Iowa-Sate-Senior-Design-Dec-2021-Team-7/BBGreenZigbeeCape/docs/concepts/ConceptualSketch.png

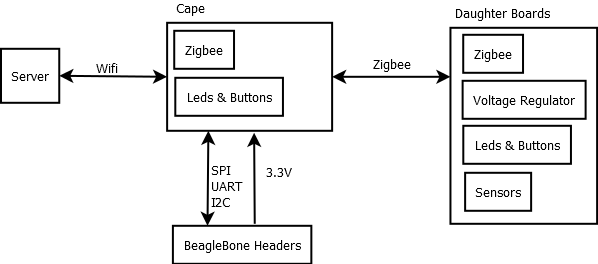
docs/concepts/ConceptualSketch.png
