Iowa-Sate-Senior-Design-Dec-2021-Team-7/BBGreenZigbeeCape/docs/concepts/DetailedHardware.png

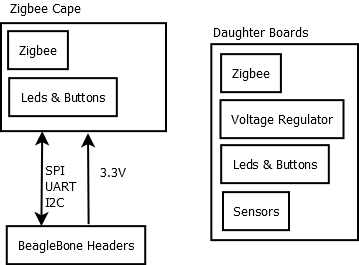
docs/concepts/DetailedHardware.png
