Iowa-Sate-Senior-Design-Dec-2021-Team-7/BBGreenZigbeeCape/hardware/datasheets/Impedance Calcuations/Calculator.PNG

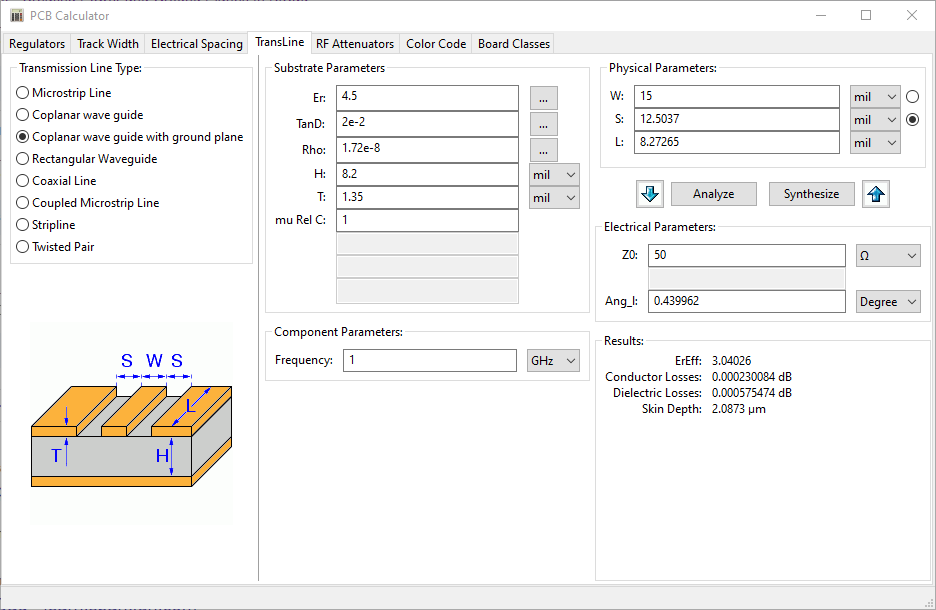
hardware/datasheets/Impedance Calcuations/Calculator.PNG
