Iowa-Sate-Senior-Design-Dec-2021-Team-7/BBGreenZigbeeCape/hardware/datasheets/Impedance Calcuations/StackupInfo.PNG

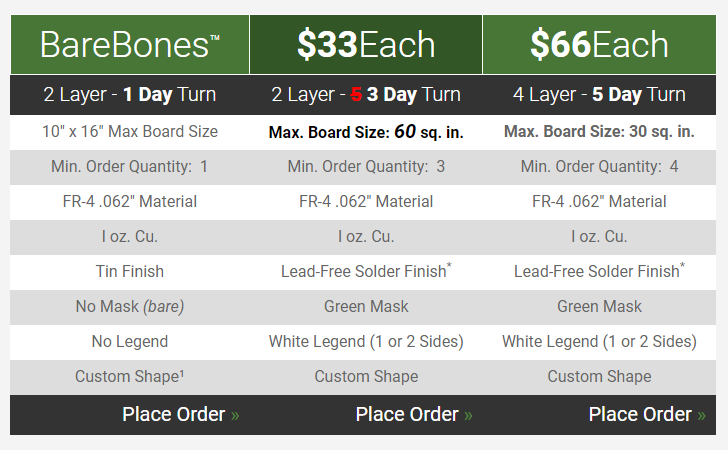
hardware/datasheets/Impedance Calcuations/StackupInfo.PNG
