Iowa-Sate-Senior-Design-Dec-2021-Team-7/BBGreenZigbeeCape/hardware/datasheets/Pictures/Layout.PNG

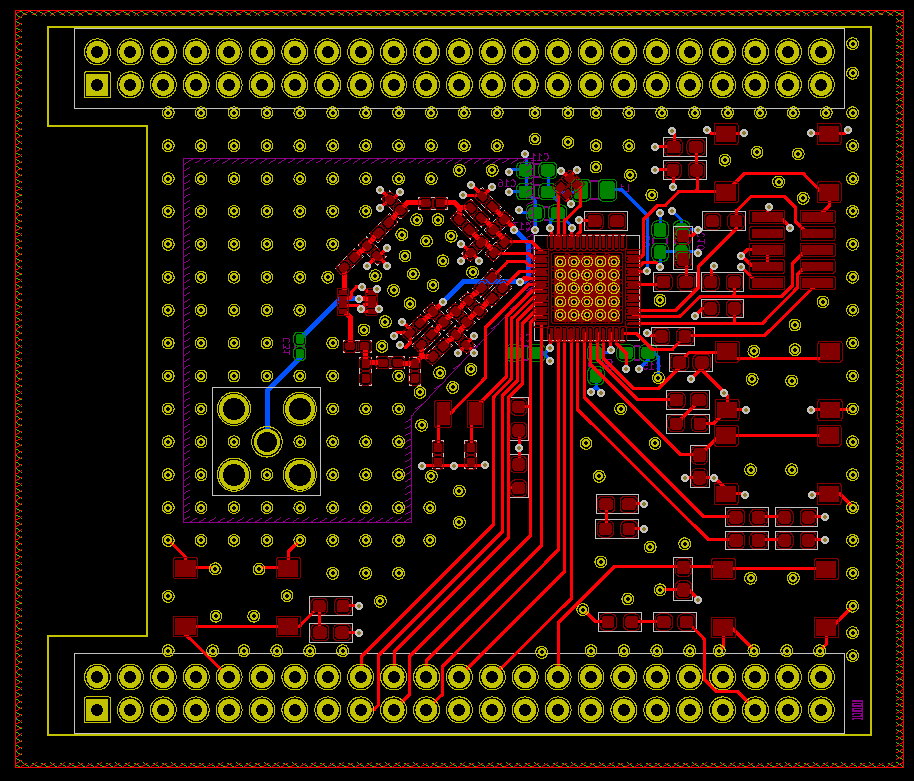
hardware/datasheets/Pictures/Layout.PNG
