Iowa-Sate-Senior-Design-Dec-2021-Team-7/BBGreenZigbeeCape/hardware/datasheets/Pictures/Schematic.PNG

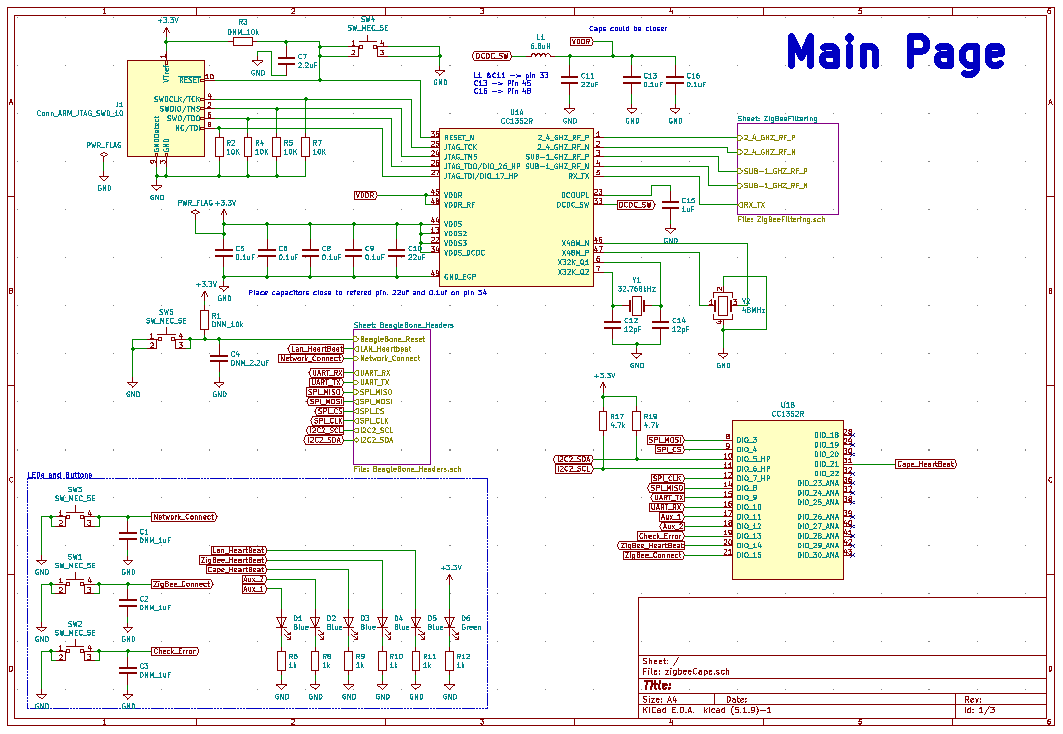
hardware/datasheets/Pictures/Schematic.PNG
