Iowa-Sate-Senior-Design-Dec-2021-Team-7/BBGreenZigbeeCape/hardware/datasheets/Pictures/Switchboard Schematic.PNG

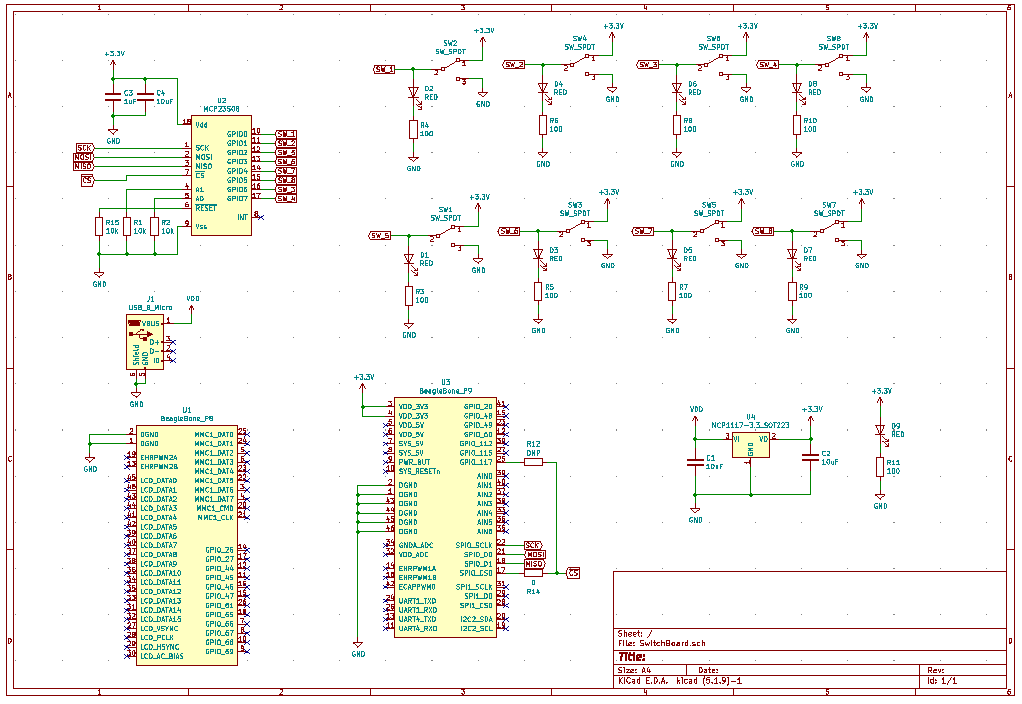
hardware/datasheets/Pictures/Switchboard Schematic.PNG
