Iowa-Sate-Senior-Design-Dec-2021-Team-7/BBGreenZigbeeCape/hardware/datasheets/Pictures/JLC Order.PNG

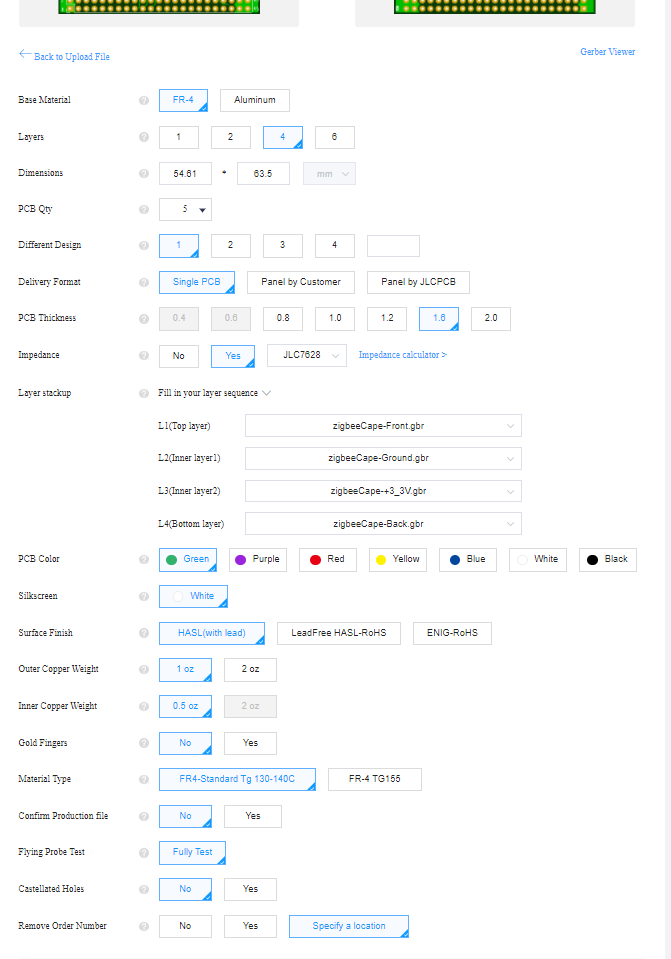
hardware/datasheets/Pictures/JLC Order.PNG
