Iowa-Sate-Senior-Design-Dec-2021-Team-7/BBGreenZigbeeCape/hardware/gerberfiles/ETG Ordering Files/ZigBeeCapeRev2OrderOptions.PNG

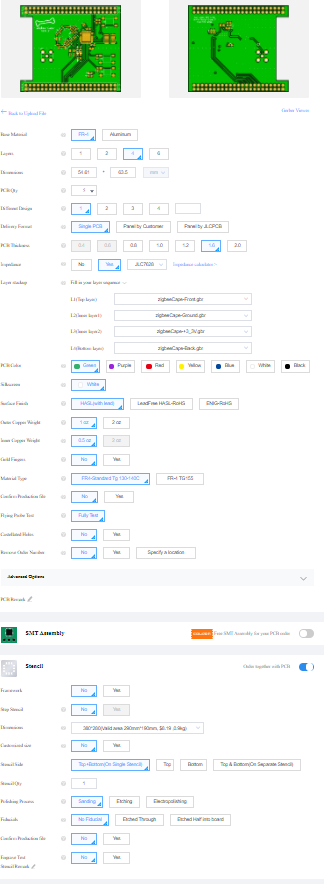
hardware/gerberfiles/ETG Ordering Files/ZigBeeCapeRev2OrderOptions.PNG
