Iowa-Sate-Senior-Design-Dec-2021-Team-7/BBGreenZigbeeCape/hardware/datasheets/Impedance Calcuations/TestBoardLayout.PNG

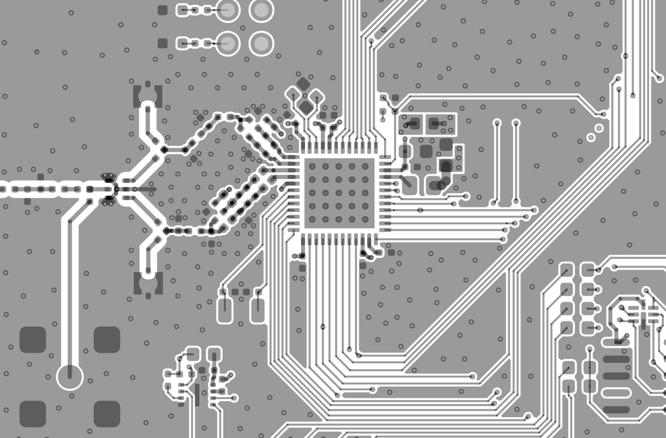
hardware/datasheets/Impedance Calcuations/TestBoardLayout.PNG
