Iowa-Sate-Senior-Design-Dec-2021-Team-7/BBGreenZigbeeCape/firmware/cape/CapeFirmware_P/Application/zcl_samplethermostat.c

/**************************************************************************************************
  Filename:       zcl_samplethermostat.c
  Revised:        $Date: 2014-10-24 16:04:46 -0700 (Fri, 24 Oct 2014) $
  Revision:       $Revision: 40796 $

  Description:    Zigbee Cluster Library - sample device application.

  Copyright 2013 - 2014 Texas Instruments Incorporated. All rights reserved.

  IMPORTANT: Your use of this Software is limited to those specific rights
  granted under the terms of a software license agreement between the user
  who downloaded the software, his/her employer (which must be your employer)
  and Texas Instruments Incorporated (the "License").  You may not use this
  Software unless you agree to abide by the terms of the License. The License
  limits your use, and you acknowledge, that the Software may not be modified,
  copied or distributed unless embedded on a Texas Instruments microcontroller
  or used solely and exclusively in conjunction with a Texas Instruments radio
  frequency transceiver, which is integrated into your product.  Other than for
  the foregoing purpose, you may not use, reproduce, copy, prepare derivative
  works of, modify, distribute, perform, display or sell this Software and/or
  its documentation for any purpose.

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
  Should you have any questions regarding your right to use this Software,
  contact Texas Instruments Incorporated at www.TI.com.
**************************************************************************************************/

/*********************************************************************
  This application implements a ZigBee Thermostat, based on Z-Stack 3.0.

  This application is based on the common sample-application user interface. Please see the main
  comment in zcl_sampleapp_ui.c. The rest of this comment describes only the content specific for
  this sample application.

  Application-specific UI peripherals being used:

  - LEDs:
    LED1:
      - Off: Indicates system is currently off.
      - On: Indicates system is heating.
      - Blinking: Indicates system is cooling.

  Application-specific menu system:
    <SET HEAT TEMP> Changes the heating point temperature
      Up/Down changes the temperature at which heating will activate

    <SET COOL TEMP> Changes the cooling point temperature
      Up/Down changes the temperature at which cooling will activate

    The APP Info line will display the following information:
      [Remote Temperature]
        XXC - current temperature of the remote temperature sensor
        Invalid - thermostat has not yet discovered a temperature sensor
      [System Mode]
        OFF - indicates the system is off
        HEAT - indicates the system is heating
        COOL - indicates the system is cooling
      [Cooling Set Temp]
        XXC - current cooling point temperature
      [Heating Set Temp]
        XXC - current heating point temperature

*********************************************************************/

/*********************************************************************
 * INCLUDES
 */
#include <stdio.h>
#include <stdint.h>
#include <stddef.h>
#include <string.h>

/* POSIX Header files */
#include <pthread.h>
#include <semaphore.h>

/* Driver Header files */
#include <ti/drivers/apps/Button.h>
#include <ti/drivers/apps/LED.h>

#include "rom_jt_154.h"
#include "zcomdef.h"
#include "zcl.h"
#include "zcl_general.h"
#include "zcl_ha.h"
#include "zcl_hvac.h"
#include "zcl_ms.h"
#include "zcl_samplethermostat.h"
#include "bdb_interface.h"

#include "ti_drivers_config.h"
#include "nvintf.h"
#include "zstackmsg.h"
#include "zcl_port.h"

#ifndef CUI_DISABLE
#include "zcl_sampleapps_ui.h"
#include "zcl_sample_app_def.h"
#endif

#include <ti/sysbios/BIOS.h>
#include <ti/sysbios/knl/Semaphore.h>
#include <ti/sysbios/knl/Task.h>
#include <ti/sysbios/knl/Clock.h>
#include "zstackapi.h"
#include "util_timer.h"
#include "mac_util.h"
#include "string.h"

#if !defined (DISABLE_GREENPOWER_BASIC_PROXY) && (ZG_BUILD_RTR_TYPE)
#include "gp_common.h"
#endif

#if defined (ENABLE_GREENPOWER_COMBO_BASIC)
#include "gp_sink.h"
#endif


/*********************************************************************
 * MACROS
 */

/*********************************************************************
 * CONSTANTS
 */
#define THREADSTACKSIZE    1024

/*********************************************************************
 * TYPEDEFS
 */

/*********************************************************************
 * GLOBAL VARIABLES
 */
LED_Handle gRedLedHandle;

/*********************************************************************
 * GLOBAL FUNCTIONS
 */
extern void bb_uartInit();
extern void *bb_uartRead_thread(void *arg0);
extern int_fast32_t bb_uartRead(void *buf, size_t maxCount);
extern int_fast32_t bb_uartWrite(void *buf, size_t count);

/*********************************************************************
 * LOCAL VARIABLES
 */
// Semaphore used to post events to the application thread
static Semaphore_Handle appSemHandle;
static Semaphore_Struct appSem;

/* App service ID used for messaging with stack service task */
static uint8_t  appServiceTaskId;
/* App service task events, set by the stack service task when sending a message */
static uint32_t appServiceTaskEvents;
static endPointDesc_t  zclSampleThermostatEpDesc = {0};

#if ZG_BUILD_ENDDEVICE_TYPE
static Clock_Handle EndDeviceRejoinClkHandle;
static Clock_Struct EndDeviceRejoinClkStruct;
#endif

// Passed in function pointers to the NV driver
static NVINTF_nvFuncts_t *pfnZdlNV = NULL;

#ifndef CUI_DISABLE
static uint16_t zclSampleThermostat_BdbCommissioningModes;
#endif

#ifdef BDB_REPORTING
#if BDBREPORTING_MAX_ANALOG_ATTR_SIZE == 8
  uint8_t reportableChange[] = {0x2C, 0x01, 0x00, 0x00, 0x00, 0x00, 0x00, 0x00}; // 0x2C01 is 300 in int16_t
#endif
#if BDBREPORTING_MAX_ANALOG_ATTR_SIZE == 4
  uint8_t reportableChange[] = {0x2C, 0x01, 0x00, 0x00}; // 0x2C01 is 300 in int16_t
#endif
#if BDBREPORTING_MAX_ANALOG_ATTR_SIZE == 2
  uint8_t reportableChange[] = {0x2C, 0x01}; // 0x2C01 is 300 in int16_t
#endif
#endif

#ifndef CUI_DISABLE
CONST char zclSampleThermostat_appStr[] = APP_TITLE_STR;
CUI_clientHandle_t gCuiHandle;
static uint32_t gSampleThermostatInfoLine1;
static uint32_t gSampleThermostatInfoLine2;
#endif
/*********************************************************************
 * LOCAL FUNCTIONS
 */

static void zclSampleThermostat_initialization(void);
static void zclSampleThermostat_process_loop(void);
static void zclSampleThermostat_initParameters(void);
static void zclSampleThermostat_processZStackMsgs(zstackmsg_genericReq_t *pMsg);
static void SetupZStackCallbacks(void);
static void zclSampleThermostat_processAfIncomingMsgInd(zstack_afIncomingMsgInd_t *pInMsg);
static void zclSampleThermostat_initializeClocks(void);
#if ZG_BUILD_ENDDEVICE_TYPE
static void zclSampleThermostat_processEndDeviceRejoinTimeoutCallback(UArg a0);
#endif

static void zclSampleThermostat_Init( void );
static void zclSampleThermostat_BasicResetCB( void );

#ifndef CUI_DISABLE
static void zclSampleThermostat_RemoveAppNvmData(void);
static void zclSampleThermostat_processKey(uint8_t key, Button_EventMask buttonEvents);
static void zclSampleThermostat_InitializeStatusLine(CUI_clientHandle_t gCuiHandle);
static void zclSampleThermostat_UpdateStatusLine(void);
#endif

static ZStatus_t zclSampleThermostat_SetpointRaiseLowerCB(zclCmdThermostatSetpointRaiseLowerPayload_t *pCmd);
#ifdef MT_APP_FUNC
static void zclSampleThermostat_ProcessAppMsg( uint8_t srcEP, uint8_t len, uint8_t *msg );
static void zclSampleThermostat_ProcessFoundationMsg( afAddrType_t *dstAddr, uint16_t clusterID,
                                                      zclFrameHdr_t *hdr, zclParseCmd_t *pParseCmd );
#endif

static void zclSampleThermostat_ProcessCommissioningStatus(bdbCommissioningModeMsg_t* bdbCommissioningModeMsg);


// app display functions
void zclSampleThermostat_UiDisplayRefresh(void);
void zclSampleThermostat_UiDisplayMainMode(void);
void zclSampleThermostat_UiDisplayHeatMode(void);
void zclSampleThermostat_UiDisplayCoolMode(void);
void zclSampleThermostat_UiDisplayHelpMode(void);



// Functions to process ZCL Foundation incoming Command/Response messages
static uint8_t zclSampleThermostat_ProcessIncomingMsg( zclIncoming_t *pInMsg);
#ifdef ZCL_READ
static uint8_t zclSampleThermostat_ProcessInReadRspCmd( zclIncoming_t *pInMsg );
#endif
#ifdef ZCL_WRITE
static uint8_t zclSampleThermostat_ProcessInWriteRspCmd( zclIncoming_t *pInMsg );
#endif
#ifdef ZCL_REPORT_DESTINATION_DEVICE
static void zclSampleThermostat_ProcessInReportCmd( zclIncoming_t *pInMsg );
#endif  // ZCL_REPORT_DESTINATION_DEVICE
static uint8_t zclSampleThermostat_ProcessInDefaultRspCmd( zclIncoming_t *pInMsg );

static void zclSampleThermostat_UpdateLedState(void);

#if defined (ENABLE_GREENPOWER_COMBO_BASIC)
static void zclSampleThermostat_GPSink_Identify(zclGpNotification_t *zclGpNotification);
static void zclSampleThermostat_GPSink_ProcessReport(zclGpNotification_t *zclGpNotification);
#endif

/*********************************************************************
 * CONSTANTS
 */

/*********************************************************************
 * ZCL General Profile Callback table
 */
static zclGeneral_AppCallbacks_t zclSampleThermostat_CmdCallbacks =
{
  zclSampleThermostat_BasicResetCB,            // Basic Cluster Reset command
  NULL,                                        // Identfiy cmd
  NULL,                                        // Identify Query command
  NULL,                                        // Identify Query Response command
  NULL,                                        // Identify Trigger Effect command
#ifdef ZCL_ON_OFF
  NULL,                                        // On/Off cluster command
  NULL,                                        // On/Off cluster enhanced command Off with Effect
  NULL,                                        // On/Off cluster enhanced command On with Recall Global Scene
  NULL,                                        // On/Off cluster enhanced command On with Timed Off
#endif
#ifdef ZCL_LEVEL_CTRL
  NULL,                                        // Level Control Move to Level command
  NULL,                                        // Level Control Move command
  NULL,                                        // Level Control Step command
  NULL,                                        // Level Control Stop command
  NULL,                                        // Level Control Move to Closest Frequency Command
#endif
#ifdef ZCL_GROUPS
  NULL,                                        // Group Response commands
#endif
#ifdef ZCL_SCENES
  NULL,                                        // Scene Store Request command
  NULL,                                        // Scene Recall Request command
  NULL,                                        // Scene Response command
#endif
#ifdef ZCL_ALARMS
  NULL,                                        // Alarm (Response) commands
#endif
#ifdef SE_UK_EXT
  NULL,                                        // Get Event Log command
  NULL,                                        // Publish Event Log command
#endif
  NULL,                                        // RSSI Location command
  NULL                                         // RSSI Location Response command
};


static zclHVAC_AppCallbacks_t zclSampleThermostat_HVAC_CmdCallbacks =
{
  zclSampleThermostat_SetpointRaiseLowerCB,    //SetpointRaiseLower
  NULL,    //SetWeeklySchedule
  NULL,    //GetWeeklySchedule
  NULL,    //ClearWeeklySchedule
  NULL,    //GetRelayStatusLog
  NULL,    //GetWeeklyScheduleRsp
  NULL,    //GetRelayStatusLogRsp
};

#if defined (ENABLE_GREENPOWER_COMBO_BASIC)

GpSink_AppCallbacks_t zclSampleThermostat_GpSink_AppCallbacks =
{
#ifdef ZCL_IDENTIFY
    zclSampleThermostat_GPSink_Identify,     //IdentifyCmd;
#endif
#ifdef ZCL_SCENES
    NULL,                               //RecallSceneCmd;
    NULL,                               //StoreSceneCmd;
#endif
#ifdef ZCL_ON_OFF
    NULL,          //OffCmd;
    NULL,           //OnCmd;
    NULL,       //ToggleCmd;
#endif
#ifdef ZCL_LEVEL_CTRL
    NULL,                               //LevelControlStopCmd;
    NULL,                               //MoveUpCmd;
    NULL,                               //MoveDownCmd;
    NULL,                               //StepUpCmd;
    NULL,                               //StepDownCmd;
    NULL,                               //MoveUpWithOnOffCmd;
    NULL,                               //MoveDownWithOnOffCmd;
    NULL,                               //StepUpWithOnOffCmd;
    NULL,                               //StepDownWithOnOffCmd;
#endif
    NULL,                               //MoveHueStopCmd;
    NULL,                               //MoveHueUpCmd;
    NULL,                               //MoveHueDownCmd;
    NULL,                               //StepHueUpCmd;
    NULL,                               //StepHueDownCmd;
    NULL,                               //MoveSaturationStopCmd;
    NULL,                               //MoveSaturationUpCmd;
    NULL,                               //MoveSaturationDownCmd;
    NULL,                               //StepSaturationUpCmd;
    NULL,                               //StepSaturationDownCmd;
    NULL,                               //MoveColorCmd;
    NULL,                               //StepColorCmd;
#ifdef ZCL_DOORLOCK
    NULL,                               //LockDoorCmd;
    NULL,                               //UnlockDoorCmd;
#endif
    zclSampleThermostat_GPSink_ProcessReport,                               //AttributeReportingCmd;
    NULL,                               //MfrSpecificReportingCmd;
    NULL,                               //MultiClusterReportingCmd;
    NULL,                               //MfrSpecificMultiReportingCmd;
    NULL,                               //RequestAttributesCmd;
    NULL,                               //ReadAttributeRspCmd;
    NULL,                               //zclTunnelingCmd;
};
#endif

uint16_t data_light_disp0 = 0;
uint16_t data_light_disp1 = 0;
uint16_t id_light_disp0 = 0;
uint16_t id_light_disp1 = 0;

/*******************************************************************************
 * @fn          sampleApp_task
 *
 * @brief       Application task entry point for the Z-Stack
 *              Sample Application
 *
 * @param       pfnNV - pointer to the NV functions
 *
 * @return      none
 */
void sampleApp_task(NVINTF_nvFuncts_t *pfnNV)
{
  // Save and register the function pointers to the NV drivers
  pfnZdlNV = pfnNV;
  zclport_registerNV(pfnZdlNV, ZCL_PORT_SCENE_TABLE_NV_ID);

  // Initialize application
  zclSampleThermostat_initialization();

  // No return from task process
  zclSampleThermostat_process_loop();
}



/*******************************************************************************
 * @fn          zclSampleThermostat_initialization
 *
 * @brief       Initialize the application
 *
 * @param       none
 *
 * @return      none
 */
static void zclSampleThermostat_initialization(void)
{
    /* Initialize user clocks */
    zclSampleThermostat_initializeClocks();

    /* create semaphores for messages / events
     */
    Semaphore_Params semParam;
    Semaphore_Params_init(&semParam);
    semParam.mode = ti_sysbios_knl_Semaphore_Mode_COUNTING;
    Semaphore_construct(&appSem, 0, &semParam);
    appSemHandle = Semaphore_handle(&appSem);

    appServiceTaskId = OsalPort_registerTask(Task_self(), appSemHandle, &appServiceTaskEvents);

    //Initialize stack
    zclSampleThermostat_Init();
}



/*******************************************************************************
 * @fn      SetupZStackCallbacks
 *
 * @brief   Setup the Zstack Callbacks wanted
 *
 * @param   none
 *
 * @return  none
 */
static void SetupZStackCallbacks(void)
{
    zstack_devZDOCBReq_t zdoCBReq = {0};

    // Register for Callbacks, turn on:
    //  Device State Change,
    //  ZDO Match Descriptor Response,
    zdoCBReq.has_devStateChange = true;
    zdoCBReq.devStateChange = true;

    (void)Zstackapi_DevZDOCBReq(appServiceTaskId, &zdoCBReq);
}



/*********************************************************************
 * @fn          zclSampleThermostat_Init
 *
 * @brief       Initialization function for the zclGeneral layer.
 *
 * @param       none
 *
 * @return      none
 */
static void zclSampleThermostat_Init( void )
{

#ifdef BDB_REPORTING
  zstack_bdbRepAddAttrCfgRecordDefaultToListReq_t  Req = {0};
#endif

  //Register Endpoint
  zclSampleThermostatEpDesc.endPoint = SAMPLETHERMOSTAT_ENDPOINT;
  zclSampleThermostatEpDesc.simpleDesc = &zclSampleThermostat_SimpleDesc;
  zclport_registerEndpoint(appServiceTaskId, &zclSampleThermostatEpDesc);

#if defined (ENABLE_GREENPOWER_COMBO_BASIC)
    zclGp_RegisterCBForGPDCommand(&zclSampleThermostat_GpSink_AppCallbacks);
#endif


  // Register the ZCL General Cluster Library callback functions
  zclGeneral_RegisterCmdCallbacks( SAMPLETHERMOSTAT_ENDPOINT, &zclSampleThermostat_CmdCallbacks );

  // Register the ZCL HVAC Cluster Library callback functions
  zclHVAC_RegisterCmdCallbacks(SAMPLETHERMOSTAT_ENDPOINT,  &zclSampleThermostat_HVAC_CmdCallbacks );

  // Register the Application to receive the unprocessed Foundation command/response messages
  zclport_registerZclHandleExternal(SAMPLETHERMOSTAT_ENDPOINT, zclSampleThermostat_ProcessIncomingMsg);

  // Register the application's attribute list and reset to default values
  zclSampleThermostat_ResetAttributesToDefaultValues();
  zcl_registerAttrList( SAMPLETHERMOSTAT_ENDPOINT, zclSampleThermostat_NumAttributes, zclSampleThermostat_Attrs );

  //Write the bdb initialization parameters
  zclSampleThermostat_initParameters();

  //Setup ZDO callbacks
  SetupZStackCallbacks();

#if defined ( BDB_TL_INITIATOR )
  zclSampleThermostat_BdbCommissioningModes |= BDB_COMMISSIONING_MODE_INITIATOR_TL;
#endif

#if !defined (DISABLE_GREENPOWER_BASIC_PROXY) && (ZG_BUILD_RTR_TYPE)
  gp_endpointInit(appServiceTaskId);
#endif

#ifdef BDB_REPORTING
    //Adds the default configuration values for the reportable attributes of the ZCL_CLUSTER_ID_HVAC_THERMOSTAT cluster, for endpoint SAMPLETHERMOSTAT_ENDPOINT
    //Default maxReportingInterval value is 10 seconds
    //Default minReportingInterval value is 3 seconds
    //Default reportChange value is 300 (3 degrees)

    Req.attrID = ATTRID_THERMOSTAT_LOCAL_TEMPERATURE;
    Req.cluster = ZCL_CLUSTER_ID_HVAC_THERMOSTAT;
    Req.endpoint = SAMPLETHERMOSTAT_ENDPOINT;
    Req.maxReportInt = 10;
    Req.minReportInt =  3;
    OsalPort_memcpy(&Req.reportableChange,reportableChange,BDBREPORTING_MAX_ANALOG_ATTR_SIZE);
    Zstackapi_bdbRepAddAttrCfgRecordDefaultToListReq(appServiceTaskId, &Req);
#endif


#ifndef CUI_DISABLE
  // set up default application BDB commissioning modes based on build type
  if(ZG_BUILD_COORDINATOR_TYPE && ZG_DEVICE_COORDINATOR_TYPE)
  {
    zclSampleThermostat_BdbCommissioningModes = BDB_COMMISSIONING_MODE_NWK_FORMATION | BDB_COMMISSIONING_MODE_NWK_STEERING | BDB_COMMISSIONING_MODE_FINDING_BINDING;
  }
  else if (ZG_BUILD_JOINING_TYPE && ZG_DEVICE_JOINING_TYPE)
  {
    zclSampleThermostat_BdbCommissioningModes = BDB_COMMISSIONING_MODE_NWK_STEERING | BDB_COMMISSIONING_MODE_FINDING_BINDING;
  }


  gCuiHandle = UI_Init( appServiceTaskId,                     // Application Task ID
            &appServiceTaskEvents,                // The events processed by the sample application
            appSemHandle,                         // Semaphore to post the events in the application thread
            &zclSampleThermostat_IdentifyTime,
            &zclSampleThermostat_BdbCommissioningModes,   // A pointer to the application's bdbCommissioningModes
            zclSampleThermostat_appStr,                   // A pointer to the app-specific name string
            zclSampleThermostat_processKey,               // A pointer to the app-specific key process function
            zclSampleThermostat_RemoveAppNvmData          // A pointer to the app-specific NV Item reset function
            );

  //Request the Red LED for App
    LED_Params ledParams;
    LED_Params_init(&ledParams);
    gRedLedHandle = LED_open(CONFIG_LED_RED, &ledParams);

   // initialize bb uart handle and connection
   bb_uartInit();

   /*
    * BB uart pthread creation
    */
   pthread_t           thread_bb_uartRead;
   pthread_attr_t      thread_bb_uartRead_attrs;
   struct sched_param  priParam;
   int                 retc;

   /* Initialize the attributes structure with default values */
   pthread_attr_init(&thread_bb_uartRead_attrs);
   /* Set priority, detach state, and stack size attributes */
   priParam.sched_priority = 1;
   retc = pthread_attr_setschedparam(&thread_bb_uartRead_attrs, &priParam);
   retc |= pthread_attr_setdetachstate(&thread_bb_uartRead_attrs, PTHREAD_CREATE_DETACHED);
   retc |= pthread_attr_setstacksize(&thread_bb_uartRead_attrs, THREADSTACKSIZE);
   if (retc != 0) {
       /* failed to set attributes */
       LED_startBlinking(gRedLedHandle, 3000, LED_BLINK_FOREVER);
   }

   // create read thread
   retc = pthread_create(&thread_bb_uartRead, &thread_bb_uartRead_attrs, bb_uartRead_thread, NULL);
   if (retc != 0) {
       /* pthread_create() failed */
       LED_startBlinking(gRedLedHandle, 1000, LED_BLINK_FOREVER);
   }

  //Initialize the SampleDoorLock UI status line
  zclSampleThermostat_InitializeStatusLine(gCuiHandle);
#endif
#if !defined (DISABLE_GREENPOWER_BASIC_PROXY) && (ZG_BUILD_RTR_TYPE)
  app_Green_Power_Init(appServiceTaskId, &appServiceTaskEvents, appSemHandle, SAMPLEAPP_PROCESS_GP_DATA_SEND_EVT,
                       SAMPLEAPP_PROCESS_GP_EXPIRE_DUPLICATE_EVT, SAMPLEAPP_PROCESS_GP_TEMP_MASTER_EVT);
#endif

#ifndef CUI_DISABLE
  UI_UpdateBdbStatusLine(NULL);
#endif

  // Call BDB initialization. Should be called once from application at startup to restore
  // previous network configuration, if applicable.
  zstack_bdbStartCommissioningReq_t zstack_bdbStartCommissioningReq;
  zstack_bdbStartCommissioningReq.commissioning_mode = 0;
  Zstackapi_bdbStartCommissioningReq(appServiceTaskId,&zstack_bdbStartCommissioningReq);
}

#ifndef CUI_DISABLE
/*********************************************************************
 * @fn          zclSampleThermostat_RemoveAppNvmData
 *
 * @brief       Callback when Application performs reset to Factory New Reset.
 *              Application must restore the application to default values
 *
 * @param       none
 *
 * @return      none
 */
static void zclSampleThermostat_RemoveAppNvmData(void)
{

}
#endif

static void zclSampleThermostat_initParameters(void)
{
    zstack_bdbSetAttributesReq_t zstack_bdbSetAttrReq;

    zstack_bdbSetAttrReq.bdbCommissioningGroupID              = BDB_DEFAULT_COMMISSIONING_GROUP_ID;
    zstack_bdbSetAttrReq.bdbPrimaryChannelSet                 = BDB_DEFAULT_PRIMARY_CHANNEL_SET;
    zstack_bdbSetAttrReq.bdbScanDuration                      = BDB_DEFAULT_SCAN_DURATION;
    zstack_bdbSetAttrReq.bdbSecondaryChannelSet               = BDB_DEFAULT_SECONDARY_CHANNEL_SET;
    zstack_bdbSetAttrReq.has_bdbCommissioningGroupID          = TRUE;
    zstack_bdbSetAttrReq.has_bdbPrimaryChannelSet             = TRUE;
    zstack_bdbSetAttrReq.has_bdbScanDuration                  = TRUE;
    zstack_bdbSetAttrReq.has_bdbSecondaryChannelSet           = TRUE;
#if (ZG_BUILD_COORDINATOR_TYPE)
    zstack_bdbSetAttrReq.has_bdbJoinUsesInstallCodeKey        = TRUE;
    zstack_bdbSetAttrReq.has_bdbTrustCenterNodeJoinTimeout    = TRUE;
    zstack_bdbSetAttrReq.has_bdbTrustCenterRequireKeyExchange = TRUE;
    zstack_bdbSetAttrReq.bdbJoinUsesInstallCodeKey            = BDB_DEFAULT_JOIN_USES_INSTALL_CODE_KEY;
    zstack_bdbSetAttrReq.bdbTrustCenterNodeJoinTimeout        = BDB_DEFAULT_TC_NODE_JOIN_TIMEOUT;
    zstack_bdbSetAttrReq.bdbTrustCenterRequireKeyExchange     = BDB_DEFAULT_TC_REQUIRE_KEY_EXCHANGE;
#endif
#if (ZG_BUILD_JOINING_TYPE)
    zstack_bdbSetAttrReq.has_bdbTCLinkKeyExchangeAttemptsMax  = TRUE;
    zstack_bdbSetAttrReq.has_bdbTCLinkKeyExchangeMethod       = TRUE;
    zstack_bdbSetAttrReq.bdbTCLinkKeyExchangeAttemptsMax      = BDB_DEFAULT_TC_LINK_KEY_EXCHANGE_ATTEMPS_MAX;
    zstack_bdbSetAttrReq.bdbTCLinkKeyExchangeMethod           = BDB_DEFAULT_TC_LINK_KEY_EXCHANGE_METHOD;
#endif

    Zstackapi_bdbSetAttributesReq(appServiceTaskId, &zstack_bdbSetAttrReq);
}

/*******************************************************************************
 * @fn      zclSampleThermostat_initializeClocks
 *
 * @brief   Initialize Clocks
 *
 * @param   none
 *
 * @return  none
 */
static void zclSampleThermostat_initializeClocks(void)
{
#if ZG_BUILD_ENDDEVICE_TYPE
    // Initialize the timers needed for this application
    EndDeviceRejoinClkHandle = UtilTimer_construct(
    &EndDeviceRejoinClkStruct,
    zclSampleThermostat_processEndDeviceRejoinTimeoutCallback,
    SAMPLEAPP_END_DEVICE_REJOIN_DELAY,
    0, false, 0);
#endif

}

#if ZG_BUILD_ENDDEVICE_TYPE
/*******************************************************************************
 * @fn      zclSampleThermostat_processEndDeviceRejoinTimeoutCallback
 *
 * @brief   Timeout handler function
 *
 * @param   a0 - ignored
 *
 * @return  none
 */
static void zclSampleThermostat_processEndDeviceRejoinTimeoutCallback(UArg a0)
{
    (void)a0; // Parameter is not used

    appServiceTaskEvents |= SAMPLEAPP_END_DEVICE_REJOIN_EVT;

    // Wake up the application thread when it waits for clock event
    Semaphore_post(appSemHandle);
}
#endif


/*******************************************************************************
 * @fn      zclSampleThermostat_process_loop
 *
 * @brief   Application task processing start.
 *
 * @param   none
 *
 * @return  void
 */
static void zclSampleThermostat_process_loop(void)
{
    /* Forever loop */
    for(;;)
    {
        zstackmsg_genericReq_t *pMsg = NULL;
        bool msgProcessed = FALSE;

        /* Wait for response message */
        if(Semaphore_pend(appSemHandle, BIOS_WAIT_FOREVER ))
        {
            /* Retrieve the response message */
            if( (pMsg = (zstackmsg_genericReq_t*) OsalPort_msgReceive( appServiceTaskId )) != NULL)
            {
                /* Process the message from the stack */
                zclSampleThermostat_processZStackMsgs(pMsg);
                // Free any separately allocated memory
                msgProcessed = Zstackapi_freeIndMsg(pMsg);
            }

            if((msgProcessed == FALSE) && (pMsg != NULL))
            {
                OsalPort_msgDeallocate((uint8_t*)pMsg);
            }

#ifndef CUI_DISABLE
            //Process the events that the UI may have
            zclsampleApp_ui_event_loop();
#endif

#if !defined (DISABLE_GREENPOWER_BASIC_PROXY) && (ZG_BUILD_RTR_TYPE)
            if(appServiceTaskEvents & SAMPLEAPP_PROCESS_GP_DATA_SEND_EVT)
            {
                if(zgGP_ProxyCommissioningMode == TRUE)
                {
                  zcl_gpSendCommissioningNotification();
                }
                else
                {
                  zcl_gpSendNotification();
                }
                appServiceTaskEvents &= ~SAMPLEAPP_PROCESS_GP_DATA_SEND_EVT;
            }

            if(appServiceTaskEvents & SAMPLEAPP_PROCESS_GP_EXPIRE_DUPLICATE_EVT)
            {
                gp_expireDuplicateFiltering();
                appServiceTaskEvents &= ~SAMPLEAPP_PROCESS_GP_EXPIRE_DUPLICATE_EVT;
            }

            if(appServiceTaskEvents & SAMPLEAPP_PROCESS_GP_TEMP_MASTER_EVT)
            {
                gp_returnOperationalChannel();
                appServiceTaskEvents &= ~SAMPLEAPP_PROCESS_GP_TEMP_MASTER_EVT;
            }
#endif

#if ZG_BUILD_ENDDEVICE_TYPE
            if ( appServiceTaskEvents & SAMPLEAPP_END_DEVICE_REJOIN_EVT )
            {
              zstack_bdbRecoverNwkRsp_t zstack_bdbRecoverNwkRsp;

              Zstackapi_bdbRecoverNwkReq(appServiceTaskId,&zstack_bdbRecoverNwkRsp);

              appServiceTaskEvents &= ~SAMPLEAPP_END_DEVICE_REJOIN_EVT;
            }
#endif

#ifndef CUI_DISABLE
            //Update status line
            zclSampleThermostat_UpdateStatusLine();
#endif
            zclSampleThermostat_UpdateLedState();
        }
    }

}




/*******************************************************************************
 * @fn      zclSampleThermostat_processZStackMsgs
 *
 * @brief   Process event from Stack
 *
 * @param   pMsg - pointer to incoming ZStack message to process
 *
 * @return  void
 */
static void zclSampleThermostat_processZStackMsgs(zstackmsg_genericReq_t *pMsg)
{
    switch(pMsg->hdr.event)
    {
        case zstackmsg_CmdIDs_BDB_NOTIFICATION:
            {
                zstackmsg_bdbNotificationInd_t *pInd;
                pInd = (zstackmsg_bdbNotificationInd_t*)pMsg;
                zclSampleThermostat_ProcessCommissioningStatus(&(pInd->Req));
            }
            break;

        case zstackmsg_CmdIDs_BDB_IDENTIFY_TIME_CB:
            {
#ifndef CUI_DISABLE
                zstackmsg_bdbIdentifyTimeoutInd_t *pInd;
                pInd = (zstackmsg_bdbIdentifyTimeoutInd_t*) pMsg;
                uiProcessIdentifyTimeChange(&(pInd->EndPoint));
#endif
            }
            break;

        case zstackmsg_CmdIDs_BDB_BIND_NOTIFICATION_CB:
            {
#ifndef CUI_DISABLE
                zstackmsg_bdbBindNotificationInd_t *pInd;
                pInd = (zstackmsg_bdbBindNotificationInd_t*) pMsg;
                uiProcessBindNotification(&(pInd->Req));
#endif
            }
            break;

        case zstackmsg_CmdIDs_AF_INCOMING_MSG_IND:
            {
                // Process incoming data messages
                zstackmsg_afIncomingMsgInd_t *pInd;
                pInd = (zstackmsg_afIncomingMsgInd_t *)pMsg;
                zclSampleThermostat_processAfIncomingMsgInd( &(pInd->req) );
            }
            break;

#if (ZG_BUILD_JOINING_TYPE)
        case zstackmsg_CmdIDs_BDB_CBKE_TC_LINK_KEY_EXCHANGE_IND:
        {
          zstack_bdbCBKETCLinkKeyExchangeAttemptReq_t zstack_bdbCBKETCLinkKeyExchangeAttemptReq;
          /* Z3.0 has not defined CBKE yet, so lets attempt default TC Link Key exchange procedure
           * by reporting CBKE failure.
           */

          zstack_bdbCBKETCLinkKeyExchangeAttemptReq.didSuccess = FALSE;

          Zstackapi_bdbCBKETCLinkKeyExchangeAttemptReq(appServiceTaskId,
                                                       &zstack_bdbCBKETCLinkKeyExchangeAttemptReq);
        }
        break;

        case zstackmsg_CmdIDs_BDB_FILTER_NWK_DESCRIPTOR_IND:

         /*   User logic to remove networks that do not want to join
          *   Networks to be removed can be released with Zstackapi_bdbNwkDescFreeReq
          */

          Zstackapi_bdbFilterNwkDescComplete(appServiceTaskId);
        break;

#endif
        case zstackmsg_CmdIDs_DEV_STATE_CHANGE_IND:
#ifndef CUI_DISABLE
          {
            // The ZStack Thread is indicating a State change
            zstackmsg_devStateChangeInd_t *pInd =
                (zstackmsg_devStateChangeInd_t *)pMsg;
                  UI_DeviceStateUpdated(&(pInd->req));
          }
#endif
        break;



        /*
         * These are messages/indications from ZStack that this
         * application doesn't process.  These message can be
         * processed by your application, remove from this list and
         * process them here in this switch statement.
         */

#if !defined (DISABLE_GREENPOWER_BASIC_PROXY) && (ZG_BUILD_RTR_TYPE)
          case zstackmsg_CmdIDs_GP_DATA_IND:
          {
              zstackmsg_gpDataInd_t *pInd;
              pInd = (zstackmsg_gpDataInd_t*)pMsg;
              gp_processDataIndMsg( &(pInd->Req) );
          }
          break;

          case zstackmsg_CmdIDs_GP_SECURITY_REQ:
          {
              zstackmsg_gpSecReq_t *pInd;
              pInd = (zstackmsg_gpSecReq_t*)pMsg;
              gp_processSecRecMsg( &(pInd->Req) );
          }
          break;

          case zstackmsg_CmdIDs_GP_CHECK_ANNCE:
          {
              zstackmsg_gpCheckAnnounce_t *pInd;
              pInd = (zstackmsg_gpCheckAnnounce_t*)pMsg;
              gp_processCheckAnnceMsg( &(pInd->Req) );
          }
          break;

          case zstackmsg_CmdIDs_GP_COMMISSIONING_MODE_IND:
#ifndef CUI_DISABLE
          {
            zstackmsg_gpCommissioningModeInd_t *pInd;
            pInd = (zstackmsg_gpCommissioningModeInd_t*)pMsg;
            UI_SetGPPCommissioningMode( &(pInd->Req) );
          }
#endif
          break;
#endif

#ifdef BDB_TL_TARGET
        case zstackmsg_CmdIDs_BDB_TOUCHLINK_TARGET_ENABLE_IND:
        {
          zstackmsg_bdbTouchLinkTargetEnableInd_t *pInd =
            (zstackmsg_bdbTouchLinkTargetEnableInd_t*)pMsg;

          uiProcessTouchlinkTargetEnable(pInd->Enable);
        }
        break;
#endif
        case zstackmsg_CmdIDs_BDB_TC_LINK_KEY_EXCHANGE_NOTIFICATION_IND:
        case zstackmsg_CmdIDs_AF_DATA_CONFIRM_IND:
        case zstackmsg_CmdIDs_ZDO_DEVICE_ANNOUNCE:
        case zstackmsg_CmdIDs_ZDO_NWK_ADDR_RSP:
        case zstackmsg_CmdIDs_DEV_PERMIT_JOIN_IND:
        case zstackmsg_CmdIDs_ZDO_IEEE_ADDR_RSP:
        case zstackmsg_CmdIDs_ZDO_NODE_DESC_RSP:
        case zstackmsg_CmdIDs_ZDO_POWER_DESC_RSP:
        case zstackmsg_CmdIDs_ZDO_SIMPLE_DESC_RSP:
        case zstackmsg_CmdIDs_ZDO_ACTIVE_EP_RSP:
        case zstackmsg_CmdIDs_ZDO_COMPLEX_DESC_RSP:
        case zstackmsg_CmdIDs_ZDO_USER_DESC_RSP:
        case zstackmsg_CmdIDs_ZDO_USER_DESC_SET_RSP:
        case zstackmsg_CmdIDs_ZDO_SERVER_DISC_RSP:
        case zstackmsg_CmdIDs_ZDO_END_DEVICE_BIND_RSP:
        case zstackmsg_CmdIDs_ZDO_BIND_RSP:
        case zstackmsg_CmdIDs_ZDO_UNBIND_RSP:
        case zstackmsg_CmdIDs_ZDO_MGMT_NWK_DISC_RSP:
        case zstackmsg_CmdIDs_ZDO_MGMT_LQI_RSP:
        case zstackmsg_CmdIDs_ZDO_MGMT_RTG_RSP:
        case zstackmsg_CmdIDs_ZDO_MGMT_BIND_RSP:
        case zstackmsg_CmdIDs_ZDO_MGMT_LEAVE_RSP:
        case zstackmsg_CmdIDs_ZDO_MGMT_DIRECT_JOIN_RSP:
        case zstackmsg_CmdIDs_ZDO_MGMT_PERMIT_JOIN_RSP:
        case zstackmsg_CmdIDs_ZDO_MGMT_NWK_UPDATE_NOTIFY:
        case zstackmsg_CmdIDs_ZDO_SRC_RTG_IND:
        case zstackmsg_CmdIDs_ZDO_CONCENTRATOR_IND:
        case zstackmsg_CmdIDs_ZDO_LEAVE_CNF:
        case zstackmsg_CmdIDs_ZDO_LEAVE_IND:
        case zstackmsg_CmdIDs_SYS_RESET_IND:
        case zstackmsg_CmdIDs_AF_REFLECT_ERROR_IND:
        case zstackmsg_CmdIDs_ZDO_TC_DEVICE_IND:
            break;

        default:
            break;
    }
}



/*******************************************************************************
 *
 * @fn          zclSampleThermostat_processAfIncomingMsgInd
 *
 * @brief       Process AF Incoming Message Indication message
 *
 * @param       pInMsg - pointer to incoming message
 *
 * @return      none
 *
 */
static void zclSampleThermostat_processAfIncomingMsgInd(zstack_afIncomingMsgInd_t *pInMsg)
{
    afIncomingMSGPacket_t afMsg;

    /*
     * All incoming messages are passed to the ZCL message processor,
     * first convert to a structure that ZCL can process.
     */
    afMsg.groupId = pInMsg->groupID;
    afMsg.clusterId = pInMsg->clusterId;
    afMsg.srcAddr.endPoint = pInMsg->srcAddr.endpoint;
    afMsg.srcAddr.panId = pInMsg->srcAddr.panID;
    afMsg.srcAddr.addrMode = (afAddrMode_t)pInMsg->srcAddr.addrMode;
    if( (afMsg.srcAddr.addrMode == afAddr16Bit)
        || (afMsg.srcAddr.addrMode == afAddrGroup)
        || (afMsg.srcAddr.addrMode == afAddrBroadcast) )
    {
        afMsg.srcAddr.addr.shortAddr = pInMsg->srcAddr.addr.shortAddr;
    }
    else if(afMsg.srcAddr.addrMode == afAddr64Bit)
    {
        OsalPort_memcpy(afMsg.srcAddr.addr.extAddr, &(pInMsg->srcAddr.addr.extAddr), 8);
    }
    afMsg.macDestAddr = pInMsg->macDestAddr;
    afMsg.endPoint = pInMsg->endpoint;
    afMsg.wasBroadcast = pInMsg->wasBroadcast;
    afMsg.LinkQuality = pInMsg->linkQuality;
    afMsg.correlation = pInMsg->correlation;
    afMsg.rssi = pInMsg->rssi;
    afMsg.SecurityUse = pInMsg->securityUse;
    afMsg.timestamp = pInMsg->timestamp;
    afMsg.nwkSeqNum = pInMsg->nwkSeqNum;
    afMsg.macSrcAddr = pInMsg->macSrcAddr;
    afMsg.radius = pInMsg->radius;
    afMsg.cmd.DataLength = pInMsg->n_payload;
    afMsg.cmd.Data = pInMsg->pPayload;

    zcl_ProcessMessageMSG(&afMsg);
}




/*********************************************************************
 * @fn      zclSampleThermostat_BasicResetCB
 *
 * @brief   Callback from the ZCL General Cluster Library
 *          to set all the Basic Cluster attributes to default values.
 *
 * @param   none
 *
 * @return  none
 */
static void zclSampleThermostat_BasicResetCB( void )
{
  zclSampleThermostat_ResetAttributesToDefaultValues();

#ifndef CUI_DISABLE
  UI_UpdateBdbStatusLine(NULL);
#endif
  zclSampleThermostat_UpdateLedState();
}




/*********************************************************************
 * @fn      zclSampleThermostat_SetpointRaiseLowerCB
 *
 * @brief   Callback from the ZCL HVAC Cluster Library
 *          to increase/decrease the Cooling/heating setpoint.
 *
 * @param   none
 *
 * @return  none
 */
static ZStatus_t zclSampleThermostat_SetpointRaiseLowerCB(zclCmdThermostatSetpointRaiseLowerPayload_t *pCmd)
{
  int16_t temp = pCmd->amount * 10;

  if((pCmd->mode == HVAC_THERMOSTAT_MODE_HEAT) || (pCmd->mode == HVAC_THERMOSTAT_MODE_BOTH))
  {
    if(zclSampleThermostat_OccupiedHeatingSetpoint + temp < zclSampleThermostat_AbsMinHeatSetpointLimit)
    {
      zclSampleThermostat_OccupiedHeatingSetpoint = zclSampleThermostat_AbsMinHeatSetpointLimit;
    }
    else if (zclSampleThermostat_OccupiedHeatingSetpoint + temp > zclSampleThermostat_AbsMaxHeatSetpointLimit)
    {
      zclSampleThermostat_OccupiedHeatingSetpoint = zclSampleThermostat_AbsMaxHeatSetpointLimit;
    }
    else
    {
      zclSampleThermostat_OccupiedHeatingSetpoint += temp;
    }
  }
  if((pCmd->mode == HVAC_THERMOSTAT_MODE_COOL) || (pCmd->mode == HVAC_THERMOSTAT_MODE_BOTH))
  {
    if(zclSampleThermostat_OccupiedCoolingSetpoint + temp < zclSampleThermostat_AbsMinCoolSetpointLimit)
    {
      zclSampleThermostat_OccupiedCoolingSetpoint = zclSampleThermostat_AbsMinCoolSetpointLimit;
    }
    else if (zclSampleThermostat_OccupiedCoolingSetpoint + temp > zclSampleThermostat_AbsMaxCoolSetpointLimit)
    {
      zclSampleThermostat_OccupiedCoolingSetpoint = zclSampleThermostat_AbsMaxCoolSetpointLimit;
    }
    else
    {
      zclSampleThermostat_OccupiedCoolingSetpoint += temp;
    }
  }

  return ZSuccess;
}

/******************************************************************************
 *
 *  Functions for processing ZCL Foundation incoming Command/Response messages
 *
 *****************************************************************************/

/*********************************************************************
 * @fn      zclSampleThermostat_ProcessIncomingMsg
 *
 * @brief   Process ZCL Foundation incoming message
 *
 * @param   pInMsg - pointer to the received message
 *
 * @return  uint8_t - TRUE if got handled
 */
static uint8_t zclSampleThermostat_ProcessIncomingMsg( zclIncoming_t *pInMsg)
{
  uint8_t handled = FALSE;
  switch ( pInMsg->hdr.commandID )
  {
#ifdef ZCL_READ
    case ZCL_CMD_READ_RSP:
      zclSampleThermostat_ProcessInReadRspCmd( pInMsg );
      handled = TRUE;
      break;
#endif
#ifdef ZCL_WRITE
    case ZCL_CMD_WRITE_RSP:
      zclSampleThermostat_ProcessInWriteRspCmd( pInMsg );
      handled = TRUE;
      break;
#endif
#ifdef ZCL_REPORT
    case ZCL_CMD_CONFIG_REPORT:
      //zclSampleThermostat_ProcessInConfigReportCmd( pInMsg );
      break;

    case ZCL_CMD_CONFIG_REPORT_RSP:
      //zclSampleThermostat_ProcessInConfigReportRspCmd( pInMsg );
      break;

    case ZCL_CMD_READ_REPORT_CFG:
      //zclSampleThermostat_ProcessInReadReportCfgCmd( pInMsg );
      break;

    case ZCL_CMD_READ_REPORT_CFG_RSP:
      //zclSampleThermostat_ProcessInReadReportCfgRspCmd( pInMsg );
      break;
#endif
#ifdef ZCL_REPORT_DESTINATION_DEVICE
    case ZCL_CMD_REPORT:
      zclSampleThermostat_ProcessInReportCmd( pInMsg );
      handled = TRUE;
      break;
#endif
    case ZCL_CMD_DEFAULT_RSP:
      zclSampleThermostat_ProcessInDefaultRspCmd( pInMsg );
      handled = TRUE;
      break;

    default:
      break;
  }

  return handled;
}


#ifdef ZCL_READ
/*********************************************************************
 * @fn      zclSampleThermostat_ProcessInReadRspCmd
 *
 * @brief   Process the "Profile" Read Response Command
 *
 * @param   pInMsg - incoming message to process
 *
 * @return  none
 */
static uint8_t zclSampleThermostat_ProcessInReadRspCmd( zclIncoming_t *pInMsg )
{
  zclReadRspCmd_t *readRspCmd;
  uint8_t i;

  readRspCmd = (zclReadRspCmd_t *)pInMsg->attrCmd;
  for (i = 0; i < readRspCmd->numAttr; i++)
  {
    // Notify the originator of the results of the original read attributes
    // attempt and, for each successfull request, the value of the requested
    // attribute
  }

  return ( TRUE );
}
#endif // ZCL_READ

#ifdef ZCL_WRITE
/*********************************************************************
 * @fn      zclSampleThermostat_ProcessInWriteRspCmd
 *
 * @brief   Process the "Profile" Write Response Command
 *
 * @param   pInMsg - incoming message to process
 *
 * @return  none
 */
static uint8_t zclSampleThermostat_ProcessInWriteRspCmd( zclIncoming_t *pInMsg )
{
  zclWriteRspCmd_t *writeRspCmd;
  uint8_t i;

  writeRspCmd = (zclWriteRspCmd_t *)pInMsg->attrCmd;
  for (i = 0; i < writeRspCmd->numAttr; i++)
  {
    // Notify the device of the results of the its original write attributes
    // command.
  }

  return ( TRUE );
}
#endif // ZCL_WRITE

#ifdef ZCL_REPORT_DESTINATION_DEVICE
/*********************************************************************
 * @fn      zclSampleThermostat_ProcessInReportCmd
 *
 * @brief   Process the "Profile" Report Command
 *
 * @param   pInMsg - incoming message to process
 *
 * @return  none
 */
static void zclSampleThermostat_ProcessInReportCmd( zclIncoming_t *pInMsg )
{
  zclReportCmd_t *pInTempSensorReport;

  pInTempSensorReport = (zclReportCmd_t *)pInMsg->attrCmd;
  char uartOut[128];
  int uartWrite = 0;

  char *json_deviceId = "\"device_id\"";
  char *json_deviceType = "\"device_type\"";
  char *json_datatype = "\"type\"";
  char *json_value = "\"value\"";

  switch (pInTempSensorReport->attrList[0].attrID) {
  case ATTRID_TEMPERATURE_MEASUREMENT_MEASURED_VALUE:
      // store the current temperature value sent over the air from temperature sensor
      zclSampleThermostat_LocalTemperature = BUILD_UINT16(pInTempSensorReport->attrList[0].attrData[0], pInTempSensorReport->attrList[0].attrData[1]);
      break;
  case CUSTOM_LIGHT:
      data_light = BUILD_UINT16(pInTempSensorReport->attrList[0].attrData[0], pInTempSensorReport->attrList[0].attrData[1]);
      sprintf(uartOut, "{%s:\"%X\", %s:\"%s\", %s:\"%s\", %s:%d}", json_deviceId, pInMsg->msg->srcAddr.addr.shortAddr, json_deviceType, "SENSOR", json_datatype, "LIGHT", json_value, data_light);
      uartWrite = 1;
      if (pInMsg->msg->srcAddr.addr.shortAddr != 0x4256) {
          id_light_disp0 = pInMsg->msg->srcAddr.addr.shortAddr;
          data_light_disp0 = data_light;
      } else {
          id_light_disp1 = 0x4256;
          data_light_disp1 = data_light;
      }
      break;
  case CUSTOM_TEMP_C:
      data_temp_c = BUILD_UINT16(pInTempSensorReport->attrList[0].attrData[0], pInTempSensorReport->attrList[0].attrData[1]);
      sprintf(uartOut, "{%s:\"%X\", %s:\"%s\", %s:\"%s\", %s:%f}", json_deviceId, pInMsg->msg->srcAddr.addr.shortAddr, json_deviceType, "SENSOR", json_datatype, "TEMP_C", json_value, data_temp_c / 100.0);
      uartWrite = 1;
      break;
  case CUSTOM_HUMID:
      data_humid = BUILD_UINT16(pInTempSensorReport->attrList[0].attrData[0], pInTempSensorReport->attrList[0].attrData[1]);
      sprintf(uartOut, "{%s:\"%X\", %s:\"%s\", %s:\"%s\", %s:%f}", json_deviceId, pInMsg->msg->srcAddr.addr.shortAddr, json_deviceType, "SENSOR", json_datatype, "HUMID", json_value, data_humid / 100.0);
      uartWrite = 1;
      break;
  }
  strcat(uartOut, "\r\n");
  if (uartWrite) { bb_uartWrite(uartOut, strlen(uartOut)); }

#ifndef CUI_DISABLE
  zclSampleThermostat_UpdateStatusLine();
#endif
  zclSampleThermostat_UpdateLedState();
}
#endif  // ZCL_REPORT_DESTINATION_DEVICE

/*********************************************************************
 * @fn      zclSampleThermostat_ProcessInDefaultRspCmd
 *
 * @brief   Process the "Profile" Default Response Command
 *
 * @param   pInMsg - incoming message to process
 *
 * @return  none
 */
static uint8_t zclSampleThermostat_ProcessInDefaultRspCmd( zclIncoming_t *pInMsg )
{
  // zclDefaultRspCmd_t *defaultRspCmd = (zclDefaultRspCmd_t *)pInMsg->attrCmd;

  // Device is notified of the Default Response command.
  (void)pInMsg;

  return ( TRUE );
}




/*********************************************************************
 * @fn      zclSampleThermostat_ProcessCommissioningStatus
 *
 * @brief   Callback in which the status of the commissioning process are reported
 *
 * @param   bdbCommissioningModeMsg - Context message of the status of a commissioning process
 *
 * @return  none
 */
static void zclSampleThermostat_ProcessCommissioningStatus(bdbCommissioningModeMsg_t *bdbCommissioningModeMsg)
{
  switch(bdbCommissioningModeMsg->bdbCommissioningMode)
  {
    case BDB_COMMISSIONING_FORMATION:
      if(bdbCommissioningModeMsg->bdbCommissioningStatus == BDB_COMMISSIONING_SUCCESS)
      {
        //YOUR JOB:
      }
      else
      {
        //Want to try other channels?
        //try with bdb_setChannelAttribute
      }
    break;
    case BDB_COMMISSIONING_NWK_STEERING:
      if(bdbCommissioningModeMsg->bdbCommissioningStatus == BDB_COMMISSIONING_SUCCESS)
      {
        //YOUR JOB:
        //We are on the nwk, what now?
      }
      else
      {
        //See the possible errors for nwk steering procedure
        //No suitable networks found
        //Want to try other channels?
        //try with bdb_setChannelAttribute
      }
    break;
    case BDB_COMMISSIONING_FINDING_BINDING:
      if(bdbCommissioningModeMsg->bdbCommissioningStatus == BDB_COMMISSIONING_SUCCESS)
      {
        //YOUR JOB:
      }
      else
      {
        //YOUR JOB:
        //retry?, wait for user interaction?
      }
    break;
    case BDB_COMMISSIONING_INITIALIZATION:
      //Initialization notification can only be successful. Failure on initialization
      //only happens for ZED and is notified as BDB_COMMISSIONING_PARENT_LOST notification

      //YOUR JOB:
      //We are on a network, what now?

    break;
#if ZG_BUILD_ENDDEVICE_TYPE
    case BDB_COMMISSIONING_PARENT_LOST:
      if(bdbCommissioningModeMsg->bdbCommissioningStatus == BDB_COMMISSIONING_NETWORK_RESTORED)
      {
        //We did recover from losing parent
      }
      else
      {
        //Parent not found, attempt to rejoin again after a fixed delay
        UtilTimer_setTimeout( EndDeviceRejoinClkHandle, SAMPLEAPP_END_DEVICE_REJOIN_DELAY );
        UtilTimer_start(&EndDeviceRejoinClkStruct);
      }
    break;
#endif
  }

#ifndef CUI_DISABLE
  UI_UpdateBdbStatusLine(bdbCommissioningModeMsg);
#endif
}

void zclSampleThermostat_UpdateLedState(void)
{
  // use LEDs to show heating or cooling cycles based off local temperature
  if ( zclSampleThermostat_LocalTemperature != ATTR_INVALID_MEASUREMENT_HVAC_THERMOSTAT_LOCAL_TEMPERATURE )
  {
    if ( zclSampleThermostat_LocalTemperature <= zclSampleThermostat_OccupiedHeatingSetpoint )
    {
      // turn on heating
      zclSampleThermostat_SystemMode = HVAC_THERMOSTAT_SYSTEM_MODE_HEAT;
      //LED_stopBlinking(gRedLedHandle);
      //LED_setOn(gRedLedHandle, LED_BRIGHTNESS_MAX);
    }
    else if ( zclSampleThermostat_LocalTemperature >= zclSampleThermostat_OccupiedCoolingSetpoint )
    {
      // turn on cooling
      zclSampleThermostat_SystemMode = HVAC_THERMOSTAT_SYSTEM_MODE_COOL;
      //LED_startBlinking(gRedLedHandle, 500, LED_BLINK_FOREVER);
    }
    else
    {
      // turn off heating/cooling
      zclSampleThermostat_SystemMode = HVAC_THERMOSTAT_SYSTEM_MODE_OFF;
      //LED_stopBlinking(gRedLedHandle);
      //LED_setOff(gRedLedHandle);
    }
  }
}

#ifndef CUI_DISABLE
void zclSampleThermostat_UiActionSetHeatPoint(const char _input, char* _lines[3], CUI_cursorInfo_t * _curInfos)
{
    if(_input == CUI_INPUT_UP)
    {
        // increase heating setpoint, considering whole numbers where necessary
        if ( zclSampleThermostat_OccupiedHeatingSetpoint < zclSampleThermostat_AbsMaxHeatSetpointLimit )
        {
          zclSampleThermostat_OccupiedHeatingSetpoint = zclSampleThermostat_OccupiedHeatingSetpoint + 100;
        }
        else if ( zclSampleThermostat_OccupiedHeatingSetpoint >= zclSampleThermostat_AbsMaxHeatSetpointLimit )
        {
          zclSampleThermostat_OccupiedHeatingSetpoint = zclSampleThermostat_AbsMaxHeatSetpointLimit;
        }
    }
    else if (_input == CUI_INPUT_DOWN)
    {
        // decrease heating setpoint, considering whole numbers where necessary
        if ( zclSampleThermostat_OccupiedHeatingSetpoint > zclSampleThermostat_AbsMinHeatSetpointLimit )
        {
          zclSampleThermostat_OccupiedHeatingSetpoint = zclSampleThermostat_OccupiedHeatingSetpoint - 100;
        }
        else if ( zclSampleThermostat_OccupiedHeatingSetpoint <= zclSampleThermostat_AbsMinHeatSetpointLimit )
        {
          zclSampleThermostat_OccupiedHeatingSetpoint = zclSampleThermostat_AbsMinHeatSetpointLimit;
        }
    }

    Util_ltoa( ( zclSampleThermostat_OccupiedHeatingSetpoint / 100 ),(uint8_t*) _lines[1], 10 ); // only use whole number
    strcat(_lines[1], " C");
    strcpy(_lines[2], " SET HEAT TEMP ");
}

void zclSampleThermostat_UiActionSetCoolPoint(const char _input, char* _lines[3], CUI_cursorInfo_t * _curInfo)
{
    if(_input == CUI_INPUT_UP)
    {
        // increase cooling setpoint, considering whole numbers where necessary
        if ( zclSampleThermostat_OccupiedCoolingSetpoint < zclSampleThermostat_AbsMaxCoolSetpointLimit )
        {
            zclSampleThermostat_OccupiedCoolingSetpoint = zclSampleThermostat_OccupiedCoolingSetpoint + 100;
        }
        else if ( zclSampleThermostat_OccupiedCoolingSetpoint >= zclSampleThermostat_AbsMaxCoolSetpointLimit )
        {
            zclSampleThermostat_OccupiedCoolingSetpoint = zclSampleThermostat_AbsMaxCoolSetpointLimit;
        }
    }
    else if (_input == CUI_INPUT_DOWN)
    {
        // decrease cooling setpoint, considering whole numbers where necessary
        if ( zclSampleThermostat_OccupiedCoolingSetpoint > zclSampleThermostat_AbsMinCoolSetpointLimit )
        {
            zclSampleThermostat_OccupiedCoolingSetpoint = zclSampleThermostat_OccupiedCoolingSetpoint - 100;
        }
        else if ( zclSampleThermostat_OccupiedCoolingSetpoint <= zclSampleThermostat_AbsMinCoolSetpointLimit )
        {
            zclSampleThermostat_OccupiedCoolingSetpoint = zclSampleThermostat_AbsMinCoolSetpointLimit;
        }
    }

    Util_ltoa( ( zclSampleThermostat_OccupiedCoolingSetpoint / 100 ),(uint8_t*) _lines[1], 10 ); // only use whole number
    strcat(_lines[1], " C");
    strcpy(_lines[2], " SET COOL TEMP ");
}

/*********************************************************************
 * @fn      zclSampleThermostat_processKey
 *
 * @brief   Key event handler function
 *
 * @param   key - key to handle action for
 *          buttonEvents - event to handle action for
 *
 * @return  none
 */
static void zclSampleThermostat_processKey(uint8_t key, Button_EventMask buttonEvents)
{
    if (buttonEvents & Button_EV_CLICKED)
    {
        if(key == CONFIG_BTN_LEFT)
        {
//            zstack_bdbStartCommissioningReq_t zstack_bdbStartCommissioningReq;

//            zstack_bdbStartCommissioningReq.commissioning_mode = zclSampleThermostat_BdbCommissioningModes;
//            Zstackapi_bdbStartCommissioningReq(appServiceTaskId,&zstack_bdbStartCommissioningReq);
        }
    }
}

static void zclSampleThermostat_InitializeStatusLine(CUI_clientHandle_t gCuiHandle)
{
    /* Request Async Line for Light application Info */
    CUI_statusLineResourceRequest(gCuiHandle, "   APP Info"CUI_DEBUG_MSG_START"1"CUI_DEBUG_MSG_END, false, &gSampleThermostatInfoLine1);
    CUI_statusLineResourceRequest(gCuiHandle, "   APP Info"CUI_DEBUG_MSG_START"2"CUI_DEBUG_MSG_END, false, &gSampleThermostatInfoLine2);

    zclSampleThermostat_UpdateStatusLine();
}

static void zclSampleThermostat_UpdateStatusLine(void)
{
    char lineFormat1[MAX_STATUS_LINE_VALUE_LEN] = {'\0'};
    char lineFormat2[MAX_STATUS_LINE_VALUE_LEN] = {'\0'};

    strcat(lineFormat1, "["CUI_COLOR_CYAN"Light Value Device 0x%04x"CUI_COLOR_RESET"] %d lm");
    strcat(lineFormat2, "["CUI_COLOR_CYAN"Light Value Device 0x%04x"CUI_COLOR_RESET"] %d lm");

    if (id_light_disp0) { CUI_statusLinePrintf(gCuiHandle, gSampleThermostatInfoLine1, lineFormat1, id_light_disp0, data_light_disp0); }
    if (id_light_disp1) { CUI_statusLinePrintf(gCuiHandle, gSampleThermostatInfoLine2, lineFormat2, id_light_disp1, data_light_disp1); }
}

#endif

#if defined (ENABLE_GREENPOWER_COMBO_BASIC)
#ifndef CUI_DISABLE
void zclSampleThermostat_setGPSinkCommissioningMode(const int32_t _itemEntry)
{
  bool zclSampleThermostat_SetSinkCommissioningMode = 0;

  //Toggle current commissioning flag value and set that value again
  zclSampleThermostat_SetSinkCommissioningMode = !gp_GetSinkCommissioningMode();
  gp_SetSinkCommissioningMode(zclSampleThermostat_SetSinkCommissioningMode);

  UI_UpdateGpStatusLine();

}
#endif
/*********************************************************************
 * @fn      zclSampleThermostat_GPSink_Identify
 *
 * @brief   Callback to process Identify command from a GPD
 *
 * @param   zclGpNotification
 *
 * @return  none
 */
static void zclSampleThermostat_GPSink_Identify(zclGpNotification_t *zclGpNotification)
{
  afAddrType_t  dstAddr;

  dstAddr.endPoint = SAMPLETHERMOSTAT_ENDPOINT;
  dstAddr.panId = 0;
  dstAddr.addrMode = afAddr16Bit;
  dstAddr.addr.shortAddr = _NIB.nwkDevAddress;

  //Identify is a payloadless command which triggers a 60 seconds identify in the device (doc 14-0563-16 GP spec Table 49)
  zclGeneral_SendIdentify(SAMPLETHERMOSTAT_ENDPOINT,&dstAddr,60,TRUE, 1);
}


/*********************************************************************
 * @fn      zclSampleThermostat_GPSink_ProcessReport
 *
 * @brief   Callback to process Report Attributes command from a GPD
 *
 * @param   zclGpNotification
 *
 * @return  none
 */
static void zclSampleThermostat_GPSink_ProcessReport(zclGpNotification_t *zclGpNotification)
{
  uint16_t        clusterId;
  uint16_t        attrId;
  uint8_t         *pData;

  pData = zclGpNotification->pData;
  //Get the cluster ID
  clusterId = BUILD_UINT16(pData[0], pData[1]);
  pData += sizeof(uint16_t);

  //Point to the attribute report list
  attrId = BUILD_UINT16(pData[0], pData[1]);
  pData += 3;  // attrId + dataType


  if ( (attrId != ATTRID_TEMPERATURE_MEASUREMENT_MEASURED_VALUE) && (clusterId == ZCL_CLUSTER_ID_MS_TEMPERATURE_MEASUREMENT) )
  {
    return;
  }

  // store the current temperature value sent over the air from GPD temperature sensor
  zclSampleThermostat_LocalTemperature = BUILD_UINT16(pData[0], pData[1]);
  zclSampleThermostat_LocalTemperature *= 100;  // to format the temperature correctly

#ifndef CUI_DISABLE
  zclSampleThermostat_UpdateStatusLine();
#endif
  zclSampleThermostat_UpdateLedState();

}


#endif
