Iowa-Sate-Senior-Design-Dec-2021-Team-7/BBGreenZigbeeCape/firmware/daughterboard/tests/zed_temperaturesensor_CC1352R1_LAUNCHXL_tirtos_ccs/default/configPkg/package/cfg/app_pem4f.c

/*
 *  Do not modify this file; it is automatically 
 *  generated and any modifications will be overwritten.
 *
 * @(#) xdc-K04
 */

#define __nested__
#define __config__

#include <xdc/std.h>

/*
 * ======== GENERATED SECTIONS ========
 *
 *     MODULE INCLUDES
 *
 *     <module-name> INTERNALS
 *     <module-name> INHERITS
 *     <module-name> VTABLE
 *     <module-name> PATCH TABLE
 *     <module-name> DECLARATIONS
 *     <module-name> OBJECT OFFSETS
 *     <module-name> TEMPLATES
 *     <module-name> INITIALIZERS
 *     <module-name> FUNCTION STUBS
 *     <module-name> PROXY BODY
 *     <module-name> OBJECT DESCRIPTOR
 *     <module-name> VIRTUAL FUNCTIONS
 *     <module-name> SYSTEM FUNCTIONS
 *     <module-name> PRAGMAS
 *
 *     INITIALIZATION ENTRY POINT
 *     PROGRAM GLOBALS
 *     CLINK DIRECTIVES
 */


/*
 * ======== MODULE INCLUDES ========
 */

#include <ti/sysbios/BIOS.h>
#include <ti/sysbios/family/arm/cc26xx/Boot.h>
#include <ti/sysbios/family/arm/cc26xx/Timer.h>
#include <ti/sysbios/family/arm/cc26xx/TimestampProvider.h>
#include <ti/sysbios/family/arm/m3/Hwi.h>
#include <ti/sysbios/family/arm/m3/IntrinsicsSupport.h>
#include <ti/sysbios/family/arm/m3/TaskSupport.h>
#include <ti/sysbios/gates/GateHwi.h>
#include <ti/sysbios/gates/GateMutex.h>
#include <ti/sysbios/gates/GateMutexPri.h>
#include <ti/sysbios/hal/Hwi.h>
#include <ti/sysbios/heaps/HeapCallback.h>
#include <ti/sysbios/heaps/HeapMem.h>
#include <ti/sysbios/heaps/HeapTrack.h>
#include <ti/sysbios/knl/Clock.h>
#include <ti/sysbios/knl/Event.h>
#include <ti/sysbios/knl/Idle.h>
#include <ti/sysbios/knl/Intrinsics.h>
#include <ti/sysbios/knl/Mailbox.h>
#include <ti/sysbios/knl/Queue.h>
#include <ti/sysbios/knl/Semaphore.h>
#include <ti/sysbios/knl/Swi.h>
#include <ti/sysbios/knl/Task.h>
#include <ti/sysbios/rom/cortexm/cc26xx/cc26x2v2/CC26xx.h>
#include <xdc/runtime/Assert.h>
#include <xdc/runtime/Core.h>
#include <xdc/runtime/Defaults.h>
#include <xdc/runtime/Diags.h>
#include <xdc/runtime/Error.h>
#include <xdc/runtime/Gate.h>
#include <xdc/runtime/Log.h>
#include <xdc/runtime/Main.h>
#include <xdc/runtime/Memory.h>
#include <xdc/runtime/Registry.h>
#include <xdc/runtime/Startup.h>
#include <xdc/runtime/SysCallback.h>
#include <xdc/runtime/System.h>
#include <xdc/runtime/Text.h>
#include <xdc/runtime/Timestamp.h>
#include <xdc/runtime/Types.h>

/* suppress 'type qualifier is meaningless on cast type' warning */
#if defined(__ti__) && !defined(__clang__)
#pragma diag_suppress 193
#endif
#ifdef __IAR_SYSTEMS_ICC__
#pragma diag_suppress=Pe191
#endif

#if !(defined(__GNUC__))
#if !(defined(__TI_GNU_ATTRIBUTE_SUPPORT__) || defined(__IAR_SYSTEMS_ICC__)) || defined(__ARP32__)
#define __attribute__(x)
#endif
#endif

/*
 * ======== ti.sysbios.BIOS INTERNALS ========
 */


/*
 * ======== ti.sysbios.BIOS_RtsGateProxy INTERNALS ========
 */

/* Module__ */
typedef struct ti_sysbios_BIOS_RtsGateProxy_Module__ {
    xdc_runtime_Types_Link link;
} ti_sysbios_BIOS_RtsGateProxy_Module__;

/* Module__root__V */
extern ti_sysbios_BIOS_RtsGateProxy_Module__ ti_sysbios_BIOS_RtsGateProxy_Module__root__V;

/* @@@ ti_sysbios_knl_Queue_Object__ */
typedef struct ti_sysbios_knl_Queue_Object__ {
    ti_sysbios_knl_Queue_Elem elem;
} ti_sysbios_knl_Queue_Object__;

/* @@@ ti_sysbios_knl_Queue_Object2__ */
typedef struct {
    xdc_runtime_Types_InstHdr hdr;
    ti_sysbios_knl_Queue_Object__ obj;
} ti_sysbios_knl_Queue_Object2__;

/* @@@ ti_sysbios_knl_Semaphore_Object__ */
typedef struct ti_sysbios_knl_Semaphore_Object__ {
    ti_sysbios_knl_Event_Handle event;
    xdc_UInt eventId;
    ti_sysbios_knl_Semaphore_Mode mode;
    volatile xdc_UInt16 count;
    ti_sysbios_knl_Queue_Object__ Object_field_pendQ;
} ti_sysbios_knl_Semaphore_Object__;

/* @@@ ti_sysbios_knl_Semaphore_Object2__ */
typedef struct {
    xdc_runtime_Types_InstHdr hdr;
    ti_sysbios_knl_Semaphore_Object__ obj;
} ti_sysbios_knl_Semaphore_Object2__;

/* Object__ */
typedef struct ti_sysbios_gates_GateMutex_Object__ {
    const ti_sysbios_gates_GateMutex_Fxns__ *__fxns;
    ti_sysbios_knl_Task_Handle owner;
    ti_sysbios_knl_Semaphore_Object__ Object_field_sem;
} ti_sysbios_gates_GateMutex_Object__;

/* Object2__ */
typedef struct {
    xdc_runtime_Types_InstHdr hdr;
    ti_sysbios_gates_GateMutex_Object__ obj;
} ti_sysbios_gates_GateMutex_Object2__;

/* Object */
typedef ti_sysbios_gates_GateMutex_Object__ ti_sysbios_BIOS_RtsGateProxy_Object__;

/* Object2__ */
typedef struct {
    xdc_runtime_Types_InstHdr hdr;
    ti_sysbios_BIOS_RtsGateProxy_Object__ obj;
} ti_sysbios_BIOS_RtsGateProxy_Object2__;


/*
 * ======== ti.sysbios.family.arm.cc26xx.Boot INTERNALS ========
 */


/*
 * ======== ti.sysbios.family.arm.cc26xx.Timer INTERNALS ========
 */

/* Module__ */
typedef struct ti_sysbios_family_arm_cc26xx_Timer_Module__ {
    xdc_runtime_Types_Link link;
} ti_sysbios_family_arm_cc26xx_Timer_Module__;

/* Module__root__V */
extern ti_sysbios_family_arm_cc26xx_Timer_Module__ ti_sysbios_family_arm_cc26xx_Timer_Module__root__V;

/* Object__ */
typedef struct ti_sysbios_family_arm_cc26xx_Timer_Object__ {
    const ti_sysbios_family_arm_cc26xx_Timer_Fxns__ *__fxns;
    xdc_Bool staticInst;
    xdc_Int id;
    ti_sysbios_interfaces_ITimer_StartMode startMode;
    xdc_UInt32 period;
    xdc_UArg arg;
    ti_sysbios_family_arm_m3_Hwi_FuncPtr tickFxn;
    xdc_runtime_Types_FreqHz frequency;
    ti_sysbios_family_arm_m3_Hwi_Handle hwi;
    xdc_UInt64 period64;
    xdc_UInt64 savedCurrCount;
    xdc_UInt64 prevThreshold;
    xdc_UInt64 nextThreshold;
} ti_sysbios_family_arm_cc26xx_Timer_Object__;

/* Object2__ */
typedef struct {
    xdc_runtime_Types_InstHdr hdr;
    ti_sysbios_family_arm_cc26xx_Timer_Object__ obj;
} ti_sysbios_family_arm_cc26xx_Timer_Object2__;


/*
 * ======== ti.sysbios.family.arm.cc26xx.TimestampProvider INTERNALS ========
 */


/*
 * ======== ti.sysbios.family.arm.m3.Hwi INTERNALS ========
 */

/* Module__ */
typedef struct ti_sysbios_family_arm_m3_Hwi_Module__ {
    xdc_runtime_Types_Link link;
} ti_sysbios_family_arm_m3_Hwi_Module__;

/* Module__root__V */
extern ti_sysbios_family_arm_m3_Hwi_Module__ ti_sysbios_family_arm_m3_Hwi_Module__root__V;

/* Object__ */
typedef struct ti_sysbios_family_arm_m3_Hwi_Object__ {
    const ti_sysbios_family_arm_m3_Hwi_Fxns__ *__fxns;
    xdc_UArg arg;
    ti_sysbios_family_arm_m3_Hwi_FuncPtr fxn;
    ti_sysbios_family_arm_m3_Hwi_Irp irp;
    xdc_UInt8 priority;
    xdc_Int16 intNum;
    __TA_ti_sysbios_family_arm_m3_Hwi_Instance_State__hookEnv hookEnv;
} ti_sysbios_family_arm_m3_Hwi_Object__;

/* Object2__ */
typedef struct {
    xdc_runtime_Types_InstHdr hdr;
    ti_sysbios_family_arm_m3_Hwi_Object__ obj;
} ti_sysbios_family_arm_m3_Hwi_Object2__;


/*
 * ======== ti.sysbios.family.arm.m3.IntrinsicsSupport INTERNALS ========
 */


/*
 * ======== ti.sysbios.family.arm.m3.TaskSupport INTERNALS ========
 */


/*
 * ======== ti.sysbios.gates.GateHwi INTERNALS ========
 */

/* Module__ */
typedef struct ti_sysbios_gates_GateHwi_Module__ {
    xdc_runtime_Types_Link link;
} ti_sysbios_gates_GateHwi_Module__;

/* Module__root__V */
extern ti_sysbios_gates_GateHwi_Module__ ti_sysbios_gates_GateHwi_Module__root__V;

/* Object__ */
typedef struct ti_sysbios_gates_GateHwi_Object__ {
    const ti_sysbios_gates_GateHwi_Fxns__ *__fxns;
} ti_sysbios_gates_GateHwi_Object__;

/* Object2__ */
typedef struct {
    xdc_runtime_Types_InstHdr hdr;
    ti_sysbios_gates_GateHwi_Object__ obj;
} ti_sysbios_gates_GateHwi_Object2__;


/*
 * ======== ti.sysbios.gates.GateMutex INTERNALS ========
 */

/* Module__ */
typedef struct ti_sysbios_gates_GateMutex_Module__ {
    xdc_runtime_Types_Link link;
} ti_sysbios_gates_GateMutex_Module__;

/* Module__root__V */
extern ti_sysbios_gates_GateMutex_Module__ ti_sysbios_gates_GateMutex_Module__root__V;

/* <-- ti_sysbios_gates_GateMutex_Object */


/*
 * ======== ti.sysbios.gates.GateMutexPri INTERNALS ========
 */

/* Module__ */
typedef struct ti_sysbios_gates_GateMutexPri_Module__ {
    xdc_runtime_Types_Link link;
} ti_sysbios_gates_GateMutexPri_Module__;

/* Module__root__V */
extern ti_sysbios_gates_GateMutexPri_Module__ ti_sysbios_gates_GateMutexPri_Module__root__V;

/* <-- ti_sysbios_knl_Queue_Object */

/* Object__ */
typedef struct ti_sysbios_gates_GateMutexPri_Object__ {
    const ti_sysbios_gates_GateMutexPri_Fxns__ *__fxns;
    volatile xdc_UInt mutexCnt;
    volatile xdc_Int ownerOrigPri;
    volatile ti_sysbios_knl_Task_Handle owner;
    ti_sysbios_knl_Queue_Object__ Object_field_pendQ;
} ti_sysbios_gates_GateMutexPri_Object__;

/* Object2__ */
typedef struct {
    xdc_runtime_Types_InstHdr hdr;
    ti_sysbios_gates_GateMutexPri_Object__ obj;
} ti_sysbios_gates_GateMutexPri_Object2__;


/*
 * ======== ti.sysbios.hal.Hwi INTERNALS ========
 */

/* Module__ */
typedef struct ti_sysbios_hal_Hwi_Module__ {
    xdc_runtime_Types_Link link;
} ti_sysbios_hal_Hwi_Module__;

/* Module__root__V */
extern ti_sysbios_hal_Hwi_Module__ ti_sysbios_hal_Hwi_Module__root__V;

/* Object__ */
typedef struct ti_sysbios_hal_Hwi_Object__ {
    const ti_sysbios_hal_Hwi_Fxns__ *__fxns;
    ti_sysbios_hal_Hwi_HwiProxy_Handle pi;
} ti_sysbios_hal_Hwi_Object__;

/* Object2__ */
typedef struct {
    xdc_runtime_Types_InstHdr hdr;
    ti_sysbios_hal_Hwi_Object__ obj;
} ti_sysbios_hal_Hwi_Object2__;


/*
 * ======== ti.sysbios.hal.Hwi_HwiProxy INTERNALS ========
 */

/* Module__ */
typedef struct ti_sysbios_hal_Hwi_HwiProxy_Module__ {
    xdc_runtime_Types_Link link;
} ti_sysbios_hal_Hwi_HwiProxy_Module__;

/* Module__root__V */
extern ti_sysbios_hal_Hwi_HwiProxy_Module__ ti_sysbios_hal_Hwi_HwiProxy_Module__root__V;

/* <-- ti_sysbios_family_arm_m3_Hwi_Object */

/* Object */
typedef ti_sysbios_family_arm_m3_Hwi_Object__ ti_sysbios_hal_Hwi_HwiProxy_Object__;

/* Object2__ */
typedef struct {
    xdc_runtime_Types_InstHdr hdr;
    ti_sysbios_hal_Hwi_HwiProxy_Object__ obj;
} ti_sysbios_hal_Hwi_HwiProxy_Object2__;


/*
 * ======== ti.sysbios.heaps.HeapCallback INTERNALS ========
 */

/* Module__ */
typedef struct ti_sysbios_heaps_HeapCallback_Module__ {
    xdc_runtime_Types_Link link;
} ti_sysbios_heaps_HeapCallback_Module__;

/* Module__root__V */
extern ti_sysbios_heaps_HeapCallback_Module__ ti_sysbios_heaps_HeapCallback_Module__root__V;

/* Object__ */
typedef struct ti_sysbios_heaps_HeapCallback_Object__ {
    const ti_sysbios_heaps_HeapCallback_Fxns__ *__fxns;
    xdc_UArg context;
    xdc_UArg arg;
} ti_sysbios_heaps_HeapCallback_Object__;

/* Object2__ */
typedef struct {
    xdc_runtime_Types_InstHdr hdr;
    ti_sysbios_heaps_HeapCallback_Object__ obj;
} ti_sysbios_heaps_HeapCallback_Object2__;


/*
 * ======== ti.sysbios.heaps.HeapMem INTERNALS ========
 */

/* Module__ */
typedef struct ti_sysbios_heaps_HeapMem_Module__ {
    xdc_runtime_Types_Link link;
} ti_sysbios_heaps_HeapMem_Module__;

/* Module__root__V */
extern ti_sysbios_heaps_HeapMem_Module__ ti_sysbios_heaps_HeapMem_Module__root__V;

/* Object__ */
typedef struct ti_sysbios_heaps_HeapMem_Object__ {
    const ti_sysbios_heaps_HeapMem_Fxns__ *__fxns;
    xdc_runtime_Memory_Size align;
    __TA_ti_sysbios_heaps_HeapMem_Instance_State__buf buf;
    ti_sysbios_heaps_HeapMem_Header head;
    xdc_SizeT minBlockAlign;
} ti_sysbios_heaps_HeapMem_Object__;

/* Object2__ */
typedef struct {
    xdc_runtime_Types_InstHdr hdr;
    ti_sysbios_heaps_HeapMem_Object__ obj;
} ti_sysbios_heaps_HeapMem_Object2__;


/*
 * ======== ti.sysbios.heaps.HeapMem_Module_GateProxy INTERNALS ========
 */

/* Module__ */
typedef struct ti_sysbios_heaps_HeapMem_Module_GateProxy_Module__ {
    xdc_runtime_Types_Link link;
} ti_sysbios_heaps_HeapMem_Module_GateProxy_Module__;

/* Module__root__V */
extern ti_sysbios_heaps_HeapMem_Module_GateProxy_Module__ ti_sysbios_heaps_HeapMem_Module_GateProxy_Module__root__V;

/* <-- ti_sysbios_gates_GateMutex_Object */

/* Object */
typedef ti_sysbios_gates_GateMutex_Object__ ti_sysbios_heaps_HeapMem_Module_GateProxy_Object__;

/* Object2__ */
typedef struct {
    xdc_runtime_Types_InstHdr hdr;
    ti_sysbios_heaps_HeapMem_Module_GateProxy_Object__ obj;
} ti_sysbios_heaps_HeapMem_Module_GateProxy_Object2__;


/*
 * ======== ti.sysbios.heaps.HeapTrack INTERNALS ========
 */

/* Module__ */
typedef struct ti_sysbios_heaps_HeapTrack_Module__ {
    xdc_runtime_Types_Link link;
} ti_sysbios_heaps_HeapTrack_Module__;

/* Module__root__V */
extern ti_sysbios_heaps_HeapTrack_Module__ ti_sysbios_heaps_HeapTrack_Module__root__V;

/* <-- ti_sysbios_knl_Queue_Object */

/* Object__ */
typedef struct ti_sysbios_heaps_HeapTrack_Object__ {
    const ti_sysbios_heaps_HeapTrack_Fxns__ *__fxns;
    xdc_runtime_IHeap_Handle internalHeap;
    xdc_SizeT size;
    xdc_SizeT peak;
    xdc_SizeT sizeWithoutTracker;
    xdc_SizeT peakWithoutTracker;
    ti_sysbios_knl_Queue_Object__ Object_field_trackQueue;
} ti_sysbios_heaps_HeapTrack_Object__;

/* Object2__ */
typedef struct {
    xdc_runtime_Types_InstHdr hdr;
    ti_sysbios_heaps_HeapTrack_Object__ obj;
} ti_sysbios_heaps_HeapTrack_Object2__;


/*
 * ======== ti.sysbios.knl.Clock INTERNALS ========
 */

/* Module__ */
typedef struct ti_sysbios_knl_Clock_Module__ {
    xdc_runtime_Types_Link link;
} ti_sysbios_knl_Clock_Module__;

/* Module__root__V */
extern ti_sysbios_knl_Clock_Module__ ti_sysbios_knl_Clock_Module__root__V;

/* <-- ti_sysbios_knl_Queue_Object */

/* Object__ */
typedef struct ti_sysbios_knl_Clock_Object__ {
    ti_sysbios_knl_Queue_Elem elem;
    xdc_UInt32 timeout;
    xdc_UInt32 currTimeout;
    xdc_UInt32 period;
    volatile xdc_Bool active;
    ti_sysbios_knl_Clock_FuncPtr fxn;
    xdc_UArg arg;
} ti_sysbios_knl_Clock_Object__;

/* Object2__ */
typedef struct {
    xdc_runtime_Types_InstHdr hdr;
    ti_sysbios_knl_Clock_Object__ obj;
} ti_sysbios_knl_Clock_Object2__;


/*
 * ======== ti.sysbios.knl.Clock_TimerProxy INTERNALS ========
 */

/* Module__ */
typedef struct ti_sysbios_knl_Clock_TimerProxy_Module__ {
    xdc_runtime_Types_Link link;
} ti_sysbios_knl_Clock_TimerProxy_Module__;

/* Module__root__V */
extern ti_sysbios_knl_Clock_TimerProxy_Module__ ti_sysbios_knl_Clock_TimerProxy_Module__root__V;

/* <-- ti_sysbios_family_arm_cc26xx_Timer_Object */

/* Object */
typedef ti_sysbios_family_arm_cc26xx_Timer_Object__ ti_sysbios_knl_Clock_TimerProxy_Object__;

/* Object2__ */
typedef struct {
    xdc_runtime_Types_InstHdr hdr;
    ti_sysbios_knl_Clock_TimerProxy_Object__ obj;
} ti_sysbios_knl_Clock_TimerProxy_Object2__;


/*
 * ======== ti.sysbios.knl.Event INTERNALS ========
 */

/* Module__ */
typedef struct ti_sysbios_knl_Event_Module__ {
    xdc_runtime_Types_Link link;
} ti_sysbios_knl_Event_Module__;

/* Module__root__V */
extern ti_sysbios_knl_Event_Module__ ti_sysbios_knl_Event_Module__root__V;

/* <-- ti_sysbios_knl_Queue_Object */

/* Object__ */
typedef struct ti_sysbios_knl_Event_Object__ {
    volatile xdc_UInt postedEvents;
    ti_sysbios_knl_Queue_Object__ Object_field_pendQ;
} ti_sysbios_knl_Event_Object__;

/* Object2__ */
typedef struct {
    xdc_runtime_Types_InstHdr hdr;
    ti_sysbios_knl_Event_Object__ obj;
} ti_sysbios_knl_Event_Object2__;


/*
 * ======== ti.sysbios.knl.Idle INTERNALS ========
 */


/*
 * ======== ti.sysbios.knl.Intrinsics INTERNALS ========
 */


/*
 * ======== ti.sysbios.knl.Intrinsics_SupportProxy INTERNALS ========
 */


/*
 * ======== ti.sysbios.knl.Mailbox INTERNALS ========
 */

/* Module__ */
typedef struct ti_sysbios_knl_Mailbox_Module__ {
    xdc_runtime_Types_Link link;
} ti_sysbios_knl_Mailbox_Module__;

/* Module__root__V */
extern ti_sysbios_knl_Mailbox_Module__ ti_sysbios_knl_Mailbox_Module__root__V;

/* <-- ti_sysbios_knl_Queue_Object */

/* <-- ti_sysbios_knl_Semaphore_Object */

/* Object__ */
typedef struct ti_sysbios_knl_Mailbox_Object__ {
    xdc_runtime_IHeap_Handle heap;
    xdc_SizeT msgSize;
    xdc_UInt numMsgs;
    xdc_Ptr buf;
    xdc_UInt numFreeMsgs;
    __TA_ti_sysbios_knl_Mailbox_Instance_State__allocBuf allocBuf;
    ti_sysbios_knl_Queue_Object__ Object_field_dataQue;
    ti_sysbios_knl_Queue_Object__ Object_field_freeQue;
    ti_sysbios_knl_Semaphore_Object__ Object_field_dataSem;
    ti_sysbios_knl_Semaphore_Object__ Object_field_freeSem;
} ti_sysbios_knl_Mailbox_Object__;

/* Object2__ */
typedef struct {
    xdc_runtime_Types_InstHdr hdr;
    ti_sysbios_knl_Mailbox_Object__ obj;
} ti_sysbios_knl_Mailbox_Object2__;


/*
 * ======== ti.sysbios.knl.Queue INTERNALS ========
 */

/* Module__ */
typedef struct ti_sysbios_knl_Queue_Module__ {
    xdc_runtime_Types_Link link;
} ti_sysbios_knl_Queue_Module__;

/* Module__root__V */
extern ti_sysbios_knl_Queue_Module__ ti_sysbios_knl_Queue_Module__root__V;

/* <-- ti_sysbios_knl_Queue_Object */


/*
 * ======== ti.sysbios.knl.Semaphore INTERNALS ========
 */

/* Module__ */
typedef struct ti_sysbios_knl_Semaphore_Module__ {
    xdc_runtime_Types_Link link;
} ti_sysbios_knl_Semaphore_Module__;

/* Module__root__V */
extern ti_sysbios_knl_Semaphore_Module__ ti_sysbios_knl_Semaphore_Module__root__V;

/* <-- ti_sysbios_knl_Semaphore_Object */


/*
 * ======== ti.sysbios.knl.Swi INTERNALS ========
 */

/* Module__ */
typedef struct ti_sysbios_knl_Swi_Module__ {
    xdc_runtime_Types_Link link;
} ti_sysbios_knl_Swi_Module__;

/* Module__root__V */
extern ti_sysbios_knl_Swi_Module__ ti_sysbios_knl_Swi_Module__root__V;

/* Object__ */
typedef struct ti_sysbios_knl_Swi_Object__ {
    ti_sysbios_knl_Queue_Elem qElem;
    ti_sysbios_knl_Swi_FuncPtr fxn;
    xdc_UArg arg0;
    xdc_UArg arg1;
    xdc_UInt priority;
    xdc_UInt mask;
    xdc_Bool posted;
    xdc_UInt initTrigger;
    xdc_UInt trigger;
    ti_sysbios_knl_Queue_Handle readyQ;
    __TA_ti_sysbios_knl_Swi_Instance_State__hookEnv hookEnv;
} ti_sysbios_knl_Swi_Object__;

/* Object2__ */
typedef struct {
    xdc_runtime_Types_InstHdr hdr;
    ti_sysbios_knl_Swi_Object__ obj;
} ti_sysbios_knl_Swi_Object2__;


/*
 * ======== ti.sysbios.knl.Task INTERNALS ========
 */

/* Module__ */
typedef struct ti_sysbios_knl_Task_Module__ {
    xdc_runtime_Types_Link link;
} ti_sysbios_knl_Task_Module__;

/* Module__root__V */
extern ti_sysbios_knl_Task_Module__ ti_sysbios_knl_Task_Module__root__V;

/* <-- ti_sysbios_knl_Queue_Object */

/* Object__ */
typedef struct ti_sysbios_knl_Task_Object__ {
    ti_sysbios_knl_Queue_Elem qElem;
    volatile xdc_Int priority;
    xdc_UInt mask;
    xdc_Ptr context;
    ti_sysbios_knl_Task_Mode mode;
    ti_sysbios_knl_Task_PendElem *pendElem;
    xdc_SizeT stackSize;
    __TA_ti_sysbios_knl_Task_Instance_State__stack stack;
    xdc_runtime_IHeap_Handle stackHeap;
    ti_sysbios_knl_Task_FuncPtr fxn;
    xdc_UArg arg0;
    xdc_UArg arg1;
    xdc_Ptr env;
    __TA_ti_sysbios_knl_Task_Instance_State__hookEnv hookEnv;
    xdc_Bool vitalTaskFlag;
    ti_sysbios_knl_Queue_Handle readyQ;
    xdc_UInt curCoreId;
    xdc_UInt affinity;
} ti_sysbios_knl_Task_Object__;

/* Object2__ */
typedef struct {
    xdc_runtime_Types_InstHdr hdr;
    ti_sysbios_knl_Task_Object__ obj;
} ti_sysbios_knl_Task_Object2__;


/*
 * ======== ti.sysbios.knl.Task_SupportProxy INTERNALS ========
 */


/*
 * ======== ti.sysbios.rom.cortexm.cc26xx.cc26x2v2.CC26xx INTERNALS ========
 */


/*
 * ======== xdc.runtime.Assert INTERNALS ========
 */


/*
 * ======== xdc.runtime.Core INTERNALS ========
 */


/*
 * ======== xdc.runtime.Defaults INTERNALS ========
 */


/*
 * ======== xdc.runtime.Diags INTERNALS ========
 */


/*
 * ======== xdc.runtime.Error INTERNALS ========
 */


/*
 * ======== xdc.runtime.Gate INTERNALS ========
 */


/*
 * ======== xdc.runtime.Log INTERNALS ========
 */


/*
 * ======== xdc.runtime.Main INTERNALS ========
 */


/*
 * ======== xdc.runtime.Main_Module_GateProxy INTERNALS ========
 */

/* Module__ */
typedef struct xdc_runtime_Main_Module_GateProxy_Module__ {
    xdc_runtime_Types_Link link;
} xdc_runtime_Main_Module_GateProxy_Module__;

/* Module__root__V */
extern xdc_runtime_Main_Module_GateProxy_Module__ xdc_runtime_Main_Module_GateProxy_Module__root__V;

/* <-- ti_sysbios_gates_GateHwi_Object */

/* Object */
typedef ti_sysbios_gates_GateHwi_Object__ xdc_runtime_Main_Module_GateProxy_Object__;

/* Object2__ */
typedef struct {
    xdc_runtime_Types_InstHdr hdr;
    xdc_runtime_Main_Module_GateProxy_Object__ obj;
} xdc_runtime_Main_Module_GateProxy_Object2__;


/*
 * ======== xdc.runtime.Memory INTERNALS ========
 */


/*
 * ======== xdc.runtime.Memory_HeapProxy INTERNALS ========
 */

/* Module__ */
typedef struct xdc_runtime_Memory_HeapProxy_Module__ {
    xdc_runtime_Types_Link link;
} xdc_runtime_Memory_HeapProxy_Module__;

/* Module__root__V */
extern xdc_runtime_Memory_HeapProxy_Module__ xdc_runtime_Memory_HeapProxy_Module__root__V;

/* <-- ti_sysbios_heaps_HeapCallback_Object */

/* Object */
typedef ti_sysbios_heaps_HeapCallback_Object__ xdc_runtime_Memory_HeapProxy_Object__;

/* Object2__ */
typedef struct {
    xdc_runtime_Types_InstHdr hdr;
    xdc_runtime_Memory_HeapProxy_Object__ obj;
} xdc_runtime_Memory_HeapProxy_Object2__;


/*
 * ======== xdc.runtime.Registry INTERNALS ========
 */


/*
 * ======== xdc.runtime.Startup INTERNALS ========
 */


/*
 * ======== xdc.runtime.SysCallback INTERNALS ========
 */


/*
 * ======== xdc.runtime.System INTERNALS ========
 */


/*
 * ======== xdc.runtime.System_Module_GateProxy INTERNALS ========
 */

/* Module__ */
typedef struct xdc_runtime_System_Module_GateProxy_Module__ {
    xdc_runtime_Types_Link link;
} xdc_runtime_System_Module_GateProxy_Module__;

/* Module__root__V */
extern xdc_runtime_System_Module_GateProxy_Module__ xdc_runtime_System_Module_GateProxy_Module__root__V;

/* <-- ti_sysbios_gates_GateHwi_Object */

/* Object */
typedef ti_sysbios_gates_GateHwi_Object__ xdc_runtime_System_Module_GateProxy_Object__;

/* Object2__ */
typedef struct {
    xdc_runtime_Types_InstHdr hdr;
    xdc_runtime_System_Module_GateProxy_Object__ obj;
} xdc_runtime_System_Module_GateProxy_Object2__;


/*
 * ======== xdc.runtime.System_SupportProxy INTERNALS ========
 */


/*
 * ======== xdc.runtime.Text INTERNALS ========
 */


/*
 * ======== xdc.runtime.Timestamp INTERNALS ========
 */


/*
 * ======== xdc.runtime.Timestamp_SupportProxy INTERNALS ========
 */


/*
 * ======== xdc.runtime.Types INTERNALS ========
 */


/*
 * ======== INHERITS ========
 */

#pragma DATA_SECTION(xdc_runtime_ITimestampClient_Interface__BASE__C, ".const:xdc_runtime_ITimestampClient_Interface__BASE__C");
__FAR__ const xdc_runtime_Types_Base xdc_runtime_ITimestampClient_Interface__BASE__C = {&xdc_runtime_IModule_Interface__BASE__C};

#pragma DATA_SECTION(xdc_runtime_ISystemSupport_Interface__BASE__C, ".const:xdc_runtime_ISystemSupport_Interface__BASE__C");
__FAR__ const xdc_runtime_Types_Base xdc_runtime_ISystemSupport_Interface__BASE__C = {&xdc_runtime_IModule_Interface__BASE__C};

#pragma DATA_SECTION(ti_sysbios_interfaces_IIntrinsicsSupport_Interface__BASE__C, ".const:ti_sysbios_interfaces_IIntrinsicsSupport_Interface__BASE__C");
__FAR__ const xdc_runtime_Types_Base ti_sysbios_interfaces_IIntrinsicsSupport_Interface__BASE__C = {&xdc_runtime_IModule_Interface__BASE__C};


/*
 * ======== ti.sysbios.family.arm.m3.IntrinsicsSupport VTABLE ========
 */

/* Module__FXNS__C */
#pragma DATA_SECTION(ti_sysbios_family_arm_m3_IntrinsicsSupport_Module__FXNS__C, ".const:ti_sysbios_family_arm_m3_IntrinsicsSupport_Module__FXNS__C");
const ti_sysbios_family_arm_m3_IntrinsicsSupport_Fxns__ ti_sysbios_family_arm_m3_IntrinsicsSupport_Module__FXNS__C = {
    &ti_sysbios_interfaces_IIntrinsicsSupport_Interface__BASE__C, /* __base */
    &ti_sysbios_family_arm_m3_IntrinsicsSupport_Module__FXNS__C.__sfxns, /* __sysp */
    ti_sysbios_family_arm_m3_IntrinsicsSupport_maxbit__E,
    {
        NULL, /* __create */
        NULL, /* __delete */
        NULL, /* __label */
        0x25, /* __mid */
    } /* __sfxns */
};


/*
 * ======== ti.sysbios.gates.GateHwi VTABLE ========
 */



/*
 * ======== ti.sysbios.gates.GateMutex VTABLE ========
 */



/*
 * ======== ti.sysbios.gates.GateMutexPri VTABLE ========
 */

/* Module__FXNS__C */
#pragma DATA_SECTION(ti_sysbios_gates_GateMutexPri_Module__FXNS__C, ".const:ti_sysbios_gates_GateMutexPri_Module__FXNS__C");
const ti_sysbios_gates_GateMutexPri_Fxns__ ti_sysbios_gates_GateMutexPri_Module__FXNS__C = {
    &xdc_runtime_IGateProvider_Interface__BASE__C, /* __base */
    &ti_sysbios_gates_GateMutexPri_Module__FXNS__C.__sfxns, /* __sysp */
    ti_sysbios_gates_GateMutexPri_query__E,
    ti_sysbios_gates_GateMutexPri_enter__E,
    ti_sysbios_gates_GateMutexPri_leave__E,
    {
        ti_sysbios_gates_GateMutexPri_Object__create__S,
        ti_sysbios_gates_GateMutexPri_Object__delete__S,
        ti_sysbios_gates_GateMutexPri_Handle__label__S,
        0x2e, /* __mid */
    } /* __sfxns */
};


/*
 * ======== ti.sysbios.heaps.HeapCallback VTABLE ========
 */

/* Module__FXNS__C */
#pragma DATA_SECTION(ti_sysbios_heaps_HeapCallback_Module__FXNS__C, ".const:ti_sysbios_heaps_HeapCallback_Module__FXNS__C");
const ti_sysbios_heaps_HeapCallback_Fxns__ ti_sysbios_heaps_HeapCallback_Module__FXNS__C = {
    &xdc_runtime_IHeap_Interface__BASE__C, /* __base */
    &ti_sysbios_heaps_HeapCallback_Module__FXNS__C.__sfxns, /* __sysp */
    ti_sysbios_heaps_HeapCallback_alloc__E,
    ti_sysbios_heaps_HeapCallback_free__E,
    ti_sysbios_heaps_HeapCallback_isBlocking__E,
    ti_sysbios_heaps_HeapCallback_getStats__E,
    {
        ti_sysbios_heaps_HeapCallback_Object__create__S,
        ti_sysbios_heaps_HeapCallback_Object__delete__S,
        ti_sysbios_heaps_HeapCallback_Handle__label__S,
        0x32, /* __mid */
    } /* __sfxns */
};


/*
 * ======== ti.sysbios.heaps.HeapMem VTABLE ========
 */



/*
 * ======== ti.sysbios.heaps.HeapTrack VTABLE ========
 */



/*
 * ======== xdc.runtime.SysCallback VTABLE ========
 */

/* Module__FXNS__C */
#pragma DATA_SECTION(xdc_runtime_SysCallback_Module__FXNS__C, ".const:xdc_runtime_SysCallback_Module__FXNS__C");
const xdc_runtime_SysCallback_Fxns__ xdc_runtime_SysCallback_Module__FXNS__C = {
    &xdc_runtime_ISystemSupport_Interface__BASE__C, /* __base */
    &xdc_runtime_SysCallback_Module__FXNS__C.__sfxns, /* __sysp */
    xdc_runtime_SysCallback_abort__E,
    xdc_runtime_SysCallback_exit__E,
    xdc_runtime_SysCallback_flush__E,
    xdc_runtime_SysCallback_putch__E,
    xdc_runtime_SysCallback_ready__E,
    {
        NULL, /* __create */
        NULL, /* __delete */
        NULL, /* __label */
        0xd, /* __mid */
    } /* __sfxns */
};


/*
 * ======== xdc.runtime.Timestamp VTABLE ========
 */

/* Module__FXNS__C */
#pragma DATA_SECTION(xdc_runtime_Timestamp_Module__FXNS__C, ".const:xdc_runtime_Timestamp_Module__FXNS__C");
const xdc_runtime_Timestamp_Fxns__ xdc_runtime_Timestamp_Module__FXNS__C = {
    &xdc_runtime_ITimestampClient_Interface__BASE__C, /* __base */
    &xdc_runtime_Timestamp_Module__FXNS__C.__sfxns, /* __sysp */
    xdc_runtime_Timestamp_get32__E,
    xdc_runtime_Timestamp_get64__E,
    xdc_runtime_Timestamp_getFreq__E,
    {
        NULL, /* __create */
        NULL, /* __delete */
        NULL, /* __label */
        0xf, /* __mid */
    } /* __sfxns */
};


/*
 * ======== ti.sysbios.BIOS DECLARATIONS ========
 */

/* Module_State__ */
typedef struct ti_sysbios_BIOS_Module_State__ {
    xdc_runtime_Types_FreqHz cpuFreq;
    xdc_UInt rtsGateCount;
    xdc_IArg rtsGateKey;
    ti_sysbios_BIOS_RtsGateProxy_Handle rtsGate;
    ti_sysbios_BIOS_ThreadType threadType;
    __TA_ti_sysbios_BIOS_Module_State__smpThreadType smpThreadType;
    volatile ti_sysbios_BIOS_StartFuncPtr startFunc;
    volatile ti_sysbios_BIOS_ExitFuncPtr exitFunc;
} ti_sysbios_BIOS_Module_State__;

/* --> ti_sysbios_BIOS_startFunc */
extern xdc_Void ti_sysbios_BIOS_startFunc(xdc_Void);

/* --> ti_sysbios_BIOS_exitFunc */
extern xdc_Void ti_sysbios_BIOS_exitFunc(xdc_Int f_arg0);

/* Module__state__V */


/*
 * ======== ti.sysbios.BIOS_RtsGateProxy DECLARATIONS ========
 */


/*
 * ======== ti.sysbios.family.arm.cc26xx.Boot DECLARATIONS ========
 */


/*
 * ======== ti.sysbios.family.arm.cc26xx.Timer DECLARATIONS ========
 */

/* Object__table__V */
ti_sysbios_family_arm_cc26xx_Timer_Object__ ti_sysbios_family_arm_cc26xx_Timer_Object__table__V[1];

/* Module_State__ */
typedef struct ti_sysbios_family_arm_cc26xx_Timer_Module_State__ {
    xdc_UInt availMask;
    ti_sysbios_family_arm_cc26xx_Timer_Handle handle;
} ti_sysbios_family_arm_cc26xx_Timer_Module_State__;

/* Module__state__V */


/*
 * ======== ti.sysbios.family.arm.cc26xx.TimestampProvider DECLARATIONS ========
 */

/* Module_State__ */
typedef struct ti_sysbios_family_arm_cc26xx_TimestampProvider_Module_State__ {
    ti_sysbios_family_arm_cc26xx_Timer_Handle timer;
} ti_sysbios_family_arm_cc26xx_TimestampProvider_Module_State__;

/* Module__state__V */


/*
 * ======== ti.sysbios.family.arm.m3.Hwi DECLARATIONS ========
 */

/* Object__table__V */
ti_sysbios_family_arm_m3_Hwi_Object__ ti_sysbios_family_arm_m3_Hwi_Object__table__V[1];

/* Module_State__ */
typedef struct ti_sysbios_family_arm_m3_Hwi_Module_State__ {
    xdc_Char *taskSP;
    __TA_ti_sysbios_family_arm_m3_Hwi_Module_State__excActive excActive;
    __TA_ti_sysbios_family_arm_m3_Hwi_Module_State__excContext excContext;
    __TA_ti_sysbios_family_arm_m3_Hwi_Module_State__excStack excStack;
    xdc_Ptr isrStack;
    xdc_Ptr isrStackBase;
    xdc_Ptr isrStackSize;
    xdc_Ptr vectorTableBase;
    xdc_UInt swiTaskKeys;
    xdc_Ptr dispatchTable;
    volatile xdc_Bool vnvicFlushRequired;
    __TA_ti_sysbios_family_arm_m3_Hwi_Module_State__intAffinity intAffinity;
    __TA_ti_sysbios_family_arm_m3_Hwi_Module_State__intAffinityMasks intAffinityMasks;
} ti_sysbios_family_arm_m3_Hwi_Module_State__;

/* --> ti_sysbios_family_arm_m3_Hwi_Module_State_0_excActive__A */
__T1_ti_sysbios_family_arm_m3_Hwi_Module_State__excActive ti_sysbios_family_arm_m3_Hwi_Module_State_0_excActive__A[1];

/* --> ti_sysbios_family_arm_m3_Hwi_Module_State_0_excContext__A */
__T1_ti_sysbios_family_arm_m3_Hwi_Module_State__excContext ti_sysbios_family_arm_m3_Hwi_Module_State_0_excContext__A[1];

/* --> ti_sysbios_family_arm_m3_Hwi_Module_State_0_excStack__A */
__T1_ti_sysbios_family_arm_m3_Hwi_Module_State__excStack ti_sysbios_family_arm_m3_Hwi_Module_State_0_excStack__A[1];

/* --> __TI_STACK_BASE */
extern void* __TI_STACK_BASE;

/* --> __TI_STACK_SIZE */
extern void* __TI_STACK_SIZE;

/* Module__state__V */

/* --> ti_sysbios_family_arm_m3_Hwi_excHookFuncs__A */
const __T1_ti_sysbios_family_arm_m3_Hwi_excHookFuncs ti_sysbios_family_arm_m3_Hwi_excHookFuncs__A[2];

/* --> ti_sysbios_knl_Swi_disable__E */
extern xdc_UInt ti_sysbios_knl_Swi_disable__E(xdc_Void);

/* --> ti_sysbios_knl_Swi_restore__E */
extern xdc_Void ti_sysbios_knl_Swi_restore__E(xdc_UInt f_arg0);

/* --> ti_sysbios_knl_Swi_restoreHwi__E */
extern xdc_Void ti_sysbios_knl_Swi_restoreHwi__E(xdc_UInt f_arg0);

/* --> ti_sysbios_knl_Task_disable__E */
extern xdc_UInt ti_sysbios_knl_Task_disable__E(xdc_Void);

/* --> ti_sysbios_knl_Task_restoreHwi__E */
extern xdc_Void ti_sysbios_knl_Task_restoreHwi__E(xdc_UInt f_arg0);


/*
 * ======== ti.sysbios.family.arm.m3.IntrinsicsSupport DECLARATIONS ========
 */


/*
 * ======== ti.sysbios.family.arm.m3.TaskSupport DECLARATIONS ========
 */


/*
 * ======== ti.sysbios.gates.GateHwi DECLARATIONS ========
 */

/* Object__table__V */
ti_sysbios_gates_GateHwi_Object__ ti_sysbios_gates_GateHwi_Object__table__V[1];


/*
 * ======== ti.sysbios.gates.GateMutex DECLARATIONS ========
 */

/* Object__table__V */
ti_sysbios_gates_GateMutex_Object__ ti_sysbios_gates_GateMutex_Object__table__V[2];


/*
 * ======== ti.sysbios.gates.GateMutexPri DECLARATIONS ========
 */


/*
 * ======== ti.sysbios.hal.Hwi DECLARATIONS ========
 */


/*
 * ======== ti.sysbios.hal.Hwi_HwiProxy DECLARATIONS ========
 */


/*
 * ======== ti.sysbios.heaps.HeapCallback DECLARATIONS ========
 */

/* Object__table__V */
ti_sysbios_heaps_HeapCallback_Object__ ti_sysbios_heaps_HeapCallback_Object__table__V[1];

/* --> osalHeapAllocFxn */
extern xdc_Ptr osalHeapAllocFxn(xdc_UArg f_arg0,xdc_SizeT f_arg1,xdc_SizeT f_arg2);

/* --> ti_sysbios_heaps_HeapCallback_defaultCreate */
extern xdc_UArg ti_sysbios_heaps_HeapCallback_defaultCreate(xdc_UArg f_arg0);

/* --> ti_sysbios_heaps_HeapCallback_defaultDelete */
extern xdc_Void ti_sysbios_heaps_HeapCallback_defaultDelete(xdc_UArg f_arg0);

/* --> osalHeapFreeFxn */
extern xdc_Void osalHeapFreeFxn(xdc_UArg f_arg0,xdc_Ptr f_arg1,xdc_SizeT f_arg2);

/* --> osalHeapGetStatsFxn */
extern xdc_Void osalHeapGetStatsFxn(xdc_UArg f_arg0,xdc_runtime_Memory_Stats* f_arg1);

/* --> osalHeapInitFxn */
extern xdc_UArg osalHeapInitFxn(xdc_UArg f_arg0);

/* --> osalHeapIsBlockingFxn */
extern xdc_Bool osalHeapIsBlockingFxn(xdc_UArg f_arg0);


/*
 * ======== ti.sysbios.heaps.HeapMem DECLARATIONS ========
 */


/*
 * ======== ti.sysbios.heaps.HeapMem_Module_GateProxy DECLARATIONS ========
 */


/*
 * ======== ti.sysbios.heaps.HeapTrack DECLARATIONS ========
 */


/*
 * ======== ti.sysbios.knl.Clock DECLARATIONS ========
 */

/* Object__table__V */
ti_sysbios_knl_Clock_Object__ ti_sysbios_knl_Clock_Object__table__V[1];

/* Module_State__ */
typedef struct ti_sysbios_knl_Clock_Module_State__ {
    volatile xdc_UInt32 ticks;
    xdc_UInt swiCount;
    ti_sysbios_knl_Clock_TimerProxy_Handle timer;
    ti_sysbios_knl_Swi_Handle swi;
    volatile xdc_UInt numTickSkip;
    xdc_UInt32 nextScheduledTick;
    xdc_UInt32 maxSkippable;
    xdc_Bool inWorkFunc;
    volatile xdc_Bool startDuringWorkFunc;
    xdc_Bool ticking;
    ti_sysbios_knl_Queue_Object__ Object_field_clockQ;
} ti_sysbios_knl_Clock_Module_State__;

/* Module__state__V */

/* --> ti_sysbios_knl_Clock_doTick__I */
extern xdc_Void ti_sysbios_knl_Clock_doTick__I(xdc_UArg f_arg0);


/*
 * ======== ti.sysbios.knl.Clock_TimerProxy DECLARATIONS ========
 */


/*
 * ======== ti.sysbios.knl.Event DECLARATIONS ========
 */


/*
 * ======== ti.sysbios.knl.Idle DECLARATIONS ========
 */

/* --> Power_idleFunc */
extern xdc_Void Power_idleFunc(xdc_Void);

/* --> ti_sysbios_knl_Idle_funcList__A */
const __T1_ti_sysbios_knl_Idle_funcList ti_sysbios_knl_Idle_funcList__A[1];

/* --> ti_sysbios_knl_Idle_coreList__A */
const __T1_ti_sysbios_knl_Idle_coreList ti_sysbios_knl_Idle_coreList__A[1];


/*
 * ======== ti.sysbios.knl.Intrinsics DECLARATIONS ========
 */


/*
 * ======== ti.sysbios.knl.Intrinsics_SupportProxy DECLARATIONS ========
 */


/*
 * ======== ti.sysbios.knl.Mailbox DECLARATIONS ========
 */


/*
 * ======== ti.sysbios.knl.Queue DECLARATIONS ========
 */


/*
 * ======== ti.sysbios.knl.Semaphore DECLARATIONS ========
 */


/*
 * ======== ti.sysbios.knl.Swi DECLARATIONS ========
 */

/* Object__table__V */
ti_sysbios_knl_Swi_Object__ ti_sysbios_knl_Swi_Object__table__V[1];

/* Module_State__ */
typedef struct ti_sysbios_knl_Swi_Module_State__ {
    volatile xdc_Bool locked;
    xdc_UInt curSet;
    xdc_UInt curTrigger;
    ti_sysbios_knl_Swi_Handle curSwi;
    ti_sysbios_knl_Queue_Handle curQ;
    __TA_ti_sysbios_knl_Swi_Module_State__readyQ readyQ;
    __TA_ti_sysbios_knl_Swi_Module_State__constructedSwis constructedSwis;
} ti_sysbios_knl_Swi_Module_State__;

/* --> ti_sysbios_knl_Swi_Module_State_0_readyQ__A */
__T1_ti_sysbios_knl_Swi_Module_State__readyQ ti_sysbios_knl_Swi_Module_State_0_readyQ__A[6];

/* Module__state__V */

/* --> ti_sysbios_knl_Task_disable__E */
extern xdc_UInt ti_sysbios_knl_Task_disable__E(xdc_Void);

/* --> ti_sysbios_knl_Task_restore__E */
extern xdc_Void ti_sysbios_knl_Task_restore__E(xdc_UInt f_arg0);


/*
 * ======== ti.sysbios.knl.Task DECLARATIONS ========
 */

/* --> ti_sysbios_knl_Task_Instance_State_0_stack__A */
__T1_ti_sysbios_knl_Task_Instance_State__stack ti_sysbios_knl_Task_Instance_State_0_stack__A[512];
#if !(defined(__MACH__) && defined(__APPLE__))
__T1_ti_sysbios_knl_Task_Instance_State__stack ti_sysbios_knl_Task_Instance_State_0_stack__A[512] __attribute__ ((section(".bss:taskStackSection"), aligned(8)));
#endif

/* Object__table__V */
ti_sysbios_knl_Task_Object__ ti_sysbios_knl_Task_Object__table__V[1];

/* Module_State__ */
typedef struct ti_sysbios_knl_Task_Module_State__ {
    volatile xdc_Bool locked;
    volatile xdc_UInt curSet;
    volatile xdc_Bool workFlag;
    xdc_UInt vitalTasks;
    ti_sysbios_knl_Task_Handle curTask;
    ti_sysbios_knl_Queue_Handle curQ;
    __TA_ti_sysbios_knl_Task_Module_State__readyQ readyQ;
    __TA_ti_sysbios_knl_Task_Module_State__smpCurSet smpCurSet;
    __TA_ti_sysbios_knl_Task_Module_State__smpCurMask smpCurMask;
    __TA_ti_sysbios_knl_Task_Module_State__smpCurTask smpCurTask;
    __TA_ti_sysbios_knl_Task_Module_State__smpReadyQ smpReadyQ;
    __TA_ti_sysbios_knl_Task_Module_State__idleTask idleTask;
    __TA_ti_sysbios_knl_Task_Module_State__constructedTasks constructedTasks;
    ti_sysbios_knl_Queue_Object__ Object_field_inactiveQ;
    ti_sysbios_knl_Queue_Object__ Object_field_terminatedQ;
} ti_sysbios_knl_Task_Module_State__;

/* --> ti_sysbios_knl_Task_Module_State_0_readyQ__A */
__T1_ti_sysbios_knl_Task_Module_State__readyQ ti_sysbios_knl_Task_Module_State_0_readyQ__A[6];

/* --> ti_sysbios_knl_Task_Module_State_0_idleTask__A */
__T1_ti_sysbios_knl_Task_Module_State__idleTask ti_sysbios_knl_Task_Module_State_0_idleTask__A[1];

/* Module__state__V */


/*
 * ======== ti.sysbios.knl.Task_SupportProxy DECLARATIONS ========
 */


/*
 * ======== ti.sysbios.rom.cortexm.cc26xx.cc26x2v2.CC26xx DECLARATIONS ========
 */


/*
 * ======== xdc.runtime.Assert DECLARATIONS ========
 */


/*
 * ======== xdc.runtime.Core DECLARATIONS ========
 */


/*
 * ======== xdc.runtime.Defaults DECLARATIONS ========
 */


/*
 * ======== xdc.runtime.Diags DECLARATIONS ========
 */


/*
 * ======== xdc.runtime.Error DECLARATIONS ========
 */

/* Module_State__ */
typedef struct xdc_runtime_Error_Module_State__ {
    xdc_UInt16 count;
} xdc_runtime_Error_Module_State__;

/* Module__state__V */
xdc_runtime_Error_Module_State__ xdc_runtime_Error_Module__state__V;


/*
 * ======== xdc.runtime.Gate DECLARATIONS ========
 */


/*
 * ======== xdc.runtime.Log DECLARATIONS ========
 */


/*
 * ======== xdc.runtime.Main DECLARATIONS ========
 */


/*
 * ======== xdc.runtime.Main_Module_GateProxy DECLARATIONS ========
 */


/*
 * ======== xdc.runtime.Memory DECLARATIONS ========
 */

/* Module_State__ */
typedef struct xdc_runtime_Memory_Module_State__ {
    xdc_SizeT maxDefaultTypeAlign;
} xdc_runtime_Memory_Module_State__;

/* Module__state__V */


/*
 * ======== xdc.runtime.Memory_HeapProxy DECLARATIONS ========
 */


/*
 * ======== xdc.runtime.Registry DECLARATIONS ========
 */

/* Module_State__ */
typedef struct xdc_runtime_Registry_Module_State__ {
    xdc_runtime_Registry_Desc *listHead;
    xdc_runtime_Types_ModuleId curId;
} xdc_runtime_Registry_Module_State__;

/* Module__state__V */


/*
 * ======== xdc.runtime.Startup DECLARATIONS ========
 */

/* Module_State__ */
typedef struct xdc_runtime_Startup_Module_State__ {
    xdc_Int *stateTab;
    xdc_Bool execFlag;
    xdc_Bool rtsDoneFlag;
} xdc_runtime_Startup_Module_State__;

/* Module__state__V */

/* --> ti_sysbios_hal_Hwi_initStack */
extern xdc_Void ti_sysbios_hal_Hwi_initStack(xdc_Void);

/* --> xdc_runtime_Startup_firstFxns__A */
const __T1_xdc_runtime_Startup_firstFxns xdc_runtime_Startup_firstFxns__A[3];

/* --> xdc_runtime_System_Module_startup__E */
extern xdc_Int xdc_runtime_System_Module_startup__E(xdc_Int f_arg0);

/* --> ti_sysbios_knl_Clock_Module_startup__E */
extern xdc_Int ti_sysbios_knl_Clock_Module_startup__E(xdc_Int f_arg0);

/* --> ti_sysbios_knl_Mailbox_Module_startup__E */
extern xdc_Int ti_sysbios_knl_Mailbox_Module_startup__E(xdc_Int f_arg0);

/* --> ti_sysbios_knl_Swi_Module_startup__E */
extern xdc_Int ti_sysbios_knl_Swi_Module_startup__E(xdc_Int f_arg0);

/* --> ti_sysbios_knl_Task_Module_startup__E */
extern xdc_Int ti_sysbios_knl_Task_Module_startup__E(xdc_Int f_arg0);

/* --> ti_sysbios_family_arm_m3_Hwi_Module_startup__E */
extern xdc_Int ti_sysbios_family_arm_m3_Hwi_Module_startup__E(xdc_Int f_arg0);

/* --> ti_sysbios_family_arm_cc26xx_Timer_Module_startup__E */
extern xdc_Int ti_sysbios_family_arm_cc26xx_Timer_Module_startup__E(xdc_Int f_arg0);

/* --> ti_sysbios_family_arm_cc26xx_TimestampProvider_Module_startup__E */
extern xdc_Int ti_sysbios_family_arm_cc26xx_TimestampProvider_Module_startup__E(xdc_Int f_arg0);

/* --> ti_sysbios_hal_Hwi_Module_startup__E */
extern xdc_Int ti_sysbios_hal_Hwi_Module_startup__E(xdc_Int f_arg0);

/* --> ti_sysbios_heaps_HeapCallback_Module_startup__E */
extern xdc_Int ti_sysbios_heaps_HeapCallback_Module_startup__E(xdc_Int f_arg0);

/* --> xdc_runtime_Startup_sfxnTab__A */
const __T1_xdc_runtime_Startup_sfxnTab xdc_runtime_Startup_sfxnTab__A[10];

/* --> xdc_runtime_Startup_sfxnRts__A */
const __T1_xdc_runtime_Startup_sfxnRts xdc_runtime_Startup_sfxnRts__A[10];


/*
 * ======== xdc.runtime.SysCallback DECLARATIONS ========
 */

/* --> xdc_runtime_SysCallback_defaultAbort */
extern xdc_Void xdc_runtime_SysCallback_defaultAbort(xdc_CString f_arg0);

/* --> xdc_runtime_SysCallback_defaultExit */
extern xdc_Void xdc_runtime_SysCallback_defaultExit(xdc_Int f_arg0);

/* --> xdc_runtime_SysCallback_defaultFlush */
extern xdc_Void xdc_runtime_SysCallback_defaultFlush(xdc_Void);

/* --> xdc_runtime_SysCallback_defaultPutch */
extern xdc_Void xdc_runtime_SysCallback_defaultPutch(xdc_Char f_arg0);

/* --> xdc_runtime_SysCallback_defaultReady */
extern xdc_Bool xdc_runtime_SysCallback_defaultReady(xdc_Void);


/*
 * ======== xdc.runtime.System DECLARATIONS ========
 */

/* Module_State__ */
typedef struct xdc_runtime_System_Module_State__ {
    __TA_xdc_runtime_System_Module_State__atexitHandlers atexitHandlers;
    xdc_Int numAtexitHandlers;
} xdc_runtime_System_Module_State__;

/* Module__state__V */

/* --> xdc_runtime_System_printfExtend__I */
extern xdc_Int xdc_runtime_System_printfExtend__I(xdc_Char** f_arg0,xdc_CString* f_arg1,xdc_VaList* f_arg2,xdc_runtime_System_ParseData* f_arg3);


/*
 * ======== xdc.runtime.System_Module_GateProxy DECLARATIONS ========
 */


/*
 * ======== xdc.runtime.System_SupportProxy DECLARATIONS ========
 */


/*
 * ======== xdc.runtime.Text DECLARATIONS ========
 */

/* Module_State__ */
typedef struct xdc_runtime_Text_Module_State__ {
    xdc_CPtr charBase;
    xdc_CPtr nodeBase;
} xdc_runtime_Text_Module_State__;

/* Module__state__V */
xdc_runtime_Text_Module_State__ xdc_runtime_Text_Module__state__V;

/* --> xdc_runtime_Text_charTab__A */
const __T1_xdc_runtime_Text_charTab xdc_runtime_Text_charTab__A[1];

/* --> xdc_runtime_Text_nodeTab__A */
const __T1_xdc_runtime_Text_nodeTab xdc_runtime_Text_nodeTab__A[1];


/*
 * ======== xdc.runtime.Timestamp DECLARATIONS ========
 */


/*
 * ======== xdc.runtime.Timestamp_SupportProxy DECLARATIONS ========
 */


/*
 * ======== xdc.runtime.Types DECLARATIONS ========
 */


/*
 * ======== OBJECT OFFSETS ========
 */



/*
 * ======== OBJECT OFFSETS ========
 */

#pragma DATA_SECTION(ti_sysbios_gates_GateMutexPri_Instance_State_pendQ__O, ".const:ti_sysbios_gates_GateMutexPri_Instance_State_pendQ__O");
__FAR__ const xdc_SizeT ti_sysbios_gates_GateMutexPri_Instance_State_pendQ__O = offsetof(ti_sysbios_gates_GateMutexPri_Object__,Object_field_pendQ);


/*
 * ======== OBJECT OFFSETS ========
 */

#pragma DATA_SECTION(ti_sysbios_heaps_HeapTrack_Instance_State_trackQueue__O, ".const:ti_sysbios_heaps_HeapTrack_Instance_State_trackQueue__O");
__FAR__ const xdc_SizeT ti_sysbios_heaps_HeapTrack_Instance_State_trackQueue__O = offsetof(ti_sysbios_heaps_HeapTrack_Object__,Object_field_trackQueue);


/*
 * ======== OBJECT OFFSETS ========
 */



/*
 * ======== OBJECT OFFSETS ========
 */



/*
 * ======== OBJECT OFFSETS ========
 */



/*
 * ======== OBJECT OFFSETS ========
 */



/*
 * ======== OBJECT OFFSETS ========
 */

#pragma DATA_SECTION(ti_sysbios_knl_Task_Module_State_terminatedQ__O, ".const:ti_sysbios_knl_Task_Module_State_terminatedQ__O");
__FAR__ const xdc_SizeT ti_sysbios_knl_Task_Module_State_terminatedQ__O = offsetof(ti_sysbios_knl_Task_Module_State__,Object_field_terminatedQ);


/*
 * ======== xdc.cfg.Program TEMPLATE ========
 */

/*
 *  ======== __ASM__ ========
 *  Define absolute path prefix for this executable's
 *  configuration generated files.
 */
xdc__META(__ASM__, "@(#)__ASM__ = C:/Users/Patrick/workspace_v10/zed_temperaturesensor_CC1352R1_LAUNCHXL_tirtos_ccs/default/configPkg/package/cfg/app_pem4f");

/*
 *  ======== __ISA__ ========
 *  Define the ISA of this executable.  This symbol is used by platform
 *  specific "exec" commands that support more than one ISA; e.g., gdb
 */
xdc__META(__ISA__, "@(#)__ISA__ = v7M4");

/*
 *  ======== __PLAT__ ========
 *  Define the name of the platform that can run this executable.  This
 *  symbol is used by platform independent "exec" commands
 */
xdc__META(__PLAT__, "@(#)__PLAT__ = ti.platforms.simplelink");

/*
 *  ======== __TARG__ ========
 *  Define the name of the target used to build this executable.
 */
xdc__META(__TARG__, "@(#)__TARG__ = ti.targets.arm.elf.M4F");

/*
 *  ======== __TRDR__ ========
 *  Define the name of the class that can read/parse this executable.
 */
xdc__META(__TRDR__, "@(#)__TRDR__ = xdc.targets.omf.Elf");


/*
 * ======== xdc.cfg.SourceDir TEMPLATE ========
 */



/*
 * ======== xdc.runtime.Diags TEMPLATE ========
 */



/*
 * ======== xdc.runtime.Error TEMPLATE ========
 */


xdc_runtime_Error_Block xdc_runtime_Error_IgnoreBlock = {
    (unsigned short)(~0U), /* unused */
    {
        {0, 0} /* data */
    },
    0,  /* id */
    NULL,  /* msg */
    {
        0,  /* mod */
        NULL,  /* file */
        0   /* line */
    }
};

/*
 *  ======== Error_policyLog ========
 */
Void xdc_runtime_Error_policyLog__I(xdc_runtime_Types_ModuleId mod,
    CString file, Int line, CString msg, IArg arg1, IArg arg2)
{
}

/*
 * ======== xdc.runtime.Startup TEMPLATE ========
 */

/*
 *  ======== MODULE STARTUP DONE FUNCTIONS ========
 */
/* REQ_TAG(SYSBIOS-953) */
xdc_Bool ti_sysbios_heaps_HeapCallback_Module__startupDone__F(void); /* keep GCC prototype warning quiet */
xdc_Bool ti_sysbios_heaps_HeapCallback_Module__startupDone__F(void) {
    return (xdc_Bool)((&xdc_runtime_Startup_Module__state__V)->stateTab == NULL || (&xdc_runtime_Startup_Module__state__V)->stateTab[9] < 0);
}

xdc_Int xdc_runtime_Startup_getState__I(xdc_runtime_Types_ModuleId id) {
    switch (id) {
        case 12:
            return ((&xdc_runtime_Startup_Module__state__V)->stateTab[0]);
        case 22:
            return ((&xdc_runtime_Startup_Module__state__V)->stateTab[1]);
        case 26:
            return ((&xdc_runtime_Startup_Module__state__V)->stateTab[2]);
        case 29:
            return ((&xdc_runtime_Startup_Module__state__V)->stateTab[3]);
        case 30:
            return ((&xdc_runtime_Startup_Module__state__V)->stateTab[4]);
        case 36:
            return ((&xdc_runtime_Startup_Module__state__V)->stateTab[5]);
        case 40:
            return ((&xdc_runtime_Startup_Module__state__V)->stateTab[6]);
        case 41:
            return ((&xdc_runtime_Startup_Module__state__V)->stateTab[7]);
        case 43:
            return ((&xdc_runtime_Startup_Module__state__V)->stateTab[8]);
    }
    return (0);
}

/*
 * Startup_exec__I is an internal entry point called by target/platform boot
 * code. Boot code is not brought into a partial-link assembly. So, without this
 * attribute, whole program optimizers would otherwise optimize-out this
 * function.
 */
xdc_Void xdc_runtime_Startup_exec__I(void) __attribute__ ((used));

/*
 *  ======== xdc_runtime_Startup_exec__I ========
 *  Initialize all used modules that have startup functions
 */
/* REQ_TAG(SYSBIOS-949) */
xdc_Void xdc_runtime_Startup_exec__I(void)
{
    xdc_Int state[10];
    xdc_runtime_Startup_startModsFxn__C(state, 10);
}

/*
 * ======== xdc.runtime.Reset TEMPLATE ========
 */

/*
 * Startup_reset__I is an internal entry point called by target/platform boot
 * code. Boot code is not brought into a partial-link assembly. So, without this
 * pragma, whole program optimizers would otherwise optimize-out this function.
 */
xdc_Void xdc_runtime_Startup_reset__I(void) __attribute__ ((used));

extern xdc_Void ti_sysbios_family_arm_cc26xx_Boot_trimDevice(void);  /* user defined reset function */
extern xdc_Void ti_sysbios_rom_cortexm_cc26xx_cc26x2v2_CC26xx_checkRevision__E(void);  /* user defined reset function */

/*
 *  ======== xdc_runtime_Startup_reset__I ========
 *  This function is called by bootstrap initialization code as early as
 *  possible in the startup process.  This function calls all functions in
 *  the Reset.fxns array _as well as_ Startup.resetFxn (if it's non-NULL)
 */
xdc_Void xdc_runtime_Startup_reset__I(void)
{
    ti_sysbios_family_arm_cc26xx_Boot_trimDevice();
    ti_sysbios_rom_cortexm_cc26xx_cc26x2v2_CC26xx_checkRevision__E();
}

/*
 * ======== xdc.runtime.System TEMPLATE ========
 */


#include <xdc/std.h>
#include <limits.h>
#include <xdc/runtime/Types.h>

#include <xdc/runtime/System.h>
#include <xdc/runtime/System__internal.h>

/*
 *  ======== System_printfExtend__I ========
 *  This function processes optional extended formats of printf.
 *
 *  It returns the number of characters added to the result.
 *
 *  Precision (maximum string length) is not supported for %$S.
 *
 *  Right-justified (which is default) minimum width is not supported
 *  for %$L, %$S, or %$F.
 */
/* REQ_TAG(SYSBIOS-1072) */
xdc_Int xdc_runtime_System_printfExtend__I(xdc_Char **pbuf, xdc_CString *pfmt,
    xdc_VaList *pva, xdc_runtime_System_ParseData *parse)
{
    xdc_Int     res;
    xdc_Char    c;
    xdc_Bool    found = FALSE;

    /*
     * Create a local variable 'va' to ensure that the dereference of
     * pva only occurs once.
     */
    va_list va = *pva;

    res = 0;

    c = **pfmt;
    *pfmt = *pfmt + 1;


    if (c == '$') {
        c = **pfmt;
        *pfmt = *pfmt + 1;

        if (c == 'L') {
            xdc_runtime_Types_Label *lab = (parse->aFlag == TRUE) ?
                (xdc_runtime_Types_Label *)xdc_iargToPtr(va_arg(va, xdc_IArg)) :
                (xdc_runtime_Types_Label *)va_arg(va, void *);

            /*
             * Call Text_putLab to write out the label, taking the precision
             * into account.
             */
            res = xdc_runtime_Text_putLab(lab, pbuf, parse->precis);

            /*
             * Set the length to 0 to indicate to 'doPrint' that nothing should
             * be copied from parse.ptr.
             */
            parse->len = 0;

            /* Update the minimum width field. */
            parse->width -= res;

            found = TRUE;
        }

        if (c == 'F') {
            xdc_runtime_Types_Site site;

            /* Retrieve the file name string from the argument list */
            site.file = (parse->aFlag == TRUE) ?
                (xdc_Char *) xdc_iargToPtr(va_arg(va, xdc_IArg)) :
                (xdc_Char *) va_arg(va, xdc_Char *);

            /* Retrieve the line number from the argument list. */
            site.line = (parse->aFlag == TRUE) ?
                (xdc_Int) va_arg(va, xdc_IArg) :
                (xdc_Int) va_arg(va, xdc_Int);

            /*
             * Omit the 'mod' field, set it to 0.
             * '0' is a safe sentinel value - the IDs for named modules are
             * 0x8000 and higher, and the IDs for unnamed modules go from 0x1
             * to 0x7fff.
             */
            site.mod = 0;

            /*
             * Call putSite to format the file and line number.
             * If a precision was specified, it will be used as the maximum
             * string length.
             */
            res = xdc_runtime_Text_putSite(&site, pbuf, parse->precis);

            /*
             * Set the length to 0 to indicate to 'doPrint' that nothing should
             * be copied from parse.ptr.
             */
            parse->len = 0;

            /* Update the minimum width field */
            parse->width -= res;

            found = TRUE;
        }

        if (c == 'S') {
            /* Retrieve the format string from the argument list */
            parse->ptr = (parse->aFlag == TRUE) ?
                (xdc_Char *) xdc_iargToPtr(va_arg(va, xdc_IArg)) :
                (xdc_Char *) va_arg(va, xdc_Char *);

            /* Update pva before passing it to doPrint. */
            *pva = va;

            /* Perform the recursive format. System_doPrint does not advance
             * the buffer pointer, so it has to be done explicitly.
             * System_doPrint guarantees that parse->precis is positive.
             */
            res = xdc_runtime_System_doPrint__I(*pbuf, (xdc_SizeT)parse->precis,
                                                parse->ptr, pva, parse->aFlag);

            if (*pbuf != NULL) {
                if (res >= parse->precis) {
                    /* Not enough space for all characters, only
                     * (parse->precis - 1) and '\0' were printed.
                     */
                    res = parse->precis - 1;
                }
                *pbuf += res;
            }

            /* Update the temporary variable with any changes to *pva */
            va = *pva;

            /*
             * Set the length to 0 to indicate to 'doPrint' that nothing should
             * be copied from parse.ptr
             */
            parse->len = 0;

            /* Update the minimum width field */
            parse->width -= res;

            /* Indicate that we were able to interpret the specifier */
            found = TRUE;
        }

    }

    if (c == 'f') {
        /* support arguments _after_ optional float support */
        if (parse->aFlag == TRUE) {
            (void)va_arg(va, xdc_IArg);
        }
        else {
            (void)va_arg(va, double);
        }
    }

    if (found == FALSE) {
        /* other character (like %) copy to output */
        *(parse->ptr) = c;
        parse->len = 1;
    }

    /*
     * Before returning, we must update the value of pva. We use a label here
     * so that all return points will go through this update.
     * The 'goto end' is here to ensure that there is always a reference to the
     * label (to avoid the compiler complaining).
     */
    goto end;
end:
    *pva = va;
    return (res);
}

/*
 * ======== xdc.runtime.Text TEMPLATE ========
 */

/*
 *  ======== xdc_runtime_Text_visitRope__I ========
 *  This function is indirectly called within Text.c through
 *  the visitRopeFxn configuration parameter of xdc.runtime.Text.
 */
void xdc_runtime_Text_visitRope__I(xdc_runtime_Text_RopeId rope,
    xdc_runtime_Text_RopeVisitor visFxn, xdc_Ptr visState)
{
    ((xdc_runtime_Text_MatchVisState *)visState)->res = -1;
}

/*
 * ======== ti.platforms.simplelink.Platform TEMPLATE ========
 */



/*
 * ======== ti.sysbios.knl.Clock TEMPLATE ========
 */

Void ti_sysbios_knl_Clock_doTick__I(UArg arg)
{
    ti_sysbios_knl_Clock_logTick__E();

    {
        ti_sysbios_knl_Swi_post((&ti_sysbios_knl_Clock_Module__state__V)->swi);
    }
}

/*
 * ======== ti.sysbios.knl.Task TEMPLATE ========
 */




/*
 * ======== ti.sysbios.BIOS TEMPLATE ========
 */


Void ti_sysbios_BIOS_atExitFunc__I(Int stat);

extern Void ti_sysbios_BIOS_registerRTSLock(Void);
extern Void ti_sysbios_family_arm_cc26xx_Timer_startup__E(Void);

Void ti_sysbios_BIOS_startFunc__I(Void)
{
    /*
     *  Check if XDC runtime startup functions have been called. If not, then
     *  call BIOS_linkedWithIncorrectBootLibrary() function. This function
     *  will spin forever.
     */
    if (xdc_runtime_Startup_rtsDone() != TRUE) {
        ti_sysbios_BIOS_linkedWithIncorrectBootLibrary();
    }

    (void)xdc_runtime_System_atexit(
        (xdc_runtime_System_AtexitHandler)ti_sysbios_BIOS_atExitFunc__I);
    ti_sysbios_BIOS_registerRTSLock();
    ti_sysbios_family_arm_cc26xx_Timer_startup__E();
    ti_sysbios_hal_Hwi_startup();
    ti_sysbios_knl_Swi_startup();
    ti_sysbios_knl_Task_startup();
}

#include <_lock.h>

Void ti_sysbios_BIOS_atExitFunc__I(Int notused)
{
    ti_sysbios_knl_Swi_disable();
    (void)ti_sysbios_knl_Task_disable();
    (void)ti_sysbios_BIOS_setThreadType(ti_sysbios_BIOS_ThreadType_Main);

    if ((&ti_sysbios_BIOS_Module__state__V)->rtsGate != NULL) {
        _register_lock(_nop);
        _register_unlock(_nop);
    }
}

/*
 *  ======== BIOS_rtsLock ========
 *  Called by rts _lock() function
 */
Void ti_sysbios_BIOS_rtsLock()
{
    IArg key;

    key = ti_sysbios_BIOS_RtsGateProxy_enter((&ti_sysbios_BIOS_Module__state__V)->rtsGate);
    if ((&ti_sysbios_BIOS_Module__state__V)->rtsGateCount == 0) {
        (&ti_sysbios_BIOS_Module__state__V)->rtsGateKey = key;
    }
    /* Increment need not be atomic */
    (&ti_sysbios_BIOS_Module__state__V)->rtsGateCount++;
}

/*
 *  ======== BIOS_rtsUnLock ========
 *  Called by rts _unlock() function
 */
Void ti_sysbios_BIOS_rtsUnlock()
{
    (&ti_sysbios_BIOS_Module__state__V)->rtsGateCount--;

    if ((&ti_sysbios_BIOS_Module__state__V)->rtsGateCount == 0) {
        ti_sysbios_BIOS_RtsGateProxy_leave((&ti_sysbios_BIOS_Module__state__V)->rtsGate, (&ti_sysbios_BIOS_Module__state__V)->rtsGateKey);
    }
}

/*
 *  ======== BIOS_nullFunc ========
 */
Void ti_sysbios_BIOS_nullFunc__I(Void)
{
}

/*
 *  ======== BIOS_registerRTSLock ========
 */
Void ti_sysbios_BIOS_registerRTSLock(Void)
{
    if ((&ti_sysbios_BIOS_Module__state__V)->rtsGate != NULL) {
        _register_lock(ti_sysbios_BIOS_rtsLock);
        _register_unlock(ti_sysbios_BIOS_rtsUnlock);
    }
}

/*
 *  ======== BIOS_removeRTSLock ========
 */
Void ti_sysbios_BIOS_removeRTSLock(Void)
{
    if ((&ti_sysbios_BIOS_Module__state__V)->rtsGate != NULL) {
        _register_lock(ti_sysbios_BIOS_nullFunc);
        _register_unlock(ti_sysbios_BIOS_nullFunc);
    }
}

/*
 *  ======== BIOS_exitFunc ========
 */
Void ti_sysbios_BIOS_exitFunc(Int stat)
{
    /* remove the RTS lock */
    ti_sysbios_BIOS_removeRTSLock();

    /* force thread type to 'Main' */
    (void)ti_sysbios_BIOS_setThreadType(ti_sysbios_BIOS_ThreadType_Main);

    xdc_runtime_System_exit(stat);
}

/*
 *  ======== BIOS_errorRaiseHook ========
 */
Void ti_sysbios_BIOS_errorRaiseHook(xdc_runtime_Error_Block *eb)
{
    /*
     * If this is an Assert thread, defang Gate threadtype check
     */
    if (eb->id == xdc_runtime_Assert_E_assertFailed) {
        /* remove the RTS lock */
        ti_sysbios_BIOS_removeRTSLock();
        /* force thread type to 'Main' */
        ti_sysbios_BIOS_setThreadType(ti_sysbios_BIOS_ThreadType_Main);
    }
}

/*
 * ======== ti.sysbios.Build TEMPLATE ========
 */


/*
 * ======== ti.sysbios.family.arm.m3.Hwi TEMPLATE ========
 */

extern Void _c_int00(Void);
extern Void ti_sysbios_family_arm_m3_Hwi_excHandlerAsm__I(Void);
extern Void ti_sysbios_family_arm_m3_Hwi_excHandlerAsm__I(Void);
extern Void ti_sysbios_family_arm_m3_Hwi_excHandlerAsm__I(Void);
extern Void ti_sysbios_family_arm_m3_Hwi_excHandlerAsm__I(Void);
extern Void ti_sysbios_family_arm_m3_Hwi_excHandlerAsm__I(Void);
extern Void ti_sysbios_family_arm_m3_Hwi_excHandlerAsm__I(Void);
extern Void ti_sysbios_family_arm_m3_Hwi_excHandlerAsm__I(Void);
extern Void ti_sysbios_family_arm_m3_Hwi_excHandlerAsm__I(Void);


#pragma DATA_SECTION(ti_sysbios_family_arm_m3_Hwi_resetVectors, ".resetVecs");

/* const because it is meant to be placed in ROM */
const UInt32 ti_sysbios_family_arm_m3_Hwi_resetVectors[] = {
    (UInt32)(&__TI_STACK_BASE),
    (UInt32)(&_c_int00),
    (UInt32)(&ti_sysbios_family_arm_m3_Hwi_excHandlerAsm__I),            /* NMI */
    (UInt32)(&ti_sysbios_family_arm_m3_Hwi_excHandlerAsm__I),      /* Hard Fault */
    (UInt32)(&ti_sysbios_family_arm_m3_Hwi_excHandlerAsm__I),       /* Mem Fault */
    (UInt32)(&ti_sysbios_family_arm_m3_Hwi_excHandlerAsm__I),       /* Bus Fault */
    (UInt32)(&ti_sysbios_family_arm_m3_Hwi_excHandlerAsm__I),     /* Usage Fault */
    (UInt32)(&ti_sysbios_family_arm_m3_Hwi_excHandlerAsm__I),       /* reserved */
    (UInt32)(&ti_sysbios_family_arm_m3_Hwi_excHandlerAsm__I),       /* reserved */
    (UInt32)(&ti_sysbios_family_arm_m3_Hwi_excHandlerAsm__I),       /* reserved */
    (UInt32)(&ti_sysbios_family_arm_m3_Hwi_excHandlerAsm__I),       /* reserved */
    (UInt32)(&ti_sysbios_family_arm_m3_Hwi_excHandlerAsm__I),         /* SVCall */
    (UInt32)(&ti_sysbios_family_arm_m3_Hwi_excHandlerAsm__I),       /* Debug Mon */
    (UInt32)(&ti_sysbios_family_arm_m3_Hwi_excHandlerAsm__I),       /* reserved */
    (UInt32)(&ti_sysbios_family_arm_m3_Hwi_pendSV__I),  /* pendSV */
};

#pragma DATA_SECTION(ti_sysbios_family_arm_m3_Hwi_ramVectors, ".vecs");

/* place holder for RAM vector table */
UInt32 ti_sysbios_family_arm_m3_Hwi_ramVectors[54];

UInt32 ti_sysbios_family_arm_m3_Hwi_dispatchTable[54];

#if defined(__IAR_SYSTEMS_ICC__)
Void ti_sysbios_family_arm_m3_Hwi_initIsrStackSize()
{
    #pragma section = "CSTACK"
    ti_sysbios_family_arm_m3_Hwi_Module__state__V.isrStackBase = (Void *)__section_begin("CSTACK");
    size_t size = (uint8_t *)__section_end("CSTACK") - (uint8_t *)__section_begin("CSTACK");
    ti_sysbios_family_arm_m3_Hwi_Module__state__V.isrStackSize = (Void *)size;
}
#endif

/*
 * ======== ti.sysbios.family.arm.cc26xx.Boot TEMPLATE ========
 */


#include <ti/devices/DeviceFamily.h>

#include DeviceFamily_constructPath(inc/hw_types.h)


extern Void _c_int00();

Void ResetISR ()
{
    _c_int00();
}

/* workaround bug in driverlib */

/*
 * ======== ti.sysbios.rom.ROM TEMPLATE ========
 */


/* ROM_ExternFuncPtrs */
#include <xdc/runtime/System.h>
#include <xdc/runtime/Startup.h>
#include <ti/sysbios/family/arm/cc26xx/Timer.h>
#include <ti/sysbios/family/arm/cc26xx/TimestampProvider.h>

typedef struct {
    /*
     *  functions explicitly excluded from the ROM
     */
    xdc_Int (*xdc_runtime_Startup_getState__I)(xdc_runtime_Types_ModuleId);
    xdc_Bool (*xdc_runtime_System_SupportProxy_Module__startupDone__S)(xdc_Void);
    xdc_Void (*xdc_runtime_System_SupportProxy_abort__E)(xdc_CString);
    xdc_Void (*xdc_runtime_System_SupportProxy_exit__E)( xdc_Int);
    xdc_Void (*xdc_runtime_System_SupportProxy_flush__E)(xdc_Void);
    xdc_Void (*xdc_runtime_System_SupportProxy_putch__E)( xdc_Char);
    xdc_Bool (*xdc_runtime_System_SupportProxy_ready__E)(xdc_Void);
    xdc_Void (*ti_sysbios_family_arm_cc26xx_Timer_start__E)(ti_sysbios_family_arm_cc26xx_Timer_Handle);
    xdc_Void (*ti_sysbios_family_arm_cc26xx_Timer_initDevice__I)(ti_sysbios_family_arm_cc26xx_Timer_Object *);
    xdc_Void (*ti_sysbios_family_arm_cc26xx_Timer_setThreshold__I)(ti_sysbios_family_arm_cc26xx_Timer_Object *, xdc_UInt32, xdc_Bool);
    xdc_Void (*ti_sysbios_family_arm_cc26xx_Timer_setNextTick__E)(ti_sysbios_family_arm_cc26xx_Timer_Handle, xdc_UInt32);
    xdc_UInt32 (*ti_sysbios_family_arm_cc26xx_Timer_getMaxTicks__E)(ti_sysbios_family_arm_cc26xx_Timer_Handle);
    xdc_UInt64 (*ti_sysbios_family_arm_cc26xx_Timer_getCount64__E)(ti_sysbios_family_arm_cc26xx_Timer_Object *);
    xdc_Void (*ti_sysbios_family_arm_cc26xx_Timer_dynamicStub__E)(xdc_UArg);
    xdc_UInt32 (*ti_sysbios_family_arm_cc26xx_Timer_getCurrentTick__E)(ti_sysbios_family_arm_cc26xx_Timer_Handle, xdc_Bool);
    xdc_UInt32 (*ti_sysbios_family_arm_cc26xx_TimestampProvider_get32__E)(xdc_Void);
    xdc_Void (*xdc_runtime_Error_init__E)(xdc_runtime_Error_Block *);
    xdc_Char * (*xdc_runtime_System_formatNum__I)(xdc_Char *, xdc_UInt32, xdc_Int, xdc_Int);
} ROM_ExternFuncPtrs;

/* xdcRomExternFuncsPtr */
#pragma DATA_SECTION(ROM_externFuncPtrs, ".const:ROM_externFuncPtrs");
const ROM_ExternFuncPtrs ROM_externFuncPtrs = {
    xdc_runtime_Startup_getState__I,
    xdc_runtime_System_SupportProxy_Module__startupDone__S,
    xdc_runtime_System_SupportProxy_abort__E,
    xdc_runtime_System_SupportProxy_exit__E,
    xdc_runtime_System_SupportProxy_flush__E,
    xdc_runtime_System_SupportProxy_putch__E,
    xdc_runtime_System_SupportProxy_ready__E,
    ti_sysbios_family_arm_cc26xx_Timer_start__E,
    ti_sysbios_family_arm_cc26xx_Timer_initDevice__I,
    ti_sysbios_family_arm_cc26xx_Timer_setThreshold__I,
    ti_sysbios_family_arm_cc26xx_Timer_setNextTick__E,
    ti_sysbios_family_arm_cc26xx_Timer_getMaxTicks__E,
    ti_sysbios_family_arm_cc26xx_Timer_getCount64__E,
    ti_sysbios_family_arm_cc26xx_Timer_dynamicStub__E,
    ti_sysbios_family_arm_cc26xx_Timer_getCurrentTick__E,
    ti_sysbios_family_arm_cc26xx_TimestampProvider_get32__E,
    xdc_runtime_Error_init__E,
    xdc_runtime_System_formatNum__I,
};

/* xdcRomExternFuncsPtr */
#pragma DATA_SECTION(xdcRomExternFuncPtr, ".data:xdcRomExternFuncPtr");
const ROM_ExternFuncPtrs *xdcRomExternFuncPtr = &ROM_externFuncPtrs;



/*
 * ======== ti.sysbios.rom.cortexm.cc26xx.cc26x2v2.CC26xx TEMPLATE ========
 */





Void ti_sysbios_rom_cortexm_cc26xx_cc26x2v2_CC26xx_badRomRevision__E() __attribute__ ((noinline));
Void ti_sysbios_rom_cortexm_cc26xx_cc26x2v2_CC26xx_badRomRevision__E() {
	/* Loop here forever if application is built with wrong version of ROM image */
        while(1) {
#ifdef __clang__ 
            /* workaround CODEGEN-6288 */
            asm(" nop");
#endif
            ;
        }
}

Void ti_sysbios_rom_cortexm_cc26xx_cc26x2v2_CC26xx_checkRevision__E()
{
    if (*((UInt32 *)(268612608)) != 286529877) {
	ti_sysbios_rom_cortexm_cc26xx_cc26x2v2_CC26xx_badRomRevision__E();
    }
}


/*
 * ======== ti.sysbios.rts.MemAlloc TEMPLATE ========
 */



#if defined(__ti__) && !defined(__clang__)

#pragma FUNC_EXT_CALLED(malloc);
#pragma FUNC_EXT_CALLED(memalign);
#pragma FUNC_EXT_CALLED(free);
#pragma FUNC_EXT_CALLED(calloc);
#pragma FUNC_EXT_CALLED(realloc);
#pragma FUNC_EXT_CALLED(aligned_alloc);

#define ATTRIBUTE

#elif defined(__IAR_SYSTEMS_ICC__)

#define ATTRIBUTE

#else

#define ATTRIBUTE __attribute__ ((used))

#endif


#include <xdc/std.h>

#include <xdc/runtime/Memory.h>
#include <xdc/runtime/Error.h>

#include <string.h>

#if defined(__GNUC__) && !defined(__ti__)

#include <reent.h>

#endif

/*
 * Header is a union to make sure that the size is a power of 2.
 */
typedef union Header {
    struct {
        Ptr   actualBuf;
        SizeT size;
    } header;
    UArg pad[2];	/* 4 words on 28L, 8 bytes on most others */
} Header;

/*
 *  ======== ti_sysbios_rts_MemAlloc_alloc ========
 */
static Void *ti_sysbios_rts_MemAlloc_alloc(SizeT size)
{
    Header *packet;
    SizeT allocSize;
    xdc_runtime_Error_Block eb;

    allocSize = size + sizeof(Header);

    /*
     * If size is very large and allocSize overflows, the result will be
     * smaller than size. In this case, don't try to allocate.
     */
    if (allocSize < size) {
        return (NULL);
    }

    xdc_runtime_Error_init(&eb);

    packet = (Header *)xdc_runtime_Memory_alloc(NULL, allocSize, 0, &eb);

    if (packet == NULL) {
        return (NULL);
    }

    packet->header.actualBuf = (Ptr)packet;
    packet->header.size = allocSize;

    return (packet + 1);
}

/*
 *  ======== malloc ========
 */
Void ATTRIBUTE *malloc(SizeT size)
{
    return (ti_sysbios_rts_MemAlloc_alloc(size));
}

/*
 *  ======== memalign ========
 *  mirrors the memalign() function from the TI run-time library
 */
Void ATTRIBUTE *memalign(SizeT alignment, SizeT size)
{
    Header                      *packet;
    Void                        *tmp;
    xdc_runtime_Error_Block     eb;

    /* return NULL if size is 0, or alignment is not a power-of-2 */
    if (size == 0 || (alignment & (alignment - 1))) {
        return (NULL);
    }

    if (alignment < sizeof(Header)) {
        alignment = sizeof(Header);
    }

    xdc_runtime_Error_init(&eb);

    /*
     * Allocate 'align + size' so that we have room for the 'packet'
     * and can return an aligned buffer.
     */
    tmp = xdc_runtime_Memory_alloc(NULL, alignment + size, alignment, &eb);

    if (tmp == NULL) {
        return (NULL);
    }

    packet = (Header *)((char *)tmp + alignment - sizeof(Header));

    packet->header.actualBuf = tmp;
    packet->header.size = size + sizeof(Header);

    return (packet + 1);
}

/*
 *  ======== calloc ========
 */
Void ATTRIBUTE *calloc(SizeT nmemb, SizeT size)
{
    SizeT       nbytes;
    Ptr         retval;

    nbytes = nmemb * size;

    /* return NULL if there's an overflow */
    if (nmemb && size != (nbytes / nmemb)) {
        return (NULL);
    }

    retval = ti_sysbios_rts_MemAlloc_alloc(nbytes);
    if (retval != NULL) {
        (Void)memset(retval, (Int)'\0', nbytes);
    }

    return (retval);
}

/*
 *  ======== free ========
 */
Void ATTRIBUTE free(Void *ptr)
{
    Header      *packet;

    if (ptr != NULL) {
        packet = ((Header *)ptr) - 1;

        xdc_runtime_Memory_free(NULL, (Ptr)packet->header.actualBuf,
            (packet->header.size +
            ((char*)packet - (char*)packet->header.actualBuf)));
    }
}

/*
 *  ======== realloc ========
 */
Void ATTRIBUTE *realloc(Void *ptr, SizeT size)
{
    Ptr         retval;
    Header      *packet;
    SizeT       oldSize;

    if (ptr == NULL) {
        retval = malloc(size);
    }
    else if (size == 0) {
        free(ptr);
        retval = NULL;
    }
    else {
        packet = (Header *)ptr - 1;
        retval = malloc(size);
        if (retval != NULL) {
            oldSize = packet->header.size - sizeof(Header);
            (Void)memcpy(retval, ptr, (size < oldSize) ? size : oldSize);
            free(ptr);
        }
    }

    return (retval);
}

/*
 *  ======== aligned_alloc ========
 */
Void ATTRIBUTE *aligned_alloc(SizeT alignment, SizeT size)
{
    Void *retval;

    retval = memalign(alignment, size);

    return (retval);
}

#if defined(__GNUC__) && !defined(__ti__)

/*
 *  ======== _malloc_r ========
 */
Void ATTRIBUTE *_malloc_r(struct _reent *rptr, SizeT size)
{
    return malloc(size);
}

/*
 *  ======== _calloc_r ========
 */
Void ATTRIBUTE *_calloc_r(struct _reent *rptr, SizeT nmemb, SizeT size)
{
    return calloc(nmemb, size);
}

/*
 *  ======== _free_r ========
 */
Void ATTRIBUTE _free_r(struct _reent *rptr, Void *ptr)
{
    free(ptr);
}

/*
 *  ======== _realloc_r ========
 */
Void ATTRIBUTE *_realloc_r(struct _reent *rptr, Void *ptr, SizeT size)
{
    return realloc(ptr, size);
}

#endif


/*
 * ======== ti.sysbios.BIOS INITIALIZERS ========
 */


/* Module__diagsEnabled__C */
#pragma DATA_SECTION(ti_sysbios_BIOS_Module__diagsEnabled__C, ".const:ti_sysbios_BIOS_Module__diagsEnabled__C");
__FAR__ const CT__ti_sysbios_BIOS_Module__diagsEnabled ti_sysbios_BIOS_Module__diagsEnabled__C = (xdc_Bits32)0x90U;

/* Module__diagsIncluded__C */
#pragma DATA_SECTION(ti_sysbios_BIOS_Module__diagsIncluded__C, ".const:ti_sysbios_BIOS_Module__diagsIncluded__C");
__FAR__ const CT__ti_sysbios_BIOS_Module__diagsIncluded ti_sysbios_BIOS_Module__diagsIncluded__C = (xdc_Bits32)0x90U;

/* Module__diagsMask__C */
#pragma DATA_SECTION(ti_sysbios_BIOS_Module__diagsMask__C, ".const:ti_sysbios_BIOS_Module__diagsMask__C");
__FAR__ const CT__ti_sysbios_BIOS_Module__diagsMask ti_sysbios_BIOS_Module__diagsMask__C = ((const CT__ti_sysbios_BIOS_Module__diagsMask)NULL);

/* Module__gateObj__C */
#pragma DATA_SECTION(ti_sysbios_BIOS_Module__gateObj__C, ".const:ti_sysbios_BIOS_Module__gateObj__C");
__FAR__ const CT__ti_sysbios_BIOS_Module__gateObj ti_sysbios_BIOS_Module__gateObj__C = ((const CT__ti_sysbios_BIOS_Module__gateObj)NULL);

/* Module__gatePrms__C */
#pragma DATA_SECTION(ti_sysbios_BIOS_Module__gatePrms__C, ".const:ti_sysbios_BIOS_Module__gatePrms__C");
__FAR__ const CT__ti_sysbios_BIOS_Module__gatePrms ti_sysbios_BIOS_Module__gatePrms__C = ((const CT__ti_sysbios_BIOS_Module__gatePrms)NULL);

/* Module__id__C */
#pragma DATA_SECTION(ti_sysbios_BIOS_Module__id__C, ".const:ti_sysbios_BIOS_Module__id__C");
__FAR__ const CT__ti_sysbios_BIOS_Module__id ti_sysbios_BIOS_Module__id__C = (xdc_Bits16)0x22U;

/* Module__loggerDefined__C */
#pragma DATA_SECTION(ti_sysbios_BIOS_Module__loggerDefined__C, ".const:ti_sysbios_BIOS_Module__loggerDefined__C");
__FAR__ const CT__ti_sysbios_BIOS_Module__loggerDefined ti_sysbios_BIOS_Module__loggerDefined__C = 0;

/* Module__loggerObj__C */
#pragma DATA_SECTION(ti_sysbios_BIOS_Module__loggerObj__C, ".const:ti_sysbios_BIOS_Module__loggerObj__C");
__FAR__ const CT__ti_sysbios_BIOS_Module__loggerObj ti_sysbios_BIOS_Module__loggerObj__C = ((const CT__ti_sysbios_BIOS_Module__loggerObj)NULL);

/* Module__loggerFxn0__C */
#pragma DATA_SECTION(ti_sysbios_BIOS_Module__loggerFxn0__C, ".const:ti_sysbios_BIOS_Module__loggerFxn0__C");
__FAR__ const CT__ti_sysbios_BIOS_Module__loggerFxn0 ti_sysbios_BIOS_Module__loggerFxn0__C = ((const CT__ti_sysbios_BIOS_Module__loggerFxn0)NULL);

/* Module__loggerFxn1__C */
#pragma DATA_SECTION(ti_sysbios_BIOS_Module__loggerFxn1__C, ".const:ti_sysbios_BIOS_Module__loggerFxn1__C");
__FAR__ const CT__ti_sysbios_BIOS_Module__loggerFxn1 ti_sysbios_BIOS_Module__loggerFxn1__C = ((const CT__ti_sysbios_BIOS_Module__loggerFxn1)NULL);

/* Module__loggerFxn2__C */
#pragma DATA_SECTION(ti_sysbios_BIOS_Module__loggerFxn2__C, ".const:ti_sysbios_BIOS_Module__loggerFxn2__C");
__FAR__ const CT__ti_sysbios_BIOS_Module__loggerFxn2 ti_sysbios_BIOS_Module__loggerFxn2__C = ((const CT__ti_sysbios_BIOS_Module__loggerFxn2)NULL);

/* Module__loggerFxn4__C */
#pragma DATA_SECTION(ti_sysbios_BIOS_Module__loggerFxn4__C, ".const:ti_sysbios_BIOS_Module__loggerFxn4__C");
__FAR__ const CT__ti_sysbios_BIOS_Module__loggerFxn4 ti_sysbios_BIOS_Module__loggerFxn4__C = ((const CT__ti_sysbios_BIOS_Module__loggerFxn4)NULL);

/* Module__loggerFxn8__C */
#pragma DATA_SECTION(ti_sysbios_BIOS_Module__loggerFxn8__C, ".const:ti_sysbios_BIOS_Module__loggerFxn8__C");
__FAR__ const CT__ti_sysbios_BIOS_Module__loggerFxn8 ti_sysbios_BIOS_Module__loggerFxn8__C = ((const CT__ti_sysbios_BIOS_Module__loggerFxn8)NULL);

/* Object__count__C */
#pragma DATA_SECTION(ti_sysbios_BIOS_Object__count__C, ".const:ti_sysbios_BIOS_Object__count__C");
__FAR__ const CT__ti_sysbios_BIOS_Object__count ti_sysbios_BIOS_Object__count__C = 0;

/* Object__heap__C */
#pragma DATA_SECTION(ti_sysbios_BIOS_Object__heap__C, ".const:ti_sysbios_BIOS_Object__heap__C");
__FAR__ const CT__ti_sysbios_BIOS_Object__heap ti_sysbios_BIOS_Object__heap__C = NULL;

/* Object__sizeof__C */
#pragma DATA_SECTION(ti_sysbios_BIOS_Object__sizeof__C, ".const:ti_sysbios_BIOS_Object__sizeof__C");
__FAR__ const CT__ti_sysbios_BIOS_Object__sizeof ti_sysbios_BIOS_Object__sizeof__C = 0;

/* Object__table__C */
#pragma DATA_SECTION(ti_sysbios_BIOS_Object__table__C, ".const:ti_sysbios_BIOS_Object__table__C");
__FAR__ const CT__ti_sysbios_BIOS_Object__table ti_sysbios_BIOS_Object__table__C = NULL;

/* smpEnabled__C */
#pragma DATA_SECTION(ti_sysbios_BIOS_smpEnabled__C, ".const:ti_sysbios_BIOS_smpEnabled__C");
__FAR__ const CT__ti_sysbios_BIOS_smpEnabled ti_sysbios_BIOS_smpEnabled__C = 0;

/* cpuFreq__C */
#pragma DATA_SECTION(ti_sysbios_BIOS_cpuFreq__C, ".const:ti_sysbios_BIOS_cpuFreq__C");
__FAR__ const CT__ti_sysbios_BIOS_cpuFreq ti_sysbios_BIOS_cpuFreq__C = {
    (xdc_Bits32)0x0U,  /* hi */
    (xdc_Bits32)0x2dc6c00U,  /* lo */
};

/* runtimeCreatesEnabled__C */
#pragma DATA_SECTION(ti_sysbios_BIOS_runtimeCreatesEnabled__C, ".const:ti_sysbios_BIOS_runtimeCreatesEnabled__C");
__FAR__ const CT__ti_sysbios_BIOS_runtimeCreatesEnabled ti_sysbios_BIOS_runtimeCreatesEnabled__C = 1;

/* taskEnabled__C */
#pragma DATA_SECTION(ti_sysbios_BIOS_taskEnabled__C, ".const:ti_sysbios_BIOS_taskEnabled__C");
__FAR__ const CT__ti_sysbios_BIOS_taskEnabled ti_sysbios_BIOS_taskEnabled__C = 1;

/* swiEnabled__C */
#pragma DATA_SECTION(ti_sysbios_BIOS_swiEnabled__C, ".const:ti_sysbios_BIOS_swiEnabled__C");
__FAR__ const CT__ti_sysbios_BIOS_swiEnabled ti_sysbios_BIOS_swiEnabled__C = 1;

/* clockEnabled__C */
#pragma DATA_SECTION(ti_sysbios_BIOS_clockEnabled__C, ".const:ti_sysbios_BIOS_clockEnabled__C");
__FAR__ const CT__ti_sysbios_BIOS_clockEnabled ti_sysbios_BIOS_clockEnabled__C = 1;

/* heapSize__C */
#pragma DATA_SECTION(ti_sysbios_BIOS_heapSize__C, ".const:ti_sysbios_BIOS_heapSize__C");
__FAR__ const CT__ti_sysbios_BIOS_heapSize ti_sysbios_BIOS_heapSize__C = (xdc_SizeT)0x1000;

/* heapSection__C */
#pragma DATA_SECTION(ti_sysbios_BIOS_heapSection__C, ".const:ti_sysbios_BIOS_heapSection__C");
__FAR__ const CT__ti_sysbios_BIOS_heapSection ti_sysbios_BIOS_heapSection__C = 0;

/* heapTrackEnabled__C */
#pragma DATA_SECTION(ti_sysbios_BIOS_heapTrackEnabled__C, ".const:ti_sysbios_BIOS_heapTrackEnabled__C");
__FAR__ const CT__ti_sysbios_BIOS_heapTrackEnabled ti_sysbios_BIOS_heapTrackEnabled__C = 0;

/* setupSecureContext__C */
#pragma DATA_SECTION(ti_sysbios_BIOS_setupSecureContext__C, ".const:ti_sysbios_BIOS_setupSecureContext__C");
__FAR__ const CT__ti_sysbios_BIOS_setupSecureContext ti_sysbios_BIOS_setupSecureContext__C = 0;

/* useSK__C */
#pragma DATA_SECTION(ti_sysbios_BIOS_useSK__C, ".const:ti_sysbios_BIOS_useSK__C");
__FAR__ const CT__ti_sysbios_BIOS_useSK ti_sysbios_BIOS_useSK__C = 0;

/* installedErrorHook__C */
#pragma DATA_SECTION(ti_sysbios_BIOS_installedErrorHook__C, ".const:ti_sysbios_BIOS_installedErrorHook__C");
__FAR__ const CT__ti_sysbios_BIOS_installedErrorHook ti_sysbios_BIOS_installedErrorHook__C = ((const CT__ti_sysbios_BIOS_installedErrorHook)NULL);


/*
 * ======== ti.sysbios.BIOS_RtsGateProxy INITIALIZERS ========
 */


/*
 * ======== ti.sysbios.family.arm.cc26xx.Boot INITIALIZERS ========
 */

/* Module__diagsEnabled__C */
#pragma DATA_SECTION(ti_sysbios_family_arm_cc26xx_Boot_Module__diagsEnabled__C, ".const:ti_sysbios_family_arm_cc26xx_Boot_Module__diagsEnabled__C");
__FAR__ const CT__ti_sysbios_family_arm_cc26xx_Boot_Module__diagsEnabled ti_sysbios_family_arm_cc26xx_Boot_Module__diagsEnabled__C = (xdc_Bits32)0x90U;

/* Module__diagsIncluded__C */
#pragma DATA_SECTION(ti_sysbios_family_arm_cc26xx_Boot_Module__diagsIncluded__C, ".const:ti_sysbios_family_arm_cc26xx_Boot_Module__diagsIncluded__C");
__FAR__ const CT__ti_sysbios_family_arm_cc26xx_Boot_Module__diagsIncluded ti_sysbios_family_arm_cc26xx_Boot_Module__diagsIncluded__C = (xdc_Bits32)0x90U;

/* Module__diagsMask__C */
#pragma DATA_SECTION(ti_sysbios_family_arm_cc26xx_Boot_Module__diagsMask__C, ".const:ti_sysbios_family_arm_cc26xx_Boot_Module__diagsMask__C");
__FAR__ const CT__ti_sysbios_family_arm_cc26xx_Boot_Module__diagsMask ti_sysbios_family_arm_cc26xx_Boot_Module__diagsMask__C = ((const CT__ti_sysbios_family_arm_cc26xx_Boot_Module__diagsMask)NULL);

/* Module__gateObj__C */
#pragma DATA_SECTION(ti_sysbios_family_arm_cc26xx_Boot_Module__gateObj__C, ".const:ti_sysbios_family_arm_cc26xx_Boot_Module__gateObj__C");
__FAR__ const CT__ti_sysbios_family_arm_cc26xx_Boot_Module__gateObj ti_sysbios_family_arm_cc26xx_Boot_Module__gateObj__C = ((const CT__ti_sysbios_family_arm_cc26xx_Boot_Module__gateObj)NULL);

/* Module__gatePrms__C */
#pragma DATA_SECTION(ti_sysbios_family_arm_cc26xx_Boot_Module__gatePrms__C, ".const:ti_sysbios_family_arm_cc26xx_Boot_Module__gatePrms__C");
__FAR__ const CT__ti_sysbios_family_arm_cc26xx_Boot_Module__gatePrms ti_sysbios_family_arm_cc26xx_Boot_Module__gatePrms__C = ((const CT__ti_sysbios_family_arm_cc26xx_Boot_Module__gatePrms)NULL);

/* Module__id__C */
#pragma DATA_SECTION(ti_sysbios_family_arm_cc26xx_Boot_Module__id__C, ".const:ti_sysbios_family_arm_cc26xx_Boot_Module__id__C");
__FAR__ const CT__ti_sysbios_family_arm_cc26xx_Boot_Module__id ti_sysbios_family_arm_cc26xx_Boot_Module__id__C = (xdc_Bits16)0x27U;

/* Module__loggerDefined__C */
#pragma DATA_SECTION(ti_sysbios_family_arm_cc26xx_Boot_Module__loggerDefined__C, ".const:ti_sysbios_family_arm_cc26xx_Boot_Module__loggerDefined__C");
__FAR__ const CT__ti_sysbios_family_arm_cc26xx_Boot_Module__loggerDefined ti_sysbios_family_arm_cc26xx_Boot_Module__loggerDefined__C = 0;

/* Module__loggerObj__C */
#pragma DATA_SECTION(ti_sysbios_family_arm_cc26xx_Boot_Module__loggerObj__C, ".const:ti_sysbios_family_arm_cc26xx_Boot_Module__loggerObj__C");
__FAR__ const CT__ti_sysbios_family_arm_cc26xx_Boot_Module__loggerObj ti_sysbios_family_arm_cc26xx_Boot_Module__loggerObj__C = ((const CT__ti_sysbios_family_arm_cc26xx_Boot_Module__loggerObj)NULL);

/* Module__loggerFxn0__C */
#pragma DATA_SECTION(ti_sysbios_family_arm_cc26xx_Boot_Module__loggerFxn0__C, ".const:ti_sysbios_family_arm_cc26xx_Boot_Module__loggerFxn0__C");
__FAR__ const CT__ti_sysbios_family_arm_cc26xx_Boot_Module__loggerFxn0 ti_sysbios_family_arm_cc26xx_Boot_Module__loggerFxn0__C = ((const CT__ti_sysbios_family_arm_cc26xx_Boot_Module__loggerFxn0)NULL);

/* Module__loggerFxn1__C */
#pragma DATA_SECTION(ti_sysbios_family_arm_cc26xx_Boot_Module__loggerFxn1__C, ".const:ti_sysbios_family_arm_cc26xx_Boot_Module__loggerFxn1__C");
__FAR__ const CT__ti_sysbios_family_arm_cc26xx_Boot_Module__loggerFxn1 ti_sysbios_family_arm_cc26xx_Boot_Module__loggerFxn1__C = ((const CT__ti_sysbios_family_arm_cc26xx_Boot_Module__loggerFxn1)NULL);

/* Module__loggerFxn2__C */
#pragma DATA_SECTION(ti_sysbios_family_arm_cc26xx_Boot_Module__loggerFxn2__C, ".const:ti_sysbios_family_arm_cc26xx_Boot_Module__loggerFxn2__C");
__FAR__ const CT__ti_sysbios_family_arm_cc26xx_Boot_Module__loggerFxn2 ti_sysbios_family_arm_cc26xx_Boot_Module__loggerFxn2__C = ((const CT__ti_sysbios_family_arm_cc26xx_Boot_Module__loggerFxn2)NULL);

/* Module__loggerFxn4__C */
#pragma DATA_SECTION(ti_sysbios_family_arm_cc26xx_Boot_Module__loggerFxn4__C, ".const:ti_sysbios_family_arm_cc26xx_Boot_Module__loggerFxn4__C");
__FAR__ const CT__ti_sysbios_family_arm_cc26xx_Boot_Module__loggerFxn4 ti_sysbios_family_arm_cc26xx_Boot_Module__loggerFxn4__C = ((const CT__ti_sysbios_family_arm_cc26xx_Boot_Module__loggerFxn4)NULL);

/* Module__loggerFxn8__C */
#pragma DATA_SECTION(ti_sysbios_family_arm_cc26xx_Boot_Module__loggerFxn8__C, ".const:ti_sysbios_family_arm_cc26xx_Boot_Module__loggerFxn8__C");
__FAR__ const CT__ti_sysbios_family_arm_cc26xx_Boot_Module__loggerFxn8 ti_sysbios_family_arm_cc26xx_Boot_Module__loggerFxn8__C = ((const CT__ti_sysbios_family_arm_cc26xx_Boot_Module__loggerFxn8)NULL);

/* Object__count__C */
#pragma DATA_SECTION(ti_sysbios_family_arm_cc26xx_Boot_Object__count__C, ".const:ti_sysbios_family_arm_cc26xx_Boot_Object__count__C");
__FAR__ const CT__ti_sysbios_family_arm_cc26xx_Boot_Object__count ti_sysbios_family_arm_cc26xx_Boot_Object__count__C = 0;

/* Object__heap__C */
#pragma DATA_SECTION(ti_sysbios_family_arm_cc26xx_Boot_Object__heap__C, ".const:ti_sysbios_family_arm_cc26xx_Boot_Object__heap__C");
__FAR__ const CT__ti_sysbios_family_arm_cc26xx_Boot_Object__heap ti_sysbios_family_arm_cc26xx_Boot_Object__heap__C = NULL;

/* Object__sizeof__C */
#pragma DATA_SECTION(ti_sysbios_family_arm_cc26xx_Boot_Object__sizeof__C, ".const:ti_sysbios_family_arm_cc26xx_Boot_Object__sizeof__C");
__FAR__ const CT__ti_sysbios_family_arm_cc26xx_Boot_Object__sizeof ti_sysbios_family_arm_cc26xx_Boot_Object__sizeof__C = 0;

/* Object__table__C */
#pragma DATA_SECTION(ti_sysbios_family_arm_cc26xx_Boot_Object__table__C, ".const:ti_sysbios_family_arm_cc26xx_Boot_Object__table__C");
__FAR__ const CT__ti_sysbios_family_arm_cc26xx_Boot_Object__table ti_sysbios_family_arm_cc26xx_Boot_Object__table__C = NULL;


/*
 * ======== ti.sysbios.family.arm.cc26xx.Timer INITIALIZERS ========
 */


/* Object__PARAMS__C */
#pragma DATA_SECTION(ti_sysbios_family_arm_cc26xx_Timer_Object__PARAMS__C, ".const:ti_sysbios_family_arm_cc26xx_Timer_Object__PARAMS__C");
__FAR__ const ti_sysbios_family_arm_cc26xx_Timer_Params ti_sysbios_family_arm_cc26xx_Timer_Object__PARAMS__C = {
    sizeof (ti_sysbios_family_arm_cc26xx_Timer_Params), /* __size */
    NULL, /* __self */
    NULL, /* __fxns */
    (xdc_runtime_IInstance_Params*)&ti_sysbios_family_arm_cc26xx_Timer_Object__PARAMS__C.__iprms, /* instance */
    ti_sysbios_interfaces_ITimer_RunMode_CONTINUOUS,  /* runMode */
    ti_sysbios_interfaces_ITimer_StartMode_AUTO,  /* startMode */
    ((xdc_UArg)NULL),  /* arg */
    (xdc_UInt32)0x0U,  /* period */
    ti_sysbios_interfaces_ITimer_PeriodType_MICROSECS,  /* periodType */
    {
        (xdc_Bits32)0x0U,  /* hi */
        (xdc_Bits32)0x0U,  /* lo */
    },  /* extFreq */
    ((ti_sysbios_family_arm_m3_Hwi_Params*)NULL),  /* hwiParams */
    {
        sizeof (xdc_runtime_IInstance_Params), /* __size */
        0,  /* name */
    },  /* instance */
};

/* Module__root__V */
ti_sysbios_family_arm_cc26xx_Timer_Module__ ti_sysbios_family_arm_cc26xx_Timer_Module__root__V = {
    {&ti_sysbios_family_arm_cc26xx_Timer_Module__root__V.link,  /* link.next */
    &ti_sysbios_family_arm_cc26xx_Timer_Module__root__V.link},  /* link.prev */
};

/* Object__table__V */
ti_sysbios_family_arm_cc26xx_Timer_Object__ ti_sysbios_family_arm_cc26xx_Timer_Object__table__V[1] = {
    {/* instance#0 */
        0,
        1,  /* staticInst */
        (xdc_Int)0x0,  /* id */
        ti_sysbios_interfaces_ITimer_StartMode_AUTO,  /* startMode */
        (xdc_UInt32)0xa7c5U,  /* period */
        ((xdc_UArg)NULL),  /* arg */
        ((xdc_Void(*)(xdc_UArg f_arg0))(ti_sysbios_knl_Clock_doTick__I)),  /* tickFxn */
        {
            (xdc_Bits32)0x0U,  /* hi */
            (xdc_Bits32)0x10000U,  /* lo */
        },  /* frequency */
        (ti_sysbios_family_arm_m3_Hwi_Handle)&ti_sysbios_family_arm_m3_Hwi_Object__table__V[0],  /* hwi */
        (xdc_UInt64)0xa7c5U,  /* period64 */
        (xdc_UInt64)0x0U,  /* savedCurrCount */
        (xdc_UInt64)0xa7c5U,  /* prevThreshold */
        (xdc_UInt64)0xa7c5U,  /* nextThreshold */
    },
};

/* Module__diagsEnabled__C */
#pragma DATA_SECTION(ti_sysbios_family_arm_cc26xx_Timer_Module__diagsEnabled__C, ".const:ti_sysbios_family_arm_cc26xx_Timer_Module__diagsEnabled__C");
__FAR__ const CT__ti_sysbios_family_arm_cc26xx_Timer_Module__diagsEnabled ti_sysbios_family_arm_cc26xx_Timer_Module__diagsEnabled__C = (xdc_Bits32)0x90U;

/* Module__diagsIncluded__C */
#pragma DATA_SECTION(ti_sysbios_family_arm_cc26xx_Timer_Module__diagsIncluded__C, ".const:ti_sysbios_family_arm_cc26xx_Timer_Module__diagsIncluded__C");
__FAR__ const CT__ti_sysbios_family_arm_cc26xx_Timer_Module__diagsIncluded ti_sysbios_family_arm_cc26xx_Timer_Module__diagsIncluded__C = (xdc_Bits32)0x90U;

/* Module__diagsMask__C */
#pragma DATA_SECTION(ti_sysbios_family_arm_cc26xx_Timer_Module__diagsMask__C, ".const:ti_sysbios_family_arm_cc26xx_Timer_Module__diagsMask__C");
__FAR__ const CT__ti_sysbios_family_arm_cc26xx_Timer_Module__diagsMask ti_sysbios_family_arm_cc26xx_Timer_Module__diagsMask__C = ((const CT__ti_sysbios_family_arm_cc26xx_Timer_Module__diagsMask)NULL);

/* Module__gateObj__C */
#pragma DATA_SECTION(ti_sysbios_family_arm_cc26xx_Timer_Module__gateObj__C, ".const:ti_sysbios_family_arm_cc26xx_Timer_Module__gateObj__C");
__FAR__ const CT__ti_sysbios_family_arm_cc26xx_Timer_Module__gateObj ti_sysbios_family_arm_cc26xx_Timer_Module__gateObj__C = ((const CT__ti_sysbios_family_arm_cc26xx_Timer_Module__gateObj)NULL);

/* Module__gatePrms__C */
#pragma DATA_SECTION(ti_sysbios_family_arm_cc26xx_Timer_Module__gatePrms__C, ".const:ti_sysbios_family_arm_cc26xx_Timer_Module__gatePrms__C");
__FAR__ const CT__ti_sysbios_family_arm_cc26xx_Timer_Module__gatePrms ti_sysbios_family_arm_cc26xx_Timer_Module__gatePrms__C = ((const CT__ti_sysbios_family_arm_cc26xx_Timer_Module__gatePrms)NULL);

/* Module__loggerDefined__C */
#pragma DATA_SECTION(ti_sysbios_family_arm_cc26xx_Timer_Module__loggerDefined__C, ".const:ti_sysbios_family_arm_cc26xx_Timer_Module__loggerDefined__C");
__FAR__ const CT__ti_sysbios_family_arm_cc26xx_Timer_Module__loggerDefined ti_sysbios_family_arm_cc26xx_Timer_Module__loggerDefined__C = 0;

/* Module__loggerObj__C */
#pragma DATA_SECTION(ti_sysbios_family_arm_cc26xx_Timer_Module__loggerObj__C, ".const:ti_sysbios_family_arm_cc26xx_Timer_Module__loggerObj__C");
__FAR__ const CT__ti_sysbios_family_arm_cc26xx_Timer_Module__loggerObj ti_sysbios_family_arm_cc26xx_Timer_Module__loggerObj__C = ((const CT__ti_sysbios_family_arm_cc26xx_Timer_Module__loggerObj)NULL);

/* Module__loggerFxn0__C */
#pragma DATA_SECTION(ti_sysbios_family_arm_cc26xx_Timer_Module__loggerFxn0__C, ".const:ti_sysbios_family_arm_cc26xx_Timer_Module__loggerFxn0__C");
__FAR__ const CT__ti_sysbios_family_arm_cc26xx_Timer_Module__loggerFxn0 ti_sysbios_family_arm_cc26xx_Timer_Module__loggerFxn0__C = ((const CT__ti_sysbios_family_arm_cc26xx_Timer_Module__loggerFxn0)NULL);

/* Module__loggerFxn1__C */
#pragma DATA_SECTION(ti_sysbios_family_arm_cc26xx_Timer_Module__loggerFxn1__C, ".const:ti_sysbios_family_arm_cc26xx_Timer_Module__loggerFxn1__C");
__FAR__ const CT__ti_sysbios_family_arm_cc26xx_Timer_Module__loggerFxn1 ti_sysbios_family_arm_cc26xx_Timer_Module__loggerFxn1__C = ((const CT__ti_sysbios_family_arm_cc26xx_Timer_Module__loggerFxn1)NULL);

/* Module__loggerFxn2__C */
#pragma DATA_SECTION(ti_sysbios_family_arm_cc26xx_Timer_Module__loggerFxn2__C, ".const:ti_sysbios_family_arm_cc26xx_Timer_Module__loggerFxn2__C");
__FAR__ const CT__ti_sysbios_family_arm_cc26xx_Timer_Module__loggerFxn2 ti_sysbios_family_arm_cc26xx_Timer_Module__loggerFxn2__C = ((const CT__ti_sysbios_family_arm_cc26xx_Timer_Module__loggerFxn2)NULL);

/* Module__loggerFxn4__C */
#pragma DATA_SECTION(ti_sysbios_family_arm_cc26xx_Timer_Module__loggerFxn4__C, ".const:ti_sysbios_family_arm_cc26xx_Timer_Module__loggerFxn4__C");
__FAR__ const CT__ti_sysbios_family_arm_cc26xx_Timer_Module__loggerFxn4 ti_sysbios_family_arm_cc26xx_Timer_Module__loggerFxn4__C = ((const CT__ti_sysbios_family_arm_cc26xx_Timer_Module__loggerFxn4)NULL);

/* Module__loggerFxn8__C */
#pragma DATA_SECTION(ti_sysbios_family_arm_cc26xx_Timer_Module__loggerFxn8__C, ".const:ti_sysbios_family_arm_cc26xx_Timer_Module__loggerFxn8__C");
__FAR__ const CT__ti_sysbios_family_arm_cc26xx_Timer_Module__loggerFxn8 ti_sysbios_family_arm_cc26xx_Timer_Module__loggerFxn8__C = ((const CT__ti_sysbios_family_arm_cc26xx_Timer_Module__loggerFxn8)NULL);

/* Object__count__C */
#pragma DATA_SECTION(ti_sysbios_family_arm_cc26xx_Timer_Object__count__C, ".const:ti_sysbios_family_arm_cc26xx_Timer_Object__count__C");
__FAR__ const CT__ti_sysbios_family_arm_cc26xx_Timer_Object__count ti_sysbios_family_arm_cc26xx_Timer_Object__count__C = 1;

/* Object__heap__C */
#pragma DATA_SECTION(ti_sysbios_family_arm_cc26xx_Timer_Object__heap__C, ".const:ti_sysbios_family_arm_cc26xx_Timer_Object__heap__C");
__FAR__ const CT__ti_sysbios_family_arm_cc26xx_Timer_Object__heap ti_sysbios_family_arm_cc26xx_Timer_Object__heap__C = NULL;

/* Object__sizeof__C */
#pragma DATA_SECTION(ti_sysbios_family_arm_cc26xx_Timer_Object__sizeof__C, ".const:ti_sysbios_family_arm_cc26xx_Timer_Object__sizeof__C");
__FAR__ const CT__ti_sysbios_family_arm_cc26xx_Timer_Object__sizeof ti_sysbios_family_arm_cc26xx_Timer_Object__sizeof__C = sizeof(ti_sysbios_family_arm_cc26xx_Timer_Object__);

/* Object__table__C */
#pragma DATA_SECTION(ti_sysbios_family_arm_cc26xx_Timer_Object__table__C, ".const:ti_sysbios_family_arm_cc26xx_Timer_Object__table__C");
__FAR__ const CT__ti_sysbios_family_arm_cc26xx_Timer_Object__table ti_sysbios_family_arm_cc26xx_Timer_Object__table__C = ti_sysbios_family_arm_cc26xx_Timer_Object__table__V;

/* E_invalidTimer__C */
#pragma DATA_SECTION(ti_sysbios_family_arm_cc26xx_Timer_E_invalidTimer__C, ".const:ti_sysbios_family_arm_cc26xx_Timer_E_invalidTimer__C");
__FAR__ const CT__ti_sysbios_family_arm_cc26xx_Timer_E_invalidTimer ti_sysbios_family_arm_cc26xx_Timer_E_invalidTimer__C = (((xdc_runtime_Error_Id)30) << 16 | 0U);

/* E_notAvailable__C */
#pragma DATA_SECTION(ti_sysbios_family_arm_cc26xx_Timer_E_notAvailable__C, ".const:ti_sysbios_family_arm_cc26xx_Timer_E_notAvailable__C");
__FAR__ const CT__ti_sysbios_family_arm_cc26xx_Timer_E_notAvailable ti_sysbios_family_arm_cc26xx_Timer_E_notAvailable__C = (((xdc_runtime_Error_Id)31) << 16 | 0U);

/* E_cannotSupport__C */
#pragma DATA_SECTION(ti_sysbios_family_arm_cc26xx_Timer_E_cannotSupport__C, ".const:ti_sysbios_family_arm_cc26xx_Timer_E_cannotSupport__C");
__FAR__ const CT__ti_sysbios_family_arm_cc26xx_Timer_E_cannotSupport ti_sysbios_family_arm_cc26xx_Timer_E_cannotSupport__C = (((xdc_runtime_Error_Id)32) << 16 | 0U);

/* anyMask__C */
#pragma DATA_SECTION(ti_sysbios_family_arm_cc26xx_Timer_anyMask__C, ".const:ti_sysbios_family_arm_cc26xx_Timer_anyMask__C");
__FAR__ const CT__ti_sysbios_family_arm_cc26xx_Timer_anyMask ti_sysbios_family_arm_cc26xx_Timer_anyMask__C = (xdc_UInt)0x1U;


/*
 * ======== ti.sysbios.family.arm.cc26xx.TimestampProvider INITIALIZERS ========
 */


/* Module__diagsEnabled__C */
#pragma DATA_SECTION(ti_sysbios_family_arm_cc26xx_TimestampProvider_Module__diagsEnabled__C, ".const:ti_sysbios_family_arm_cc26xx_TimestampProvider_Module__diagsEnabled__C");
__FAR__ const CT__ti_sysbios_family_arm_cc26xx_TimestampProvider_Module__diagsEnabled ti_sysbios_family_arm_cc26xx_TimestampProvider_Module__diagsEnabled__C = (xdc_Bits32)0x10U;

/* Module__diagsIncluded__C */
#pragma DATA_SECTION(ti_sysbios_family_arm_cc26xx_TimestampProvider_Module__diagsIncluded__C, ".const:ti_sysbios_family_arm_cc26xx_TimestampProvider_Module__diagsIncluded__C");
__FAR__ const CT__ti_sysbios_family_arm_cc26xx_TimestampProvider_Module__diagsIncluded ti_sysbios_family_arm_cc26xx_TimestampProvider_Module__diagsIncluded__C = (xdc_Bits32)0x10U;

/* Module__diagsMask__C */
#pragma DATA_SECTION(ti_sysbios_family_arm_cc26xx_TimestampProvider_Module__diagsMask__C, ".const:ti_sysbios_family_arm_cc26xx_TimestampProvider_Module__diagsMask__C");
__FAR__ const CT__ti_sysbios_family_arm_cc26xx_TimestampProvider_Module__diagsMask ti_sysbios_family_arm_cc26xx_TimestampProvider_Module__diagsMask__C = ((const CT__ti_sysbios_family_arm_cc26xx_TimestampProvider_Module__diagsMask)NULL);

/* Module__gateObj__C */
#pragma DATA_SECTION(ti_sysbios_family_arm_cc26xx_TimestampProvider_Module__gateObj__C, ".const:ti_sysbios_family_arm_cc26xx_TimestampProvider_Module__gateObj__C");
__FAR__ const CT__ti_sysbios_family_arm_cc26xx_TimestampProvider_Module__gateObj ti_sysbios_family_arm_cc26xx_TimestampProvider_Module__gateObj__C = ((const CT__ti_sysbios_family_arm_cc26xx_TimestampProvider_Module__gateObj)NULL);

/* Module__gatePrms__C */
#pragma DATA_SECTION(ti_sysbios_family_arm_cc26xx_TimestampProvider_Module__gatePrms__C, ".const:ti_sysbios_family_arm_cc26xx_TimestampProvider_Module__gatePrms__C");
__FAR__ const CT__ti_sysbios_family_arm_cc26xx_TimestampProvider_Module__gatePrms ti_sysbios_family_arm_cc26xx_TimestampProvider_Module__gatePrms__C = ((const CT__ti_sysbios_family_arm_cc26xx_TimestampProvider_Module__gatePrms)NULL);

/* Module__id__C */
#pragma DATA_SECTION(ti_sysbios_family_arm_cc26xx_TimestampProvider_Module__id__C, ".const:ti_sysbios_family_arm_cc26xx_TimestampProvider_Module__id__C");
__FAR__ const CT__ti_sysbios_family_arm_cc26xx_TimestampProvider_Module__id ti_sysbios_family_arm_cc26xx_TimestampProvider_Module__id__C = (xdc_Bits16)0x29U;

/* Module__loggerDefined__C */
#pragma DATA_SECTION(ti_sysbios_family_arm_cc26xx_TimestampProvider_Module__loggerDefined__C, ".const:ti_sysbios_family_arm_cc26xx_TimestampProvider_Module__loggerDefined__C");
__FAR__ const CT__ti_sysbios_family_arm_cc26xx_TimestampProvider_Module__loggerDefined ti_sysbios_family_arm_cc26xx_TimestampProvider_Module__loggerDefined__C = 0;

/* Module__loggerObj__C */
#pragma DATA_SECTION(ti_sysbios_family_arm_cc26xx_TimestampProvider_Module__loggerObj__C, ".const:ti_sysbios_family_arm_cc26xx_TimestampProvider_Module__loggerObj__C");
__FAR__ const CT__ti_sysbios_family_arm_cc26xx_TimestampProvider_Module__loggerObj ti_sysbios_family_arm_cc26xx_TimestampProvider_Module__loggerObj__C = ((const CT__ti_sysbios_family_arm_cc26xx_TimestampProvider_Module__loggerObj)NULL);

/* Module__loggerFxn0__C */
#pragma DATA_SECTION(ti_sysbios_family_arm_cc26xx_TimestampProvider_Module__loggerFxn0__C, ".const:ti_sysbios_family_arm_cc26xx_TimestampProvider_Module__loggerFxn0__C");
__FAR__ const CT__ti_sysbios_family_arm_cc26xx_TimestampProvider_Module__loggerFxn0 ti_sysbios_family_arm_cc26xx_TimestampProvider_Module__loggerFxn0__C = ((const CT__ti_sysbios_family_arm_cc26xx_TimestampProvider_Module__loggerFxn0)NULL);

/* Module__loggerFxn1__C */
#pragma DATA_SECTION(ti_sysbios_family_arm_cc26xx_TimestampProvider_Module__loggerFxn1__C, ".const:ti_sysbios_family_arm_cc26xx_TimestampProvider_Module__loggerFxn1__C");
__FAR__ const CT__ti_sysbios_family_arm_cc26xx_TimestampProvider_Module__loggerFxn1 ti_sysbios_family_arm_cc26xx_TimestampProvider_Module__loggerFxn1__C = ((const CT__ti_sysbios_family_arm_cc26xx_TimestampProvider_Module__loggerFxn1)NULL);

/* Module__loggerFxn2__C */
#pragma DATA_SECTION(ti_sysbios_family_arm_cc26xx_TimestampProvider_Module__loggerFxn2__C, ".const:ti_sysbios_family_arm_cc26xx_TimestampProvider_Module__loggerFxn2__C");
__FAR__ const CT__ti_sysbios_family_arm_cc26xx_TimestampProvider_Module__loggerFxn2 ti_sysbios_family_arm_cc26xx_TimestampProvider_Module__loggerFxn2__C = ((const CT__ti_sysbios_family_arm_cc26xx_TimestampProvider_Module__loggerFxn2)NULL);

/* Module__loggerFxn4__C */
#pragma DATA_SECTION(ti_sysbios_family_arm_cc26xx_TimestampProvider_Module__loggerFxn4__C, ".const:ti_sysbios_family_arm_cc26xx_TimestampProvider_Module__loggerFxn4__C");
__FAR__ const CT__ti_sysbios_family_arm_cc26xx_TimestampProvider_Module__loggerFxn4 ti_sysbios_family_arm_cc26xx_TimestampProvider_Module__loggerFxn4__C = ((const CT__ti_sysbios_family_arm_cc26xx_TimestampProvider_Module__loggerFxn4)NULL);

/* Module__loggerFxn8__C */
#pragma DATA_SECTION(ti_sysbios_family_arm_cc26xx_TimestampProvider_Module__loggerFxn8__C, ".const:ti_sysbios_family_arm_cc26xx_TimestampProvider_Module__loggerFxn8__C");
__FAR__ const CT__ti_sysbios_family_arm_cc26xx_TimestampProvider_Module__loggerFxn8 ti_sysbios_family_arm_cc26xx_TimestampProvider_Module__loggerFxn8__C = ((const CT__ti_sysbios_family_arm_cc26xx_TimestampProvider_Module__loggerFxn8)NULL);

/* Object__count__C */
#pragma DATA_SECTION(ti_sysbios_family_arm_cc26xx_TimestampProvider_Object__count__C, ".const:ti_sysbios_family_arm_cc26xx_TimestampProvider_Object__count__C");
__FAR__ const CT__ti_sysbios_family_arm_cc26xx_TimestampProvider_Object__count ti_sysbios_family_arm_cc26xx_TimestampProvider_Object__count__C = 0;

/* Object__heap__C */
#pragma DATA_SECTION(ti_sysbios_family_arm_cc26xx_TimestampProvider_Object__heap__C, ".const:ti_sysbios_family_arm_cc26xx_TimestampProvider_Object__heap__C");
__FAR__ const CT__ti_sysbios_family_arm_cc26xx_TimestampProvider_Object__heap ti_sysbios_family_arm_cc26xx_TimestampProvider_Object__heap__C = NULL;

/* Object__sizeof__C */
#pragma DATA_SECTION(ti_sysbios_family_arm_cc26xx_TimestampProvider_Object__sizeof__C, ".const:ti_sysbios_family_arm_cc26xx_TimestampProvider_Object__sizeof__C");
__FAR__ const CT__ti_sysbios_family_arm_cc26xx_TimestampProvider_Object__sizeof ti_sysbios_family_arm_cc26xx_TimestampProvider_Object__sizeof__C = 0;

/* Object__table__C */
#pragma DATA_SECTION(ti_sysbios_family_arm_cc26xx_TimestampProvider_Object__table__C, ".const:ti_sysbios_family_arm_cc26xx_TimestampProvider_Object__table__C");
__FAR__ const CT__ti_sysbios_family_arm_cc26xx_TimestampProvider_Object__table ti_sysbios_family_arm_cc26xx_TimestampProvider_Object__table__C = NULL;

/* timerId__C */
#pragma DATA_SECTION(ti_sysbios_family_arm_cc26xx_TimestampProvider_timerId__C, ".const:ti_sysbios_family_arm_cc26xx_TimestampProvider_timerId__C");
__FAR__ const CT__ti_sysbios_family_arm_cc26xx_TimestampProvider_timerId ti_sysbios_family_arm_cc26xx_TimestampProvider_timerId__C = (xdc_UInt)0x0U;


/*
 * ======== ti.sysbios.family.arm.m3.Hwi INITIALIZERS ========
 */


/* Object__PARAMS__C */
#pragma DATA_SECTION(ti_sysbios_family_arm_m3_Hwi_Object__PARAMS__C, ".const:ti_sysbios_family_arm_m3_Hwi_Object__PARAMS__C");
__FAR__ const ti_sysbios_family_arm_m3_Hwi_Params ti_sysbios_family_arm_m3_Hwi_Object__PARAMS__C = {
    sizeof (ti_sysbios_family_arm_m3_Hwi_Params), /* __size */
    NULL, /* __self */
    NULL, /* __fxns */
    (xdc_runtime_IInstance_Params*)&ti_sysbios_family_arm_m3_Hwi_Object__PARAMS__C.__iprms, /* instance */
    ti_sysbios_interfaces_IHwi_MaskingOption_LOWER,  /* maskSetting */
    ((xdc_UArg)(0x0)),  /* arg */
    1,  /* enableInt */
    (xdc_Int)(-0x0 - 1),  /* eventId */
    (xdc_Int)0xff,  /* priority */
    1,  /* useDispatcher */
    {
        sizeof (xdc_runtime_IInstance_Params), /* __size */
        0,  /* name */
    },  /* instance */
};

/* Module__root__V */
ti_sysbios_family_arm_m3_Hwi_Module__ ti_sysbios_family_arm_m3_Hwi_Module__root__V = {
    {&ti_sysbios_family_arm_m3_Hwi_Module__root__V.link,  /* link.next */
    &ti_sysbios_family_arm_m3_Hwi_Module__root__V.link},  /* link.prev */
};

/* Object__table__V */
ti_sysbios_family_arm_m3_Hwi_Object__ ti_sysbios_family_arm_m3_Hwi_Object__table__V[1] = {
    {/* instance#0 */
        0,
        ((xdc_UArg)(0x0)),  /* arg */
        ((xdc_Void(*)(xdc_UArg f_arg0))(ti_sysbios_family_arm_cc26xx_Timer_dynamicStub__E)),  /* fxn */
        ((xdc_UArg)(0x3)),  /* irp */
        (xdc_UInt8)0xffU,  /* priority */
        (xdc_Int16)0x14,  /* intNum */
        ((void*)0),  /* hookEnv */
    },
};

/* --> ti_sysbios_family_arm_m3_Hwi_Module_State_0_excActive__A */
__T1_ti_sysbios_family_arm_m3_Hwi_Module_State__excActive ti_sysbios_family_arm_m3_Hwi_Module_State_0_excActive__A[1] = {
    0,  /* [0] */
};

/* --> ti_sysbios_family_arm_m3_Hwi_Module_State_0_excContext__A */
__T1_ti_sysbios_family_arm_m3_Hwi_Module_State__excContext ti_sysbios_family_arm_m3_Hwi_Module_State_0_excContext__A[1] = {
    ((ti_sysbios_family_arm_m3_Hwi_ExcContext*)NULL),  /* [0] */
};

/* --> ti_sysbios_family_arm_m3_Hwi_Module_State_0_excStack__A */
__T1_ti_sysbios_family_arm_m3_Hwi_Module_State__excStack ti_sysbios_family_arm_m3_Hwi_Module_State_0_excStack__A[1] = {
    ((xdc_Ptr)NULL),  /* [0] */
};

/* --> ti_sysbios_family_arm_m3_Hwi_excHookFuncs__A */
#pragma DATA_SECTION(ti_sysbios_family_arm_m3_Hwi_excHookFuncs__A, ".const:ti_sysbios_family_arm_m3_Hwi_excHookFuncs__A");
const __T1_ti_sysbios_family_arm_m3_Hwi_excHookFuncs ti_sysbios_family_arm_m3_Hwi_excHookFuncs__A[2] = {
    ((xdc_Void(*)(ti_sysbios_family_arm_m3_Hwi_ExcContext* f_arg0))NULL),  /* [0] */
    ((xdc_Void(*)(ti_sysbios_family_arm_m3_Hwi_ExcContext* f_arg0))NULL),  /* [1] */
};

/* Module__diagsEnabled__C */
#pragma DATA_SECTION(ti_sysbios_family_arm_m3_Hwi_Module__diagsEnabled__C, ".const:ti_sysbios_family_arm_m3_Hwi_Module__diagsEnabled__C");
__FAR__ const CT__ti_sysbios_family_arm_m3_Hwi_Module__diagsEnabled ti_sysbios_family_arm_m3_Hwi_Module__diagsEnabled__C = (xdc_Bits32)0x90U;

/* Module__diagsIncluded__C */
#pragma DATA_SECTION(ti_sysbios_family_arm_m3_Hwi_Module__diagsIncluded__C, ".const:ti_sysbios_family_arm_m3_Hwi_Module__diagsIncluded__C");
__FAR__ const CT__ti_sysbios_family_arm_m3_Hwi_Module__diagsIncluded ti_sysbios_family_arm_m3_Hwi_Module__diagsIncluded__C = (xdc_Bits32)0x90U;

/* Module__diagsMask__C */
#pragma DATA_SECTION(ti_sysbios_family_arm_m3_Hwi_Module__diagsMask__C, ".const:ti_sysbios_family_arm_m3_Hwi_Module__diagsMask__C");
__FAR__ const CT__ti_sysbios_family_arm_m3_Hwi_Module__diagsMask ti_sysbios_family_arm_m3_Hwi_Module__diagsMask__C = ((const CT__ti_sysbios_family_arm_m3_Hwi_Module__diagsMask)NULL);

/* Module__gateObj__C */
#pragma DATA_SECTION(ti_sysbios_family_arm_m3_Hwi_Module__gateObj__C, ".const:ti_sysbios_family_arm_m3_Hwi_Module__gateObj__C");
__FAR__ const CT__ti_sysbios_family_arm_m3_Hwi_Module__gateObj ti_sysbios_family_arm_m3_Hwi_Module__gateObj__C = ((const CT__ti_sysbios_family_arm_m3_Hwi_Module__gateObj)NULL);

/* Module__gatePrms__C */
#pragma DATA_SECTION(ti_sysbios_family_arm_m3_Hwi_Module__gatePrms__C, ".const:ti_sysbios_family_arm_m3_Hwi_Module__gatePrms__C");
__FAR__ const CT__ti_sysbios_family_arm_m3_Hwi_Module__gatePrms ti_sysbios_family_arm_m3_Hwi_Module__gatePrms__C = ((const CT__ti_sysbios_family_arm_m3_Hwi_Module__gatePrms)NULL);

/* Module__loggerDefined__C */
#pragma DATA_SECTION(ti_sysbios_family_arm_m3_Hwi_Module__loggerDefined__C, ".const:ti_sysbios_family_arm_m3_Hwi_Module__loggerDefined__C");
__FAR__ const CT__ti_sysbios_family_arm_m3_Hwi_Module__loggerDefined ti_sysbios_family_arm_m3_Hwi_Module__loggerDefined__C = 0;

/* Module__loggerObj__C */
#pragma DATA_SECTION(ti_sysbios_family_arm_m3_Hwi_Module__loggerObj__C, ".const:ti_sysbios_family_arm_m3_Hwi_Module__loggerObj__C");
__FAR__ const CT__ti_sysbios_family_arm_m3_Hwi_Module__loggerObj ti_sysbios_family_arm_m3_Hwi_Module__loggerObj__C = ((const CT__ti_sysbios_family_arm_m3_Hwi_Module__loggerObj)NULL);

/* Module__loggerFxn0__C */
#pragma DATA_SECTION(ti_sysbios_family_arm_m3_Hwi_Module__loggerFxn0__C, ".const:ti_sysbios_family_arm_m3_Hwi_Module__loggerFxn0__C");
__FAR__ const CT__ti_sysbios_family_arm_m3_Hwi_Module__loggerFxn0 ti_sysbios_family_arm_m3_Hwi_Module__loggerFxn0__C = ((const CT__ti_sysbios_family_arm_m3_Hwi_Module__loggerFxn0)NULL);

/* Module__loggerFxn1__C */
#pragma DATA_SECTION(ti_sysbios_family_arm_m3_Hwi_Module__loggerFxn1__C, ".const:ti_sysbios_family_arm_m3_Hwi_Module__loggerFxn1__C");
__FAR__ const CT__ti_sysbios_family_arm_m3_Hwi_Module__loggerFxn1 ti_sysbios_family_arm_m3_Hwi_Module__loggerFxn1__C = ((const CT__ti_sysbios_family_arm_m3_Hwi_Module__loggerFxn1)NULL);

/* Module__loggerFxn2__C */
#pragma DATA_SECTION(ti_sysbios_family_arm_m3_Hwi_Module__loggerFxn2__C, ".const:ti_sysbios_family_arm_m3_Hwi_Module__loggerFxn2__C");
__FAR__ const CT__ti_sysbios_family_arm_m3_Hwi_Module__loggerFxn2 ti_sysbios_family_arm_m3_Hwi_Module__loggerFxn2__C = ((const CT__ti_sysbios_family_arm_m3_Hwi_Module__loggerFxn2)NULL);

/* Module__loggerFxn4__C */
#pragma DATA_SECTION(ti_sysbios_family_arm_m3_Hwi_Module__loggerFxn4__C, ".const:ti_sysbios_family_arm_m3_Hwi_Module__loggerFxn4__C");
__FAR__ const CT__ti_sysbios_family_arm_m3_Hwi_Module__loggerFxn4 ti_sysbios_family_arm_m3_Hwi_Module__loggerFxn4__C = ((const CT__ti_sysbios_family_arm_m3_Hwi_Module__loggerFxn4)NULL);

/* Module__loggerFxn8__C */
#pragma DATA_SECTION(ti_sysbios_family_arm_m3_Hwi_Module__loggerFxn8__C, ".const:ti_sysbios_family_arm_m3_Hwi_Module__loggerFxn8__C");
__FAR__ const CT__ti_sysbios_family_arm_m3_Hwi_Module__loggerFxn8 ti_sysbios_family_arm_m3_Hwi_Module__loggerFxn8__C = ((const CT__ti_sysbios_family_arm_m3_Hwi_Module__loggerFxn8)NULL);

/* Object__heap__C */
#pragma DATA_SECTION(ti_sysbios_family_arm_m3_Hwi_Object__heap__C, ".const:ti_sysbios_family_arm_m3_Hwi_Object__heap__C");
__FAR__ const CT__ti_sysbios_family_arm_m3_Hwi_Object__heap ti_sysbios_family_arm_m3_Hwi_Object__heap__C = NULL;

/* Object__sizeof__C */
#pragma DATA_SECTION(ti_sysbios_family_arm_m3_Hwi_Object__sizeof__C, ".const:ti_sysbios_family_arm_m3_Hwi_Object__sizeof__C");
__FAR__ const CT__ti_sysbios_family_arm_m3_Hwi_Object__sizeof ti_sysbios_family_arm_m3_Hwi_Object__sizeof__C = sizeof(ti_sysbios_family_arm_m3_Hwi_Object__);

/* dispatcherAutoNestingSupport__C */
#pragma DATA_SECTION(ti_sysbios_family_arm_m3_Hwi_dispatcherAutoNestingSupport__C, ".const:ti_sysbios_family_arm_m3_Hwi_dispatcherAutoNestingSupport__C");
__FAR__ const CT__ti_sysbios_family_arm_m3_Hwi_dispatcherAutoNestingSupport ti_sysbios_family_arm_m3_Hwi_dispatcherAutoNestingSupport__C = 1;

/* dispatcherSwiSupport__C */
#pragma DATA_SECTION(ti_sysbios_family_arm_m3_Hwi_dispatcherSwiSupport__C, ".const:ti_sysbios_family_arm_m3_Hwi_dispatcherSwiSupport__C");
__FAR__ const CT__ti_sysbios_family_arm_m3_Hwi_dispatcherSwiSupport ti_sysbios_family_arm_m3_Hwi_dispatcherSwiSupport__C = 1;

/* dispatcherTaskSupport__C */
#pragma DATA_SECTION(ti_sysbios_family_arm_m3_Hwi_dispatcherTaskSupport__C, ".const:ti_sysbios_family_arm_m3_Hwi_dispatcherTaskSupport__C");
__FAR__ const CT__ti_sysbios_family_arm_m3_Hwi_dispatcherTaskSupport ti_sysbios_family_arm_m3_Hwi_dispatcherTaskSupport__C = 1;

/* dispatcherIrpTrackingSupport__C */
#pragma DATA_SECTION(ti_sysbios_family_arm_m3_Hwi_dispatcherIrpTrackingSupport__C, ".const:ti_sysbios_family_arm_m3_Hwi_dispatcherIrpTrackingSupport__C");
__FAR__ const CT__ti_sysbios_family_arm_m3_Hwi_dispatcherIrpTrackingSupport ti_sysbios_family_arm_m3_Hwi_dispatcherIrpTrackingSupport__C = 1;

/* NUM_PRIORITIES__C */
#pragma DATA_SECTION(ti_sysbios_family_arm_m3_Hwi_NUM_PRIORITIES__C, ".const:ti_sysbios_family_arm_m3_Hwi_NUM_PRIORITIES__C");
__FAR__ const CT__ti_sysbios_family_arm_m3_Hwi_NUM_PRIORITIES ti_sysbios_family_arm_m3_Hwi_NUM_PRIORITIES__C = (xdc_Int)0x8;

/* LM_begin__C */
#pragma DATA_SECTION(ti_sysbios_family_arm_m3_Hwi_LM_begin__C, ".const:ti_sysbios_family_arm_m3_Hwi_LM_begin__C");
__FAR__ const CT__ti_sysbios_family_arm_m3_Hwi_LM_begin ti_sysbios_family_arm_m3_Hwi_LM_begin__C = (((xdc_runtime_Log_Event)32) << 16 | 768);

/* LD_end__C */
#pragma DATA_SECTION(ti_sysbios_family_arm_m3_Hwi_LD_end__C, ".const:ti_sysbios_family_arm_m3_Hwi_LD_end__C");
__FAR__ const CT__ti_sysbios_family_arm_m3_Hwi_LD_end ti_sysbios_family_arm_m3_Hwi_LD_end__C = (((xdc_runtime_Log_Event)33) << 16 | 512);

/* A_unsupportedMaskingOption__C */
#pragma DATA_SECTION(ti_sysbios_family_arm_m3_Hwi_A_unsupportedMaskingOption__C, ".const:ti_sysbios_family_arm_m3_Hwi_A_unsupportedMaskingOption__C");
__FAR__ const CT__ti_sysbios_family_arm_m3_Hwi_A_unsupportedMaskingOption ti_sysbios_family_arm_m3_Hwi_A_unsupportedMaskingOption__C = (((xdc_runtime_Assert_Id)0) << 16 | 16);

/* E_badIntNum__C */
#pragma DATA_SECTION(ti_sysbios_family_arm_m3_Hwi_E_badIntNum__C, ".const:ti_sysbios_family_arm_m3_Hwi_E_badIntNum__C");
__FAR__ const CT__ti_sysbios_family_arm_m3_Hwi_E_badIntNum ti_sysbios_family_arm_m3_Hwi_E_badIntNum__C = (((xdc_runtime_Error_Id)14) << 16 | 0U);

/* E_exception__C */
#pragma DATA_SECTION(ti_sysbios_family_arm_m3_Hwi_E_exception__C, ".const:ti_sysbios_family_arm_m3_Hwi_E_exception__C");
__FAR__ const CT__ti_sysbios_family_arm_m3_Hwi_E_exception ti_sysbios_family_arm_m3_Hwi_E_exception__C = (((xdc_runtime_Error_Id)17) << 16 | 0U);

/* excHookFunc__C */
#pragma DATA_SECTION(ti_sysbios_family_arm_m3_Hwi_excHookFunc__C, ".const:ti_sysbios_family_arm_m3_Hwi_excHookFunc__C");
__FAR__ const CT__ti_sysbios_family_arm_m3_Hwi_excHookFunc ti_sysbios_family_arm_m3_Hwi_excHookFunc__C = ((const CT__ti_sysbios_family_arm_m3_Hwi_excHookFunc)NULL);

/* disablePriority__C */
#pragma DATA_SECTION(ti_sysbios_family_arm_m3_Hwi_disablePriority__C, ".const:ti_sysbios_family_arm_m3_Hwi_disablePriority__C");
__FAR__ const CT__ti_sysbios_family_arm_m3_Hwi_disablePriority ti_sysbios_family_arm_m3_Hwi_disablePriority__C = (xdc_UInt)0x20U;

/* swiDisable__C */
#pragma DATA_SECTION(ti_sysbios_family_arm_m3_Hwi_swiDisable__C, ".const:ti_sysbios_family_arm_m3_Hwi_swiDisable__C");
__FAR__ const CT__ti_sysbios_family_arm_m3_Hwi_swiDisable ti_sysbios_family_arm_m3_Hwi_swiDisable__C = ((const CT__ti_sysbios_family_arm_m3_Hwi_swiDisable)(ti_sysbios_knl_Swi_disable__E));

/* swiRestore__C */
#pragma DATA_SECTION(ti_sysbios_family_arm_m3_Hwi_swiRestore__C, ".const:ti_sysbios_family_arm_m3_Hwi_swiRestore__C");
__FAR__ const CT__ti_sysbios_family_arm_m3_Hwi_swiRestore ti_sysbios_family_arm_m3_Hwi_swiRestore__C = ((const CT__ti_sysbios_family_arm_m3_Hwi_swiRestore)(ti_sysbios_knl_Swi_restore__E));

/* swiRestoreHwi__C */
#pragma DATA_SECTION(ti_sysbios_family_arm_m3_Hwi_swiRestoreHwi__C, ".const:ti_sysbios_family_arm_m3_Hwi_swiRestoreHwi__C");
__FAR__ const CT__ti_sysbios_family_arm_m3_Hwi_swiRestoreHwi ti_sysbios_family_arm_m3_Hwi_swiRestoreHwi__C = ((const CT__ti_sysbios_family_arm_m3_Hwi_swiRestoreHwi)(ti_sysbios_knl_Swi_restoreHwi__E));

/* taskDisable__C */
#pragma DATA_SECTION(ti_sysbios_family_arm_m3_Hwi_taskDisable__C, ".const:ti_sysbios_family_arm_m3_Hwi_taskDisable__C");
__FAR__ const CT__ti_sysbios_family_arm_m3_Hwi_taskDisable ti_sysbios_family_arm_m3_Hwi_taskDisable__C = ((const CT__ti_sysbios_family_arm_m3_Hwi_taskDisable)(ti_sysbios_knl_Task_disable__E));

/* taskRestoreHwi__C */
#pragma DATA_SECTION(ti_sysbios_family_arm_m3_Hwi_taskRestoreHwi__C, ".const:ti_sysbios_family_arm_m3_Hwi_taskRestoreHwi__C");
__FAR__ const CT__ti_sysbios_family_arm_m3_Hwi_taskRestoreHwi ti_sysbios_family_arm_m3_Hwi_taskRestoreHwi__C = ((const CT__ti_sysbios_family_arm_m3_Hwi_taskRestoreHwi)(ti_sysbios_knl_Task_restoreHwi__E));

/* hooks__C */
#pragma DATA_SECTION(ti_sysbios_family_arm_m3_Hwi_hooks__C, ".const:ti_sysbios_family_arm_m3_Hwi_hooks__C");
__FAR__ const CT__ti_sysbios_family_arm_m3_Hwi_hooks ti_sysbios_family_arm_m3_Hwi_hooks__C = {0, 0};


/*
 * ======== ti.sysbios.family.arm.m3.IntrinsicsSupport INITIALIZERS ========
 */

/* Module__diagsEnabled__C */
#pragma DATA_SECTION(ti_sysbios_family_arm_m3_IntrinsicsSupport_Module__diagsEnabled__C, ".const:ti_sysbios_family_arm_m3_IntrinsicsSupport_Module__diagsEnabled__C");
__FAR__ const CT__ti_sysbios_family_arm_m3_IntrinsicsSupport_Module__diagsEnabled ti_sysbios_family_arm_m3_IntrinsicsSupport_Module__diagsEnabled__C = (xdc_Bits32)0x90U;

/* Module__diagsIncluded__C */
#pragma DATA_SECTION(ti_sysbios_family_arm_m3_IntrinsicsSupport_Module__diagsIncluded__C, ".const:ti_sysbios_family_arm_m3_IntrinsicsSupport_Module__diagsIncluded__C");
__FAR__ const CT__ti_sysbios_family_arm_m3_IntrinsicsSupport_Module__diagsIncluded ti_sysbios_family_arm_m3_IntrinsicsSupport_Module__diagsIncluded__C = (xdc_Bits32)0x90U;

/* Module__diagsMask__C */
#pragma DATA_SECTION(ti_sysbios_family_arm_m3_IntrinsicsSupport_Module__diagsMask__C, ".const:ti_sysbios_family_arm_m3_IntrinsicsSupport_Module__diagsMask__C");
__FAR__ const CT__ti_sysbios_family_arm_m3_IntrinsicsSupport_Module__diagsMask ti_sysbios_family_arm_m3_IntrinsicsSupport_Module__diagsMask__C = ((const CT__ti_sysbios_family_arm_m3_IntrinsicsSupport_Module__diagsMask)NULL);

/* Module__gateObj__C */
#pragma DATA_SECTION(ti_sysbios_family_arm_m3_IntrinsicsSupport_Module__gateObj__C, ".const:ti_sysbios_family_arm_m3_IntrinsicsSupport_Module__gateObj__C");
__FAR__ const CT__ti_sysbios_family_arm_m3_IntrinsicsSupport_Module__gateObj ti_sysbios_family_arm_m3_IntrinsicsSupport_Module__gateObj__C = ((const CT__ti_sysbios_family_arm_m3_IntrinsicsSupport_Module__gateObj)NULL);

/* Module__gatePrms__C */
#pragma DATA_SECTION(ti_sysbios_family_arm_m3_IntrinsicsSupport_Module__gatePrms__C, ".const:ti_sysbios_family_arm_m3_IntrinsicsSupport_Module__gatePrms__C");
__FAR__ const CT__ti_sysbios_family_arm_m3_IntrinsicsSupport_Module__gatePrms ti_sysbios_family_arm_m3_IntrinsicsSupport_Module__gatePrms__C = ((const CT__ti_sysbios_family_arm_m3_IntrinsicsSupport_Module__gatePrms)NULL);

/* Module__id__C */
#pragma DATA_SECTION(ti_sysbios_family_arm_m3_IntrinsicsSupport_Module__id__C, ".const:ti_sysbios_family_arm_m3_IntrinsicsSupport_Module__id__C");
__FAR__ const CT__ti_sysbios_family_arm_m3_IntrinsicsSupport_Module__id ti_sysbios_family_arm_m3_IntrinsicsSupport_Module__id__C = (xdc_Bits16)0x25U;

/* Module__loggerDefined__C */
#pragma DATA_SECTION(ti_sysbios_family_arm_m3_IntrinsicsSupport_Module__loggerDefined__C, ".const:ti_sysbios_family_arm_m3_IntrinsicsSupport_Module__loggerDefined__C");
__FAR__ const CT__ti_sysbios_family_arm_m3_IntrinsicsSupport_Module__loggerDefined ti_sysbios_family_arm_m3_IntrinsicsSupport_Module__loggerDefined__C = 0;

/* Module__loggerObj__C */
#pragma DATA_SECTION(ti_sysbios_family_arm_m3_IntrinsicsSupport_Module__loggerObj__C, ".const:ti_sysbios_family_arm_m3_IntrinsicsSupport_Module__loggerObj__C");
__FAR__ const CT__ti_sysbios_family_arm_m3_IntrinsicsSupport_Module__loggerObj ti_sysbios_family_arm_m3_IntrinsicsSupport_Module__loggerObj__C = ((const CT__ti_sysbios_family_arm_m3_IntrinsicsSupport_Module__loggerObj)NULL);

/* Module__loggerFxn0__C */
#pragma DATA_SECTION(ti_sysbios_family_arm_m3_IntrinsicsSupport_Module__loggerFxn0__C, ".const:ti_sysbios_family_arm_m3_IntrinsicsSupport_Module__loggerFxn0__C");
__FAR__ const CT__ti_sysbios_family_arm_m3_IntrinsicsSupport_Module__loggerFxn0 ti_sysbios_family_arm_m3_IntrinsicsSupport_Module__loggerFxn0__C = ((const CT__ti_sysbios_family_arm_m3_IntrinsicsSupport_Module__loggerFxn0)NULL);

/* Module__loggerFxn1__C */
#pragma DATA_SECTION(ti_sysbios_family_arm_m3_IntrinsicsSupport_Module__loggerFxn1__C, ".const:ti_sysbios_family_arm_m3_IntrinsicsSupport_Module__loggerFxn1__C");
__FAR__ const CT__ti_sysbios_family_arm_m3_IntrinsicsSupport_Module__loggerFxn1 ti_sysbios_family_arm_m3_IntrinsicsSupport_Module__loggerFxn1__C = ((const CT__ti_sysbios_family_arm_m3_IntrinsicsSupport_Module__loggerFxn1)NULL);

/* Module__loggerFxn2__C */
#pragma DATA_SECTION(ti_sysbios_family_arm_m3_IntrinsicsSupport_Module__loggerFxn2__C, ".const:ti_sysbios_family_arm_m3_IntrinsicsSupport_Module__loggerFxn2__C");
__FAR__ const CT__ti_sysbios_family_arm_m3_IntrinsicsSupport_Module__loggerFxn2 ti_sysbios_family_arm_m3_IntrinsicsSupport_Module__loggerFxn2__C = ((const CT__ti_sysbios_family_arm_m3_IntrinsicsSupport_Module__loggerFxn2)NULL);

/* Module__loggerFxn4__C */
#pragma DATA_SECTION(ti_sysbios_family_arm_m3_IntrinsicsSupport_Module__loggerFxn4__C, ".const:ti_sysbios_family_arm_m3_IntrinsicsSupport_Module__loggerFxn4__C");
__FAR__ const CT__ti_sysbios_family_arm_m3_IntrinsicsSupport_Module__loggerFxn4 ti_sysbios_family_arm_m3_IntrinsicsSupport_Module__loggerFxn4__C = ((const CT__ti_sysbios_family_arm_m3_IntrinsicsSupport_Module__loggerFxn4)NULL);

/* Module__loggerFxn8__C */
#pragma DATA_SECTION(ti_sysbios_family_arm_m3_IntrinsicsSupport_Module__loggerFxn8__C, ".const:ti_sysbios_family_arm_m3_IntrinsicsSupport_Module__loggerFxn8__C");
__FAR__ const CT__ti_sysbios_family_arm_m3_IntrinsicsSupport_Module__loggerFxn8 ti_sysbios_family_arm_m3_IntrinsicsSupport_Module__loggerFxn8__C = ((const CT__ti_sysbios_family_arm_m3_IntrinsicsSupport_Module__loggerFxn8)NULL);

/* Object__count__C */
#pragma DATA_SECTION(ti_sysbios_family_arm_m3_IntrinsicsSupport_Object__count__C, ".const:ti_sysbios_family_arm_m3_IntrinsicsSupport_Object__count__C");
__FAR__ const CT__ti_sysbios_family_arm_m3_IntrinsicsSupport_Object__count ti_sysbios_family_arm_m3_IntrinsicsSupport_Object__count__C = 0;

/* Object__heap__C */
#pragma DATA_SECTION(ti_sysbios_family_arm_m3_IntrinsicsSupport_Object__heap__C, ".const:ti_sysbios_family_arm_m3_IntrinsicsSupport_Object__heap__C");
__FAR__ const CT__ti_sysbios_family_arm_m3_IntrinsicsSupport_Object__heap ti_sysbios_family_arm_m3_IntrinsicsSupport_Object__heap__C = NULL;

/* Object__sizeof__C */
#pragma DATA_SECTION(ti_sysbios_family_arm_m3_IntrinsicsSupport_Object__sizeof__C, ".const:ti_sysbios_family_arm_m3_IntrinsicsSupport_Object__sizeof__C");
__FAR__ const CT__ti_sysbios_family_arm_m3_IntrinsicsSupport_Object__sizeof ti_sysbios_family_arm_m3_IntrinsicsSupport_Object__sizeof__C = 0;

/* Object__table__C */
#pragma DATA_SECTION(ti_sysbios_family_arm_m3_IntrinsicsSupport_Object__table__C, ".const:ti_sysbios_family_arm_m3_IntrinsicsSupport_Object__table__C");
__FAR__ const CT__ti_sysbios_family_arm_m3_IntrinsicsSupport_Object__table ti_sysbios_family_arm_m3_IntrinsicsSupport_Object__table__C = NULL;


/*
 * ======== ti.sysbios.family.arm.m3.TaskSupport INITIALIZERS ========
 */

/* Module__diagsEnabled__C */
#pragma DATA_SECTION(ti_sysbios_family_arm_m3_TaskSupport_Module__diagsEnabled__C, ".const:ti_sysbios_family_arm_m3_TaskSupport_Module__diagsEnabled__C");
__FAR__ const CT__ti_sysbios_family_arm_m3_TaskSupport_Module__diagsEnabled ti_sysbios_family_arm_m3_TaskSupport_Module__diagsEnabled__C = (xdc_Bits32)0x90U;

/* Module__diagsIncluded__C */
#pragma DATA_SECTION(ti_sysbios_family_arm_m3_TaskSupport_Module__diagsIncluded__C, ".const:ti_sysbios_family_arm_m3_TaskSupport_Module__diagsIncluded__C");
__FAR__ const CT__ti_sysbios_family_arm_m3_TaskSupport_Module__diagsIncluded ti_sysbios_family_arm_m3_TaskSupport_Module__diagsIncluded__C = (xdc_Bits32)0x90U;
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
